danbates2/emonDC/emonDCmini/emonBike v0.2 BOARD BOTTOM.png

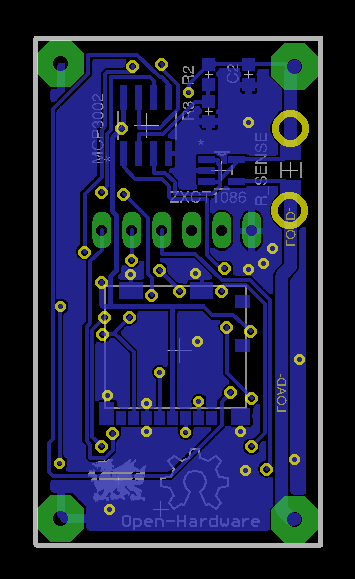
emonDCmini/emonBike v0.2 BOARD BOTTOM.png
