danbates2/emonDC/emonDCmini/emonBike v0.2 BOARD TOP.png

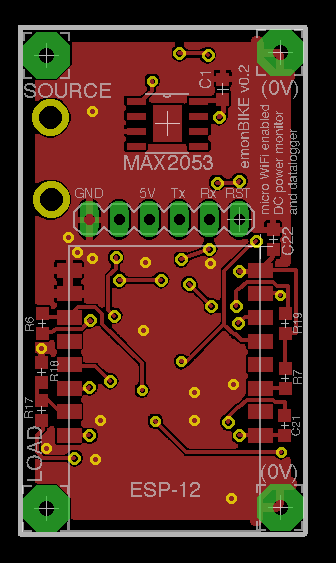
emonDCmini/emonBike v0.2 BOARD TOP.png
