danbates2/emonDC/emonDCmini/emonBike v0.2 SCHEMATIC.png

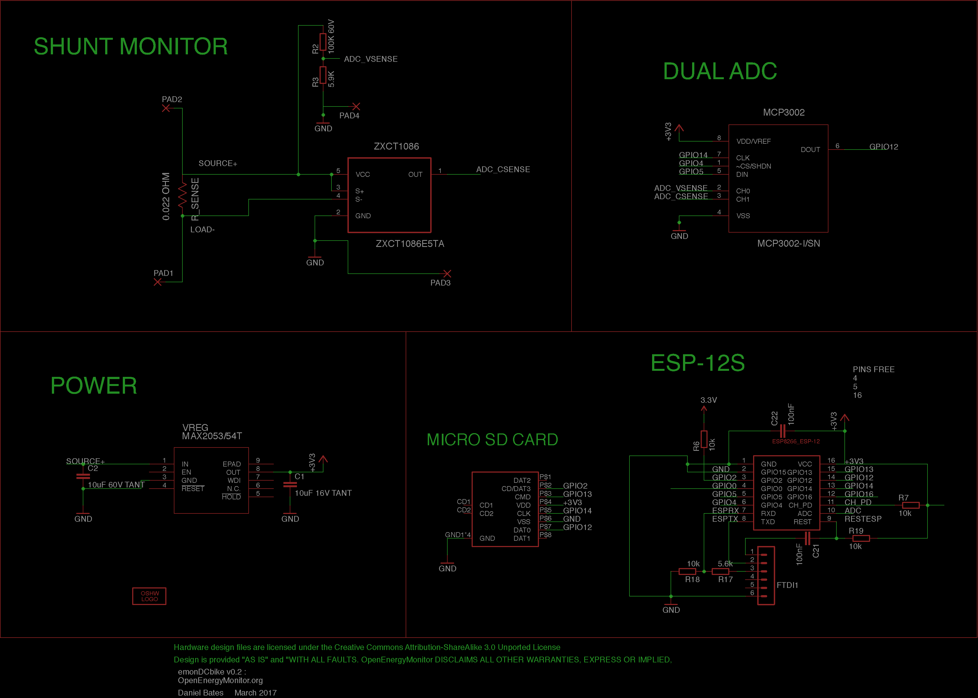
emonDCmini/emonBike v0.2 SCHEMATIC.png
