danbates2/emonDC/images/3dprinted_case_1.jpg

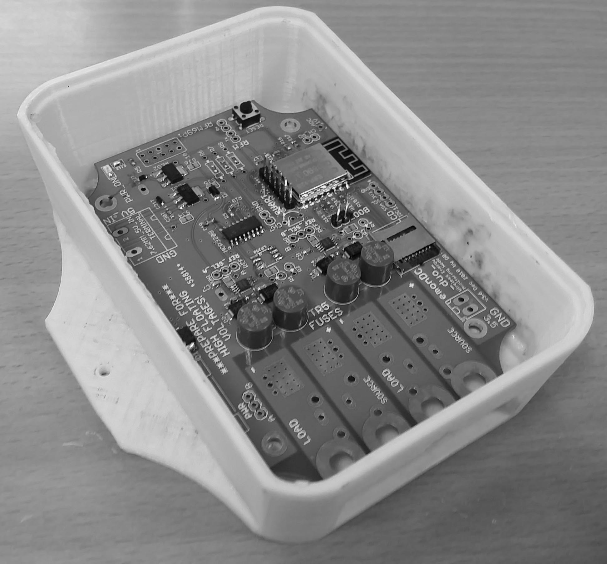
images/3dprinted_case_1.jpg
