danbates2/emonDC/images/buck_reg_blue.jpg

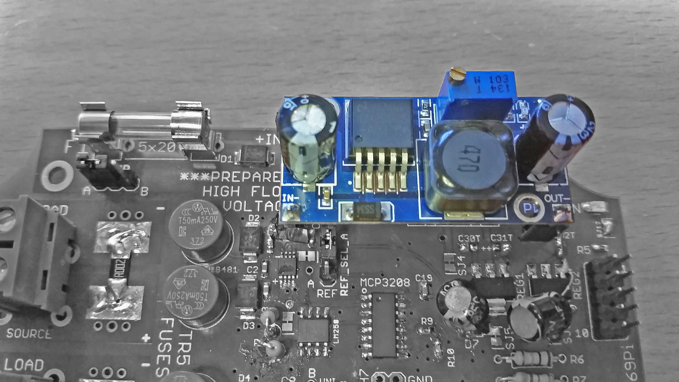
images/buck_reg_blue.jpg
