danbates2/emonDC/images/buck_reg_green.jpg

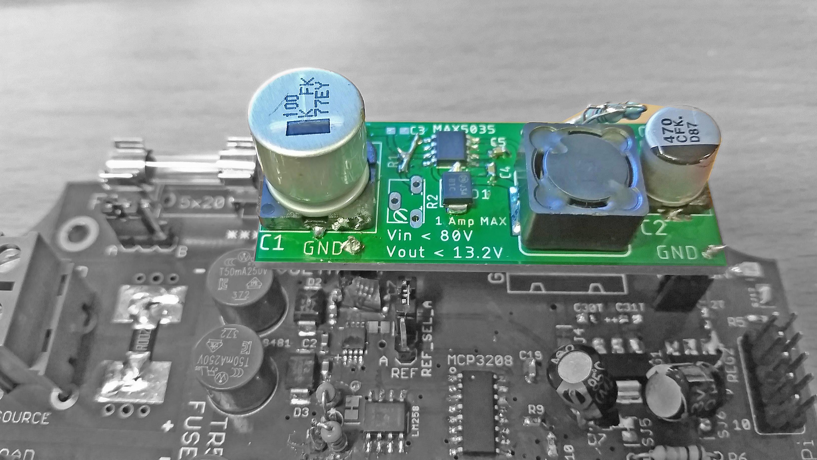
images/buck_reg_green.jpg
