danbates2/emonDC/images/buckreg-hysteresis.jpg

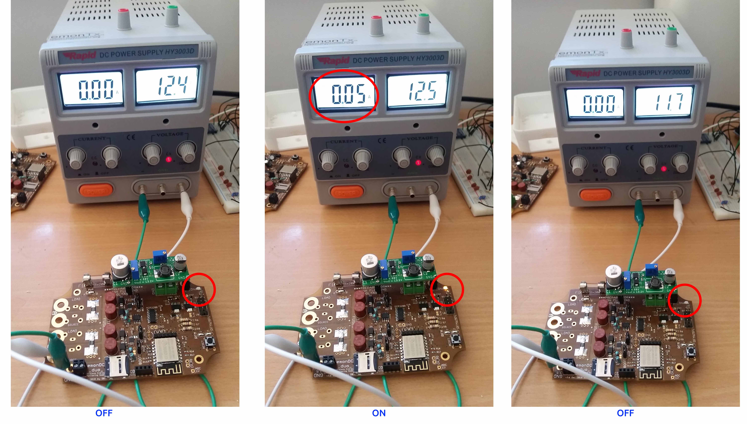
images/buckreg-hysteresis.jpg
