danbates2/emonDC/images/enclosures.jpg

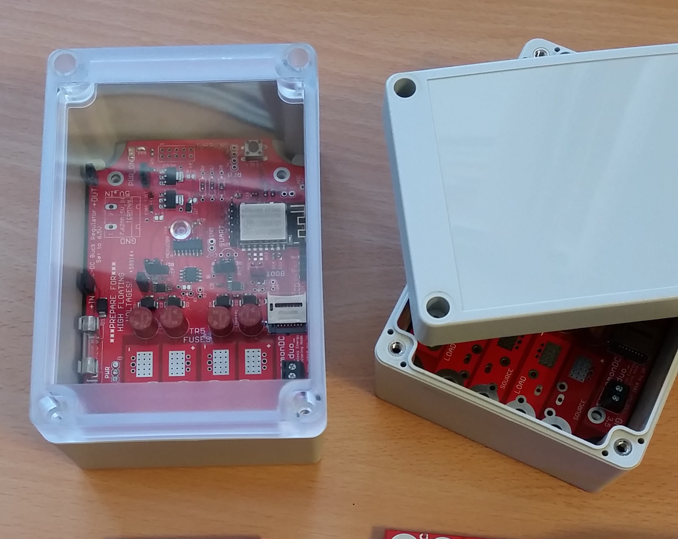
images/enclosures.jpg
