danbates2/emonDC/images/LM2596_dc-dc_buck_module.jpg

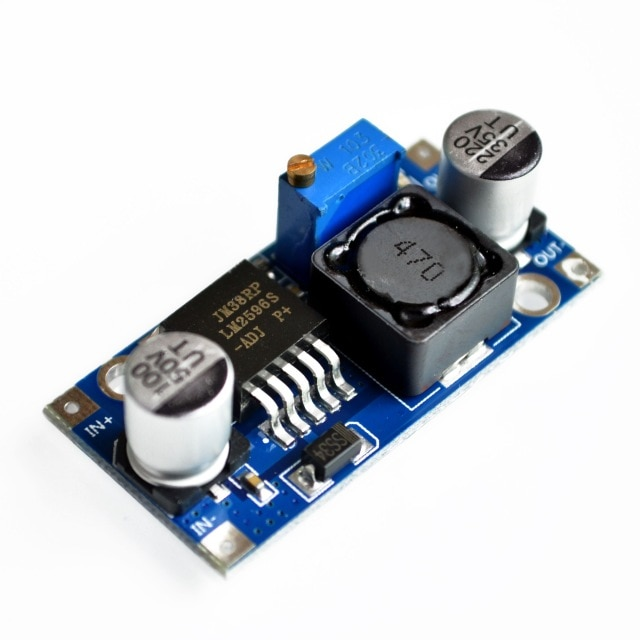
images/LM2596_dc-dc_buck_module.jpg
