danbates2/emonDC/images/shoot1/clear_enclosure_standing2.JPG

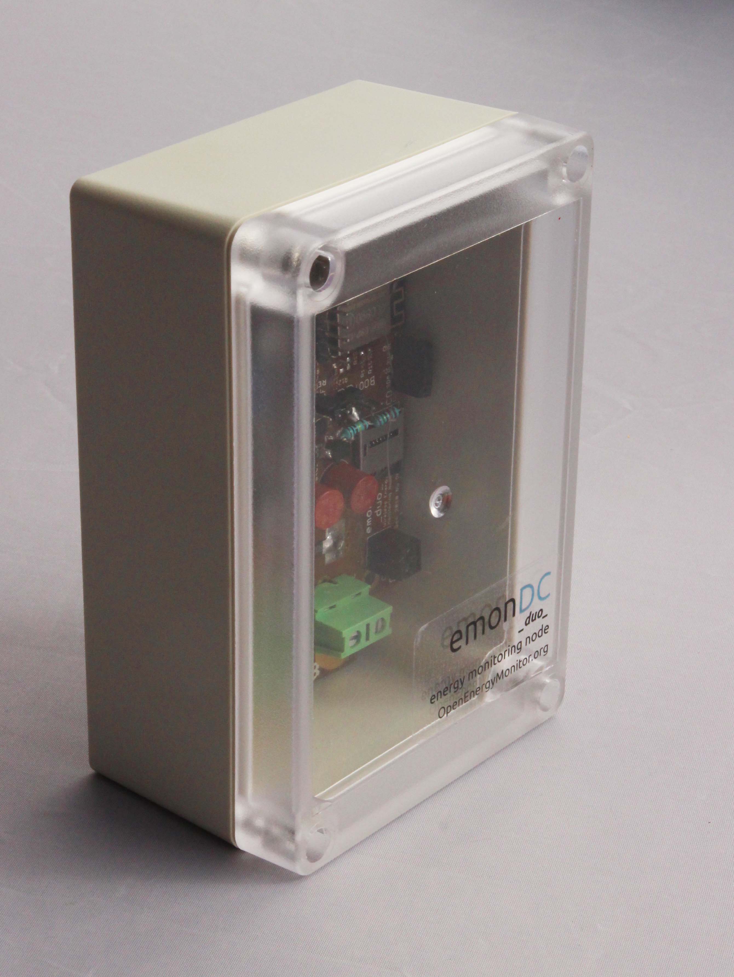
images/shoot1/clear_enclosure_standing2.JPG
