danbates2/emonDC/images/shoot1/clear_enclosure_standing.JPG

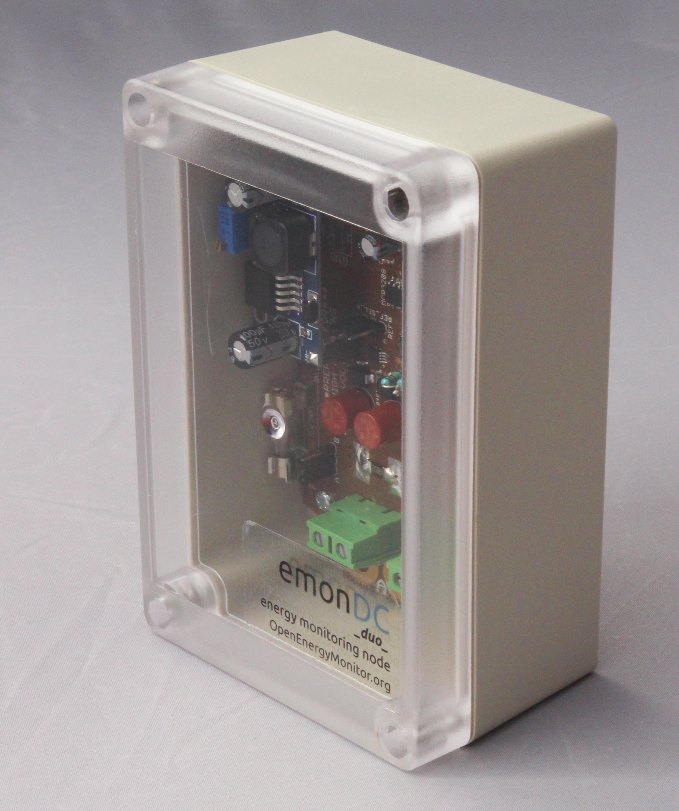
images/shoot1/clear_enclosure_standing.JPG
