danbates2/emonDC/images/shoot1/opaque_enclosure_standing.JPG

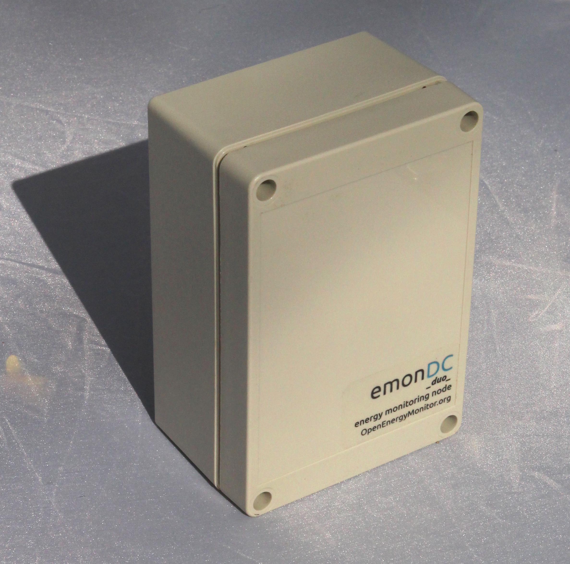
images/shoot1/opaque_enclosure_standing.JPG
