danbates2/emonDC/images/shoot1/v3.5_pcb_10.16mm_term_block.JPG

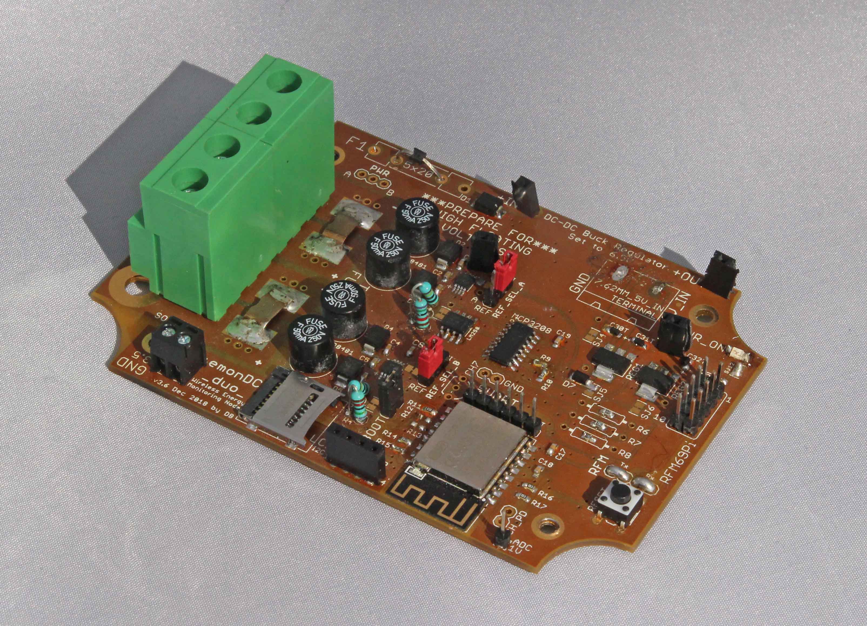
images/shoot1/v3.5_pcb_10.16mm_term_block.JPG
