danbates2/emonDC/images/shoot1/v3.6_pcb_rear.JPG

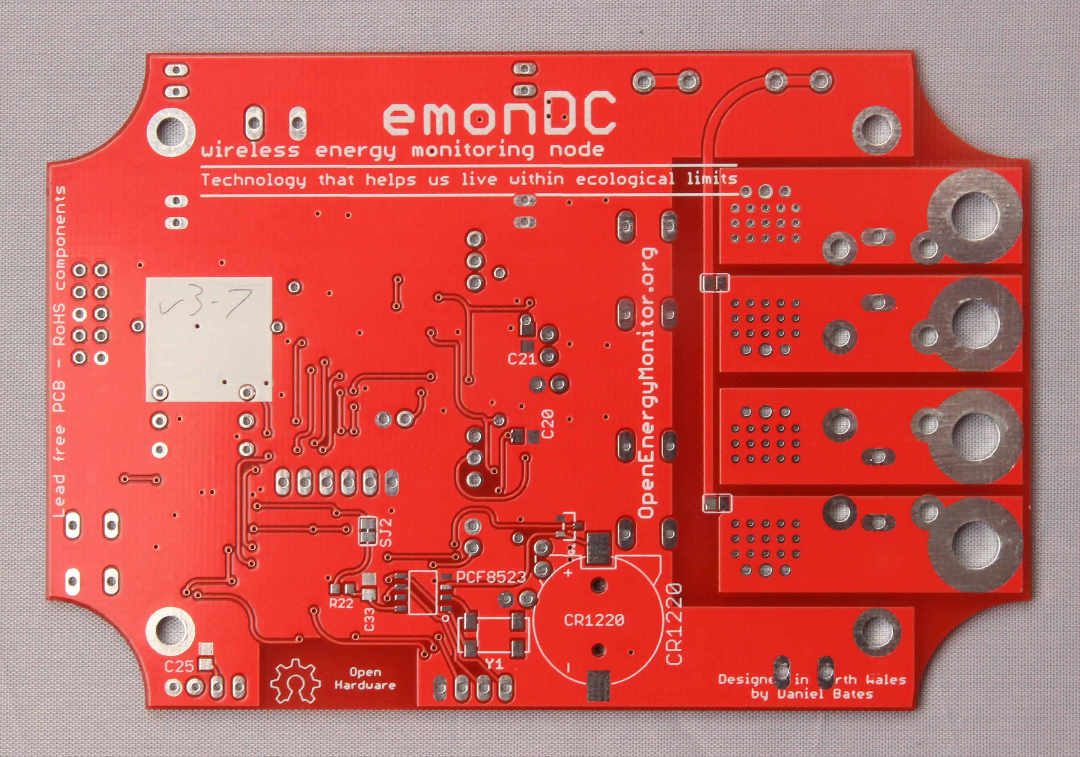
images/shoot1/v3.6_pcb_rear.JPG
