danbates2/emonDC/images/shoot1/v3.6_pcb_standard.JPG

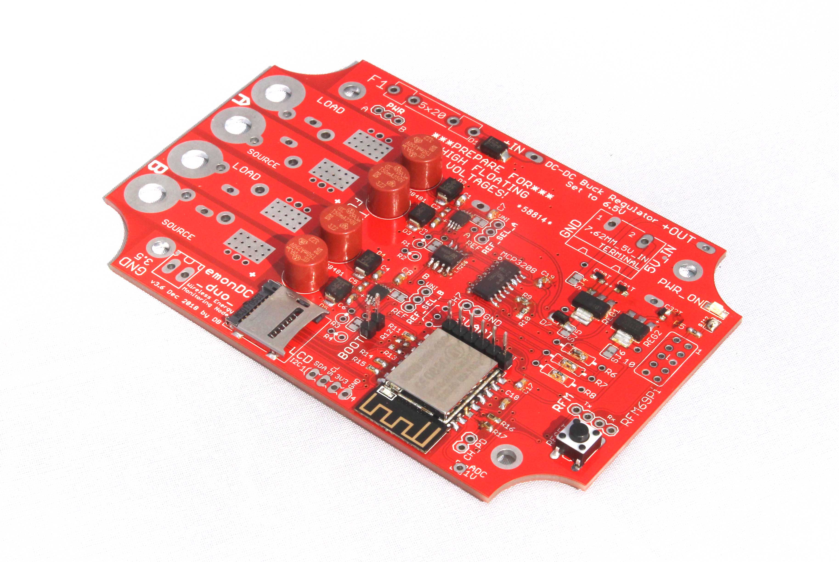
images/shoot1/v3.6_pcb_standard.JPG
