danbates2/emonDC/images/v3.6_overlay_5v.jpg

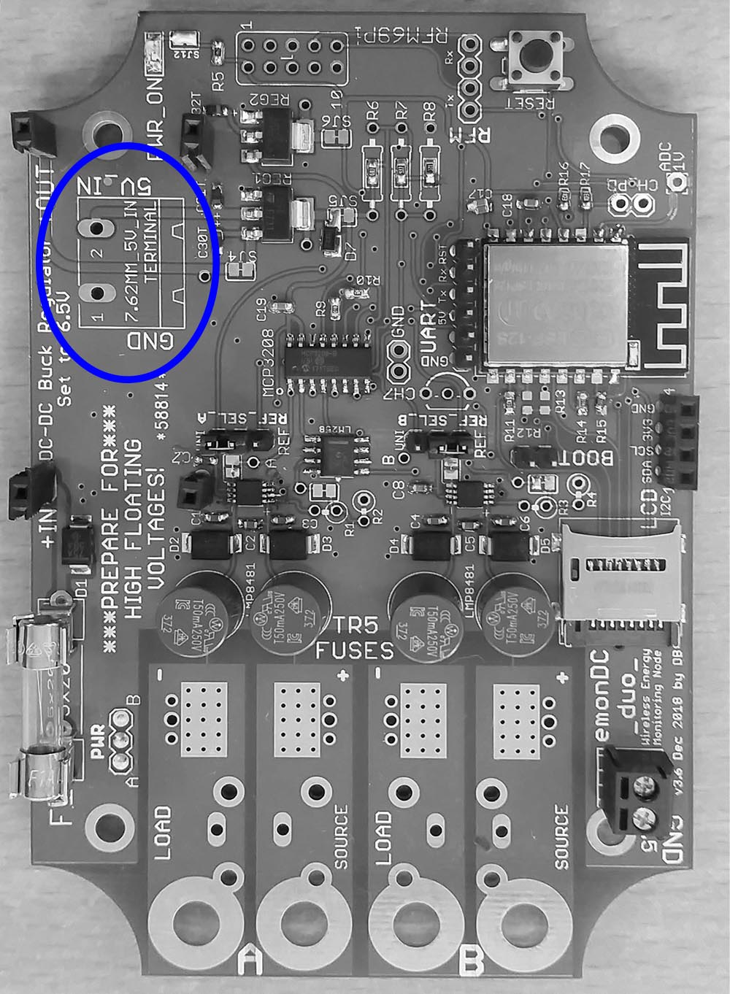
images/v3.6_overlay_5v.jpg
