danbates2/emonDC/images/v3.6_terms_7.62mm.jpg

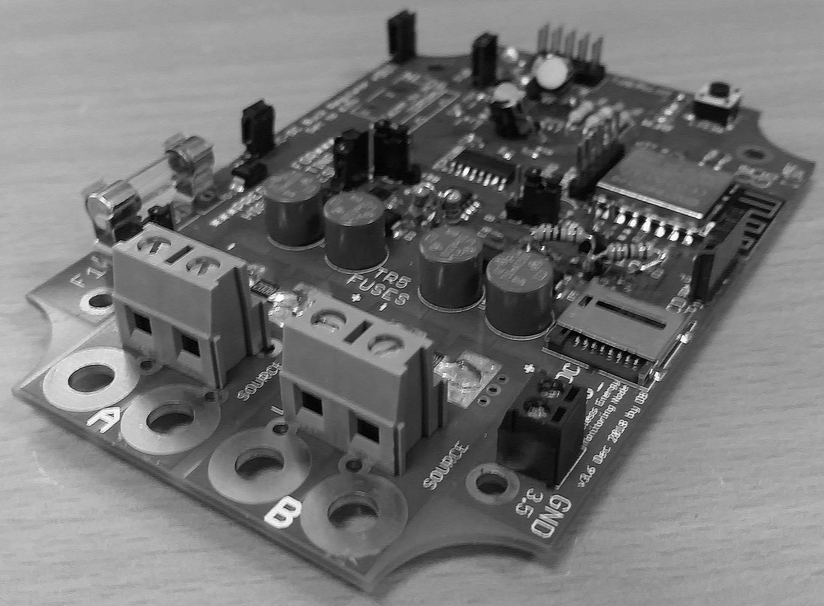
images/v3.6_terms_7.62mm.jpg
