danbates2/emonDC/images/v3.6_terms_10.16mm.jpg

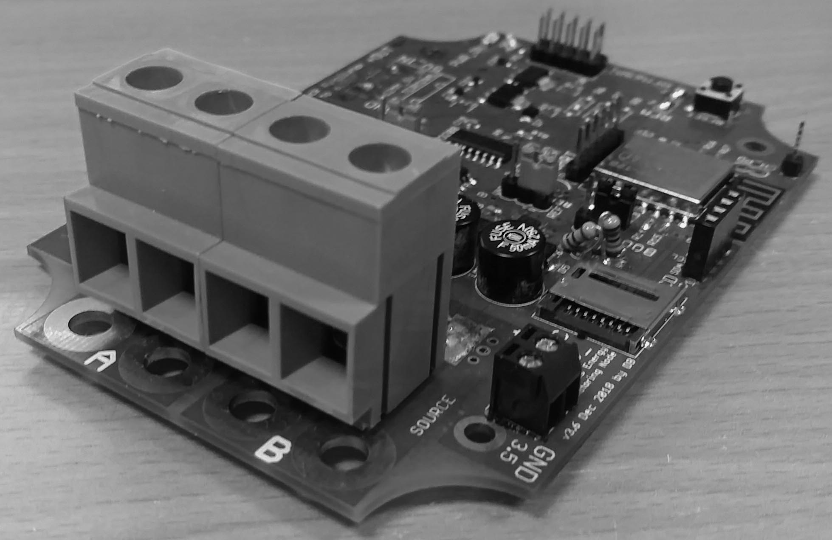
images/v3.6_terms_10.16mm.jpg
