danbates2/emonDC/images/v3.6_terms_bare.jpg

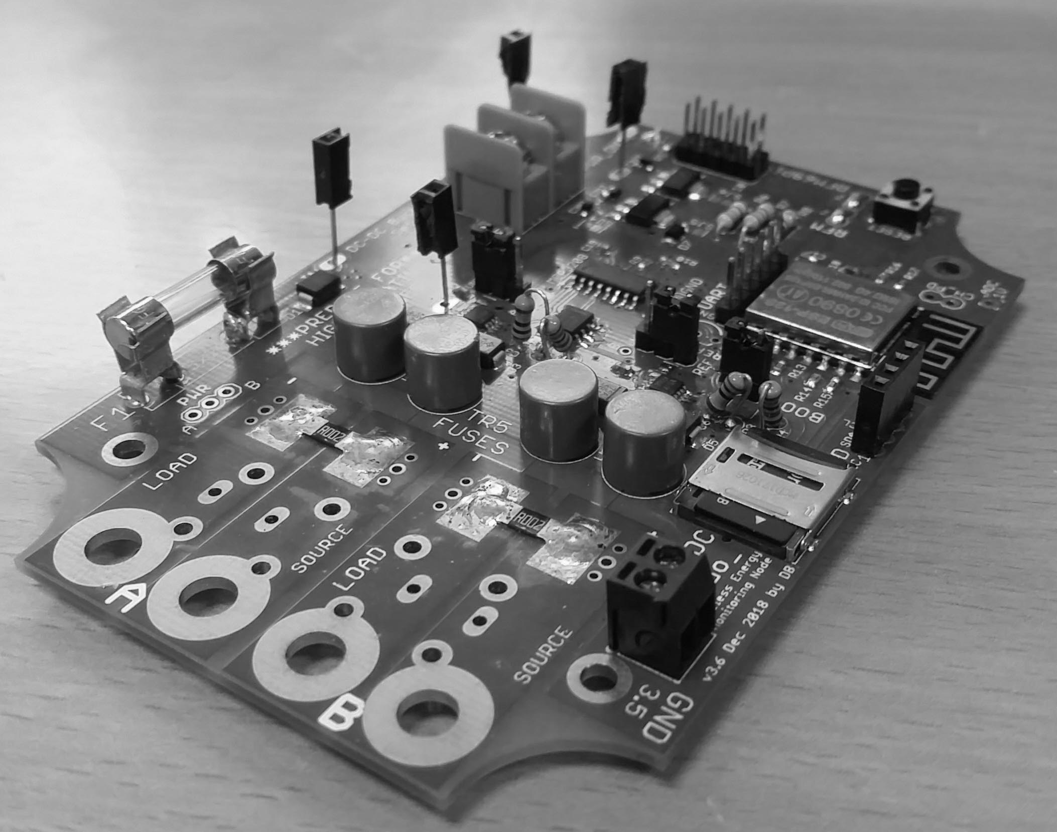
images/v3.6_terms_bare.jpg
