danbates2/emonDC/images/v3.6_terms_ring.jpg

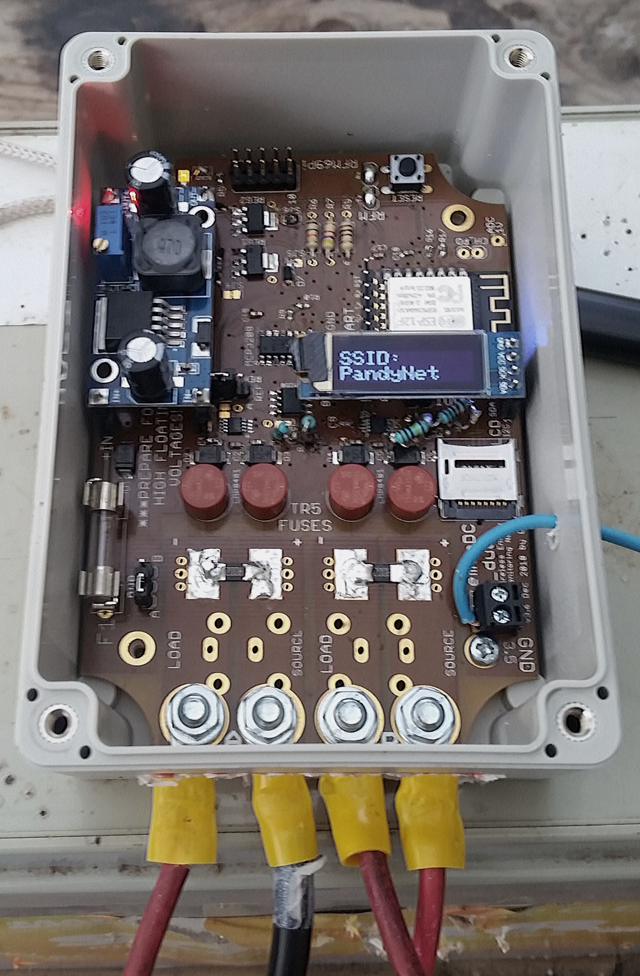
images/v3.6_terms_ring.jpg
