danbates2/emonDC/images/v3.6_terms_v5input_block.jpg

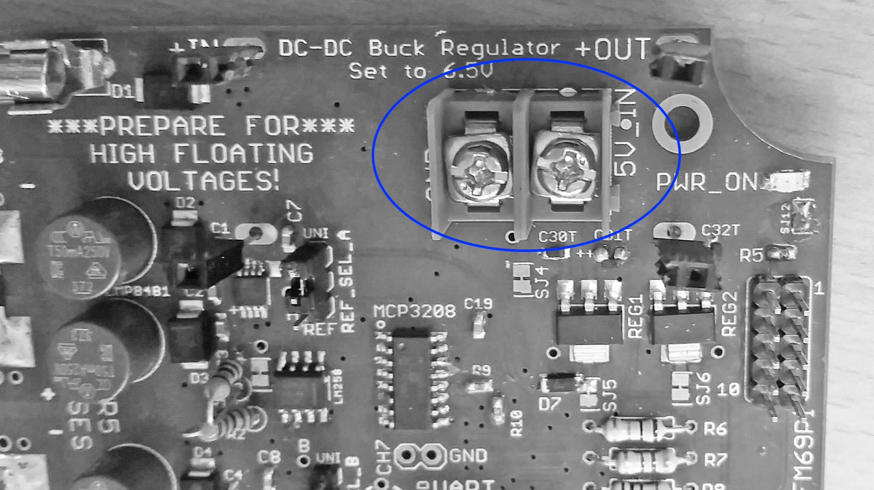
images/v3.6_terms_v5input_block.jpg
