danbates2/emonDC/projects/ACS7** PFF Breakout/baz current monitor acs7**.jpeg

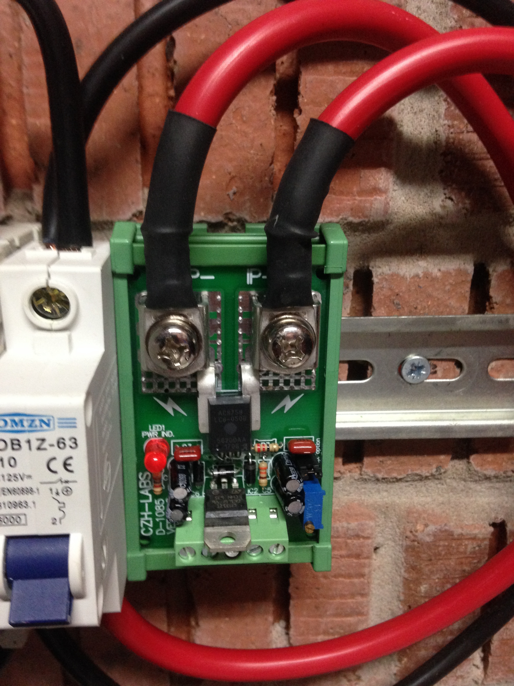
projects/ACS7** PFF Breakout/baz current monitor acs7**.jpeg
