danbates2/emonDC/projects/emonDCduo/hardware/esp8266/v3.4 images/schematic v3.4.png

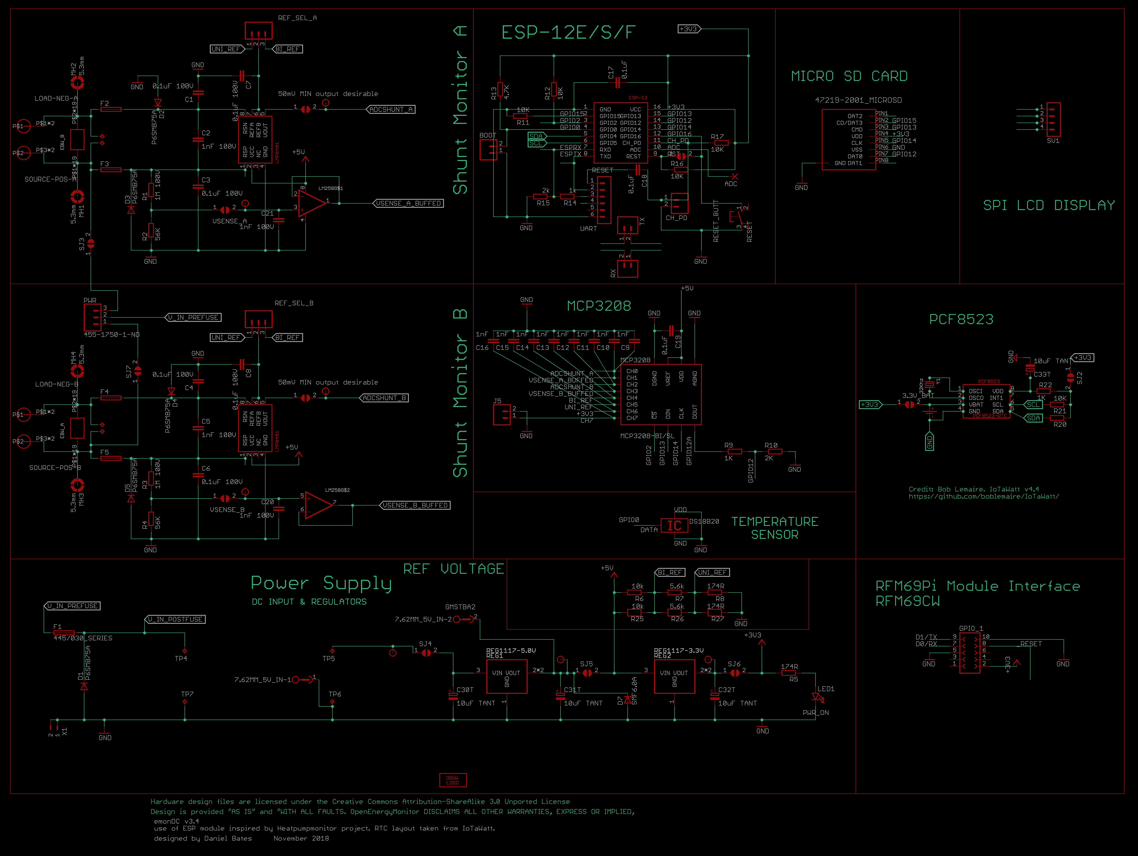
projects/emonDCduo/hardware/esp8266/v3.4 images/schematic v3.4.png
