danbates2/emonDC/projects/emonDCduo/hardware/esp8266/v3.4 images/top side emonDCduo v3.4.jpg

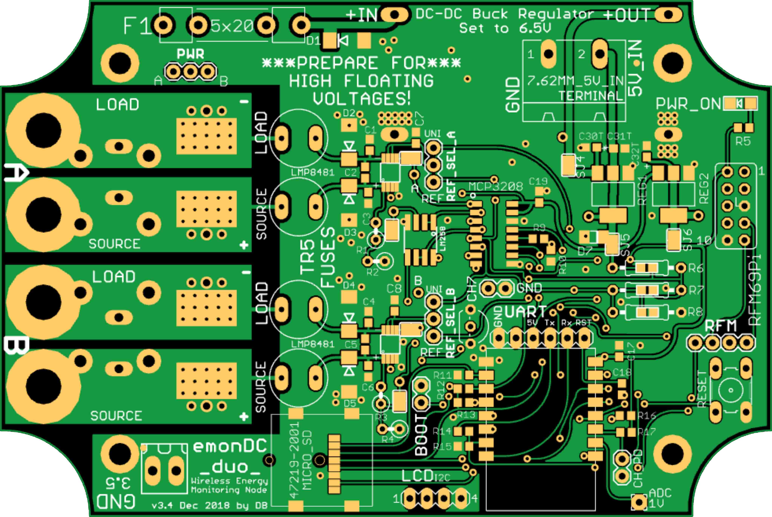
projects/emonDCduo/hardware/esp8266/v3.4 images/top side emonDCduo v3.4.jpg
