danbates2/emonDC/projects/isoHV/firmware/feather_Feather_M0_RFM95_v1.2-1.png

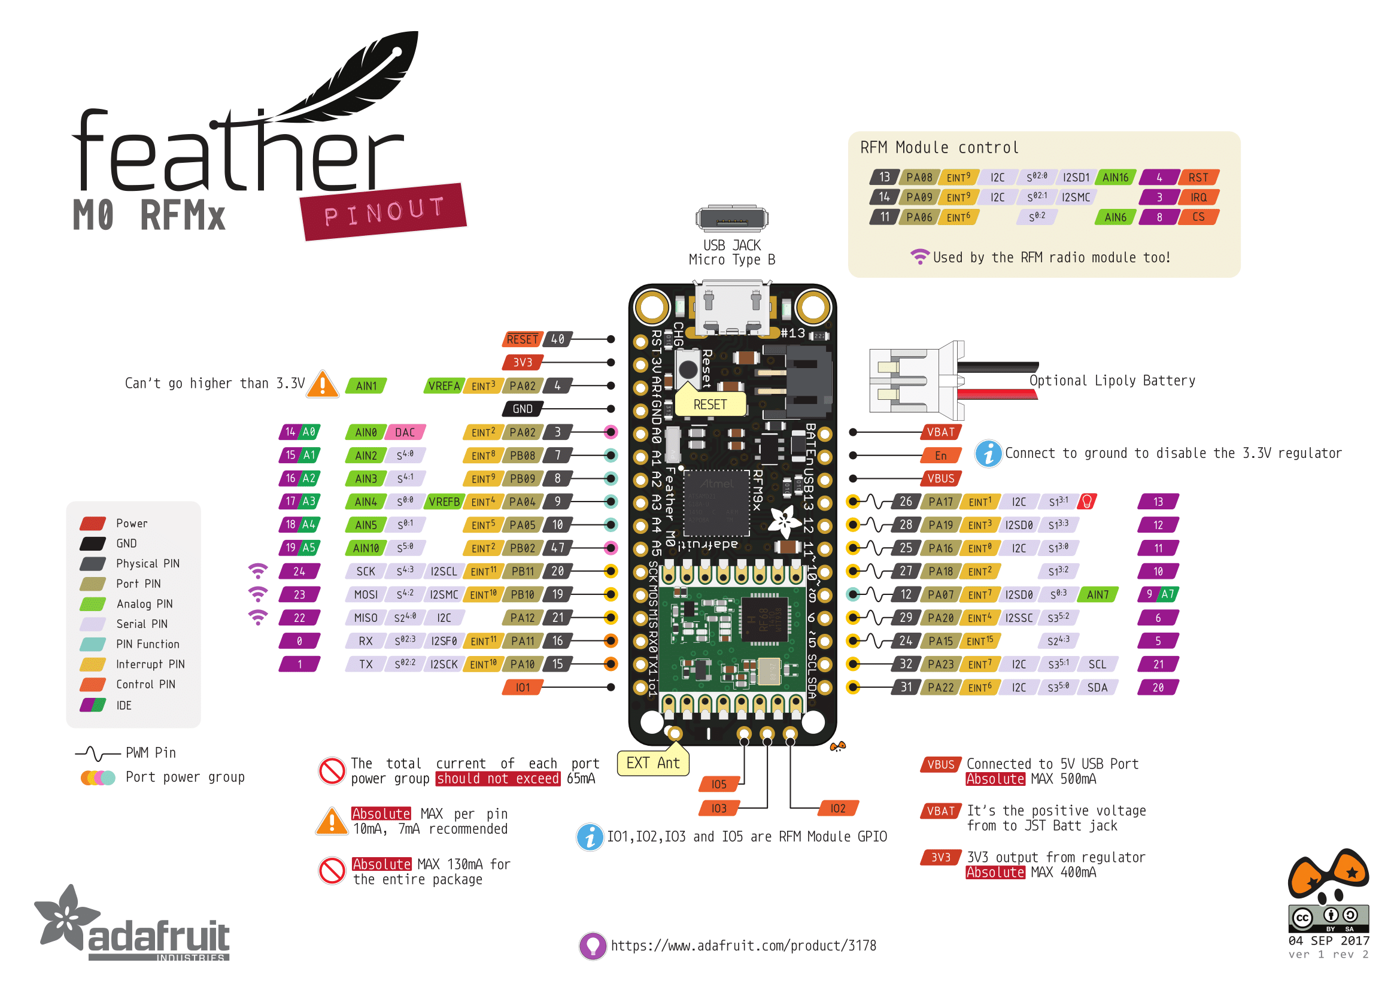
projects/isoHV/firmware/feather_Feather_M0_RFM95_v1.2-1.png
