danbates2/emonDC/projects/isoHV/hardware/v0.6 board top.png

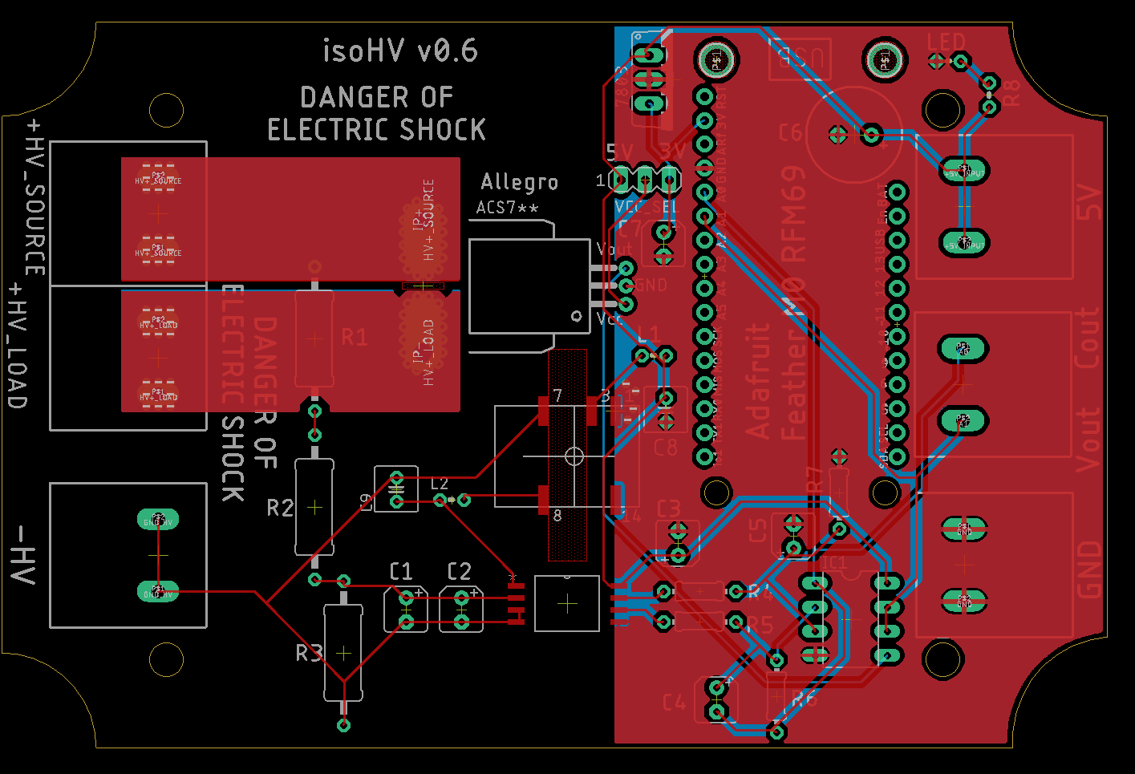
projects/isoHV/hardware/v0.6 board top.png
