danbates2/emonDC/projects/isoHV/hardware/v0.6 sch.png

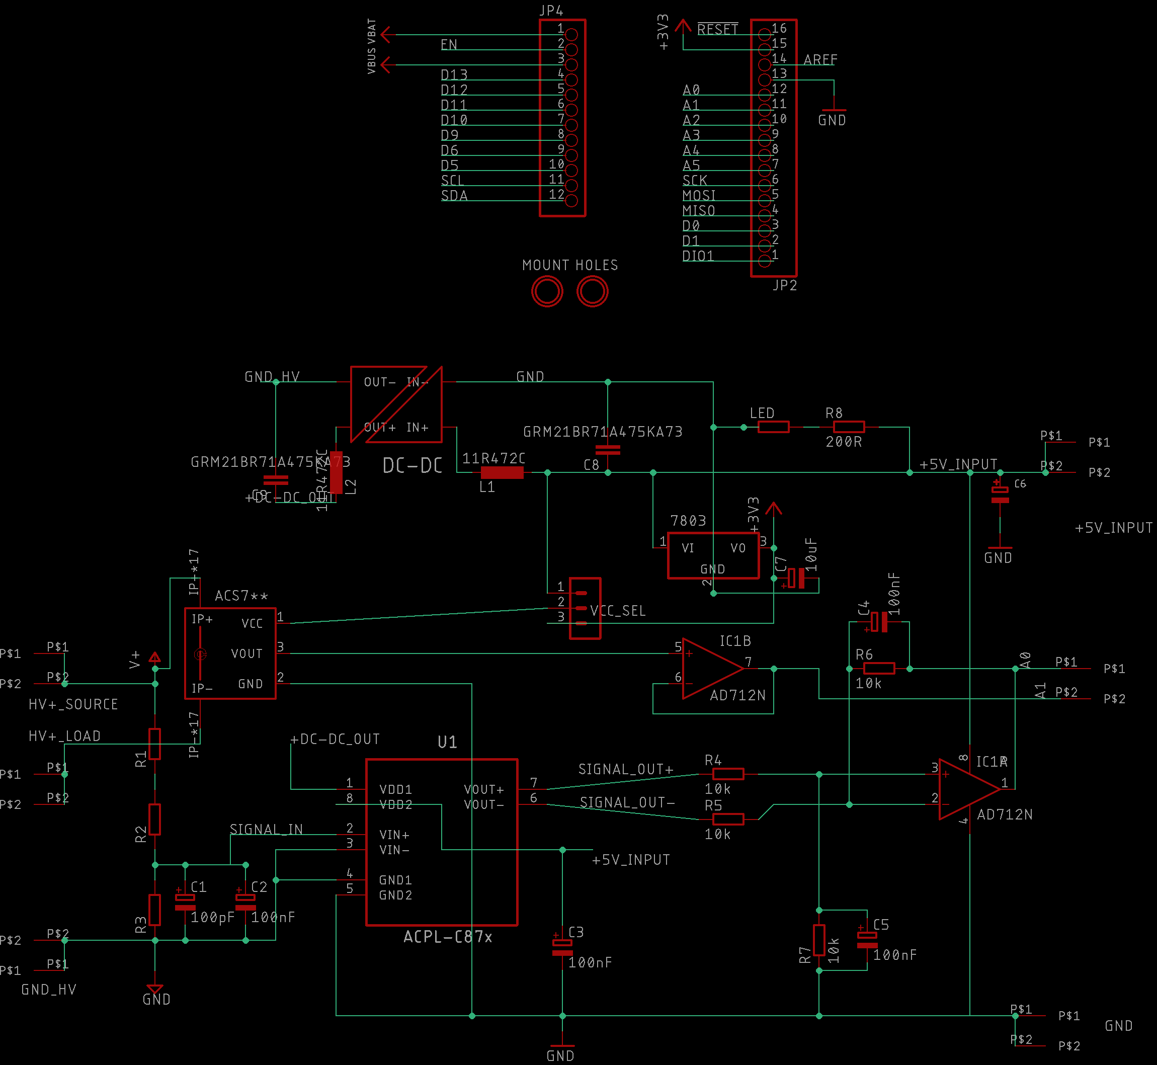
projects/isoHV/hardware/v0.6 sch.png
