danbates2/emonDC/projects/isoHV/images/isoHV v0.6 single.jpg

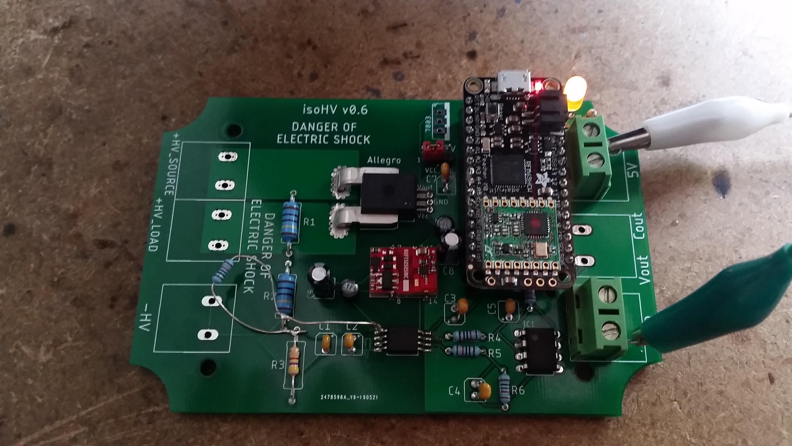
projects/isoHV/images/isoHV v0.6 single.jpg
