danbates2/emonDC/projects/isoHV/images/isoHV v0.7 dual.jpg

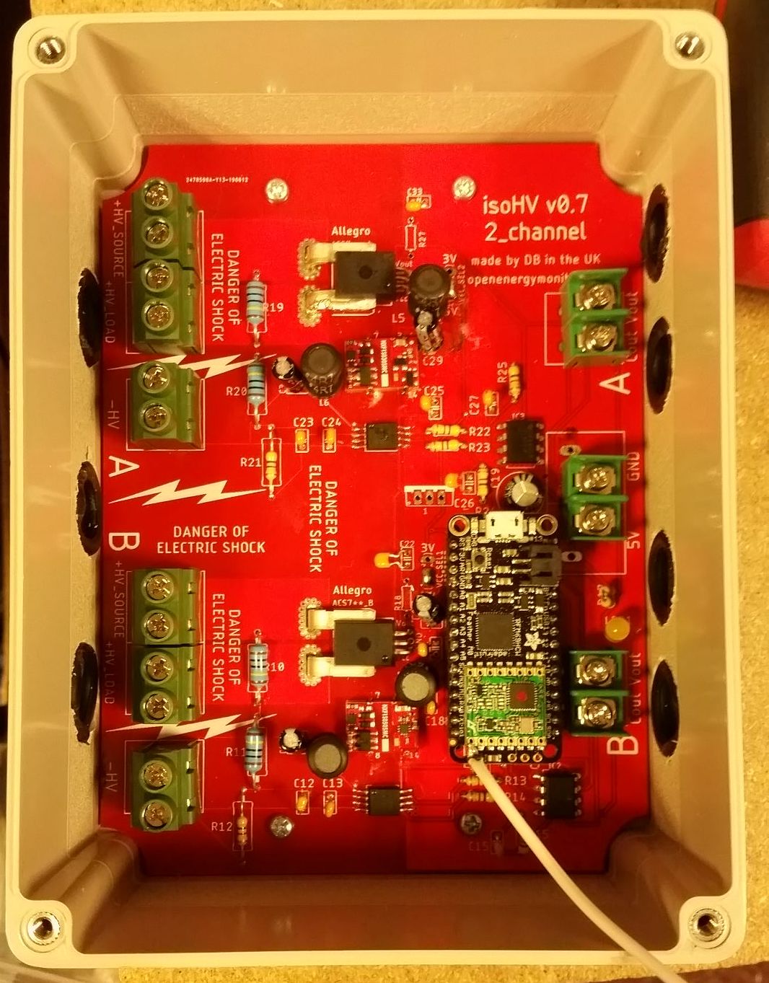
projects/isoHV/images/isoHV v0.7 dual.jpg
