danbates2/emonDC/projects/ACS7** PFF Breakout/acs770 testing photos burnt board solar wagon/2.jpg

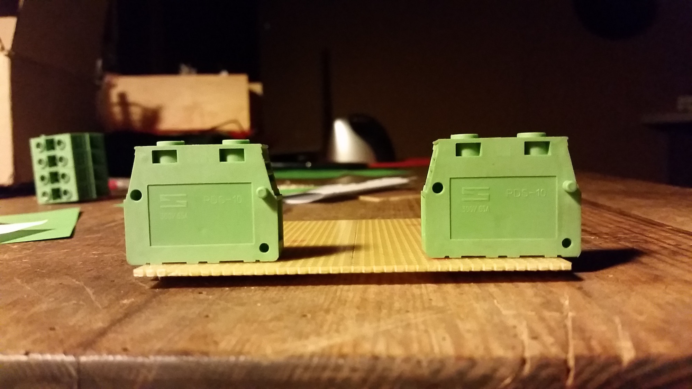
projects/ACS7** PFF Breakout/acs770 testing photos burnt board solar wagon/2.jpg
