danbates2/emonDC/projects/ACS7** PFF Breakout/acs770 testing photos burnt board solar wagon/3.jpg

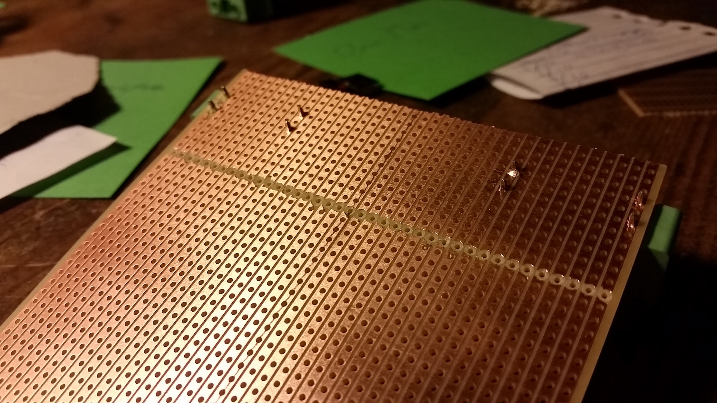
projects/ACS7** PFF Breakout/acs770 testing photos burnt board solar wagon/3.jpg
