danbates2/emonDC/projects/ACS7** PFF Breakout/acs770 testing photos burnt board solar wagon/6 acs770 consumption.jpg

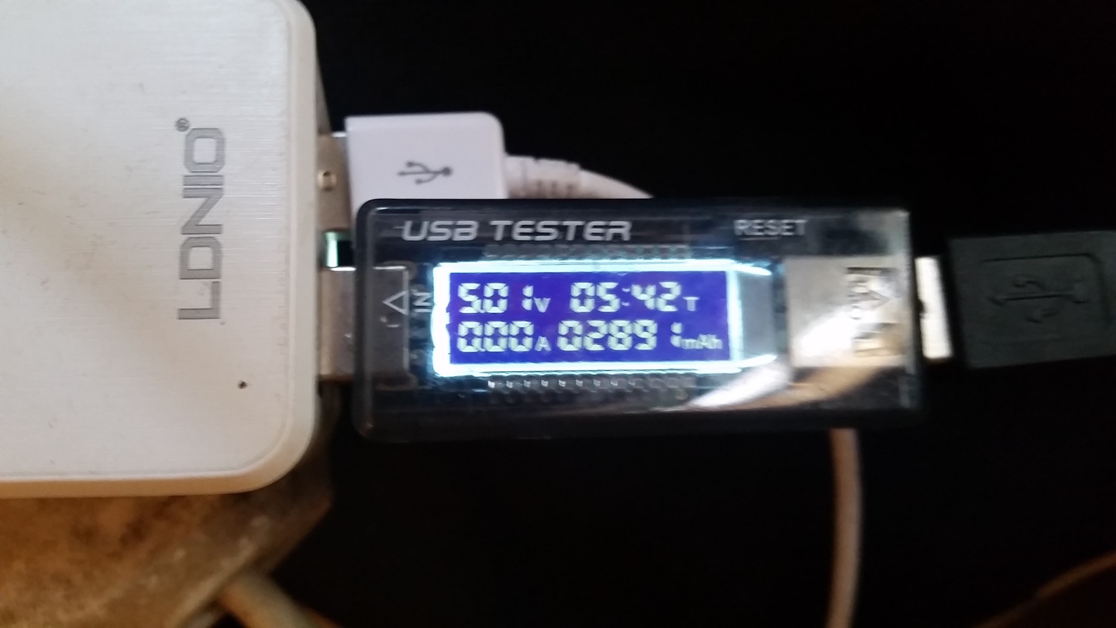
projects/ACS7** PFF Breakout/acs770 testing photos burnt board solar wagon/6 acs770 consumption.jpg
