danbates2/emonDC/projects/ACS7** PFF Breakout/acs770 testing photos burnt board solar wagon/8 current.jpg

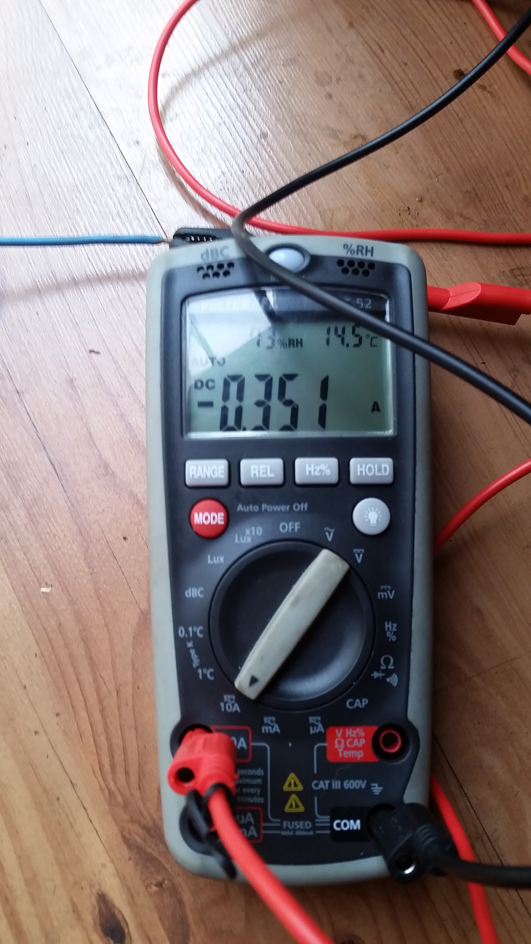
projects/ACS7** PFF Breakout/acs770 testing photos burnt board solar wagon/8 current.jpg
