danbates2/emonDC/projects/ACS7** PFF Breakout/acs770 testing photos burnt board solar wagon/9 output voltage no current.jpg

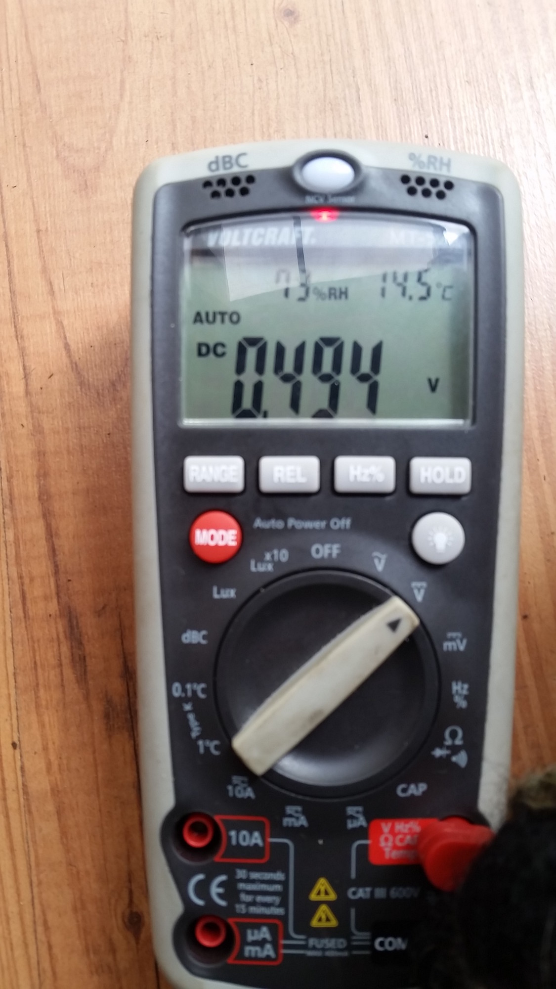
projects/ACS7** PFF Breakout/acs770 testing photos burnt board solar wagon/9 output voltage no current.jpg
