danbates2/emonDC/projects/emonDCduo/hardware/esp8266/thermal test/front thermal test/DC_4104.jpg

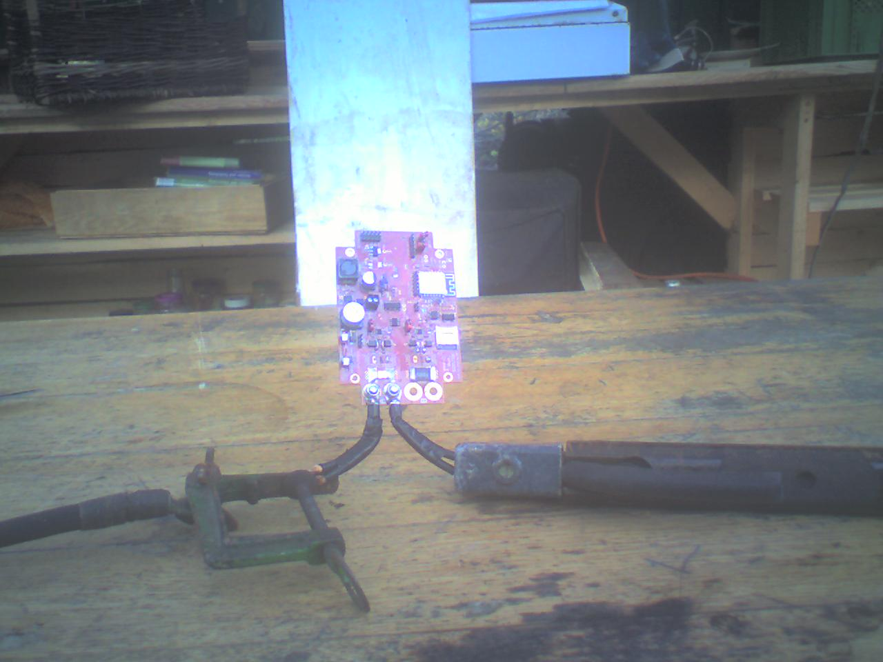
projects/emonDCduo/hardware/esp8266/thermal test/front thermal test/DC_4104.jpg
