danbates2/emonDC/projects/emonDCduo/hardware/esp8266/thermal test/front thermal test/IR_4121.jpg

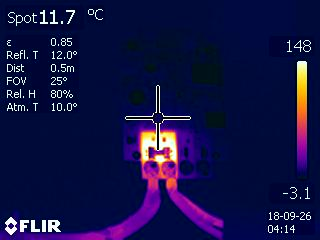
projects/emonDCduo/hardware/esp8266/thermal test/front thermal test/IR_4121.jpg
