danbates2/emonDC/projects/emonDCduo/hardware/esp8266/thermal test/front thermal test/IR_4123.jpg

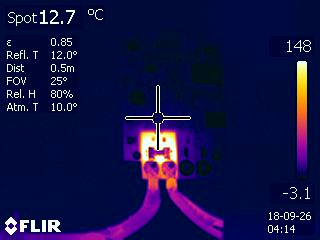
projects/emonDCduo/hardware/esp8266/thermal test/front thermal test/IR_4123.jpg
