danbates2/emonDC/projects/emonDCduo/hardware/esp8266/thermal test/pics/2018-11-26 09.40.13.png

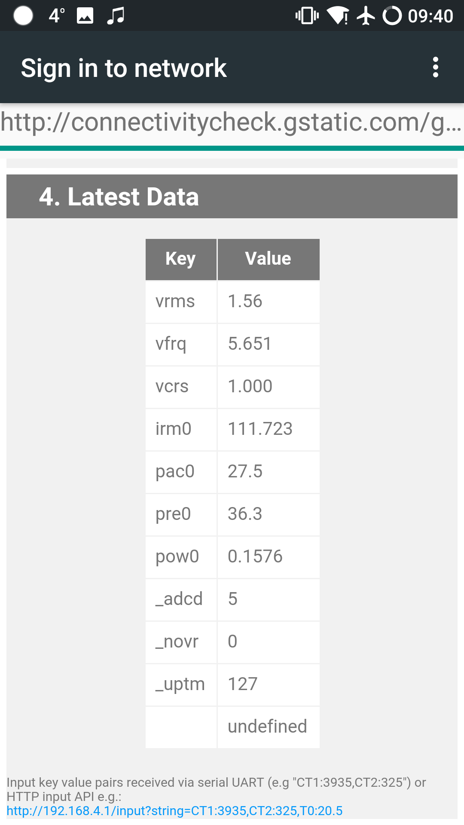
projects/emonDCduo/hardware/esp8266/thermal test/pics/2018-11-26 09.40.13.png
