danbates2/emonDC/projects/emonDCduo/hardware/esp8266/thermal test/pics/2018-12-08 10.13.19.jpg

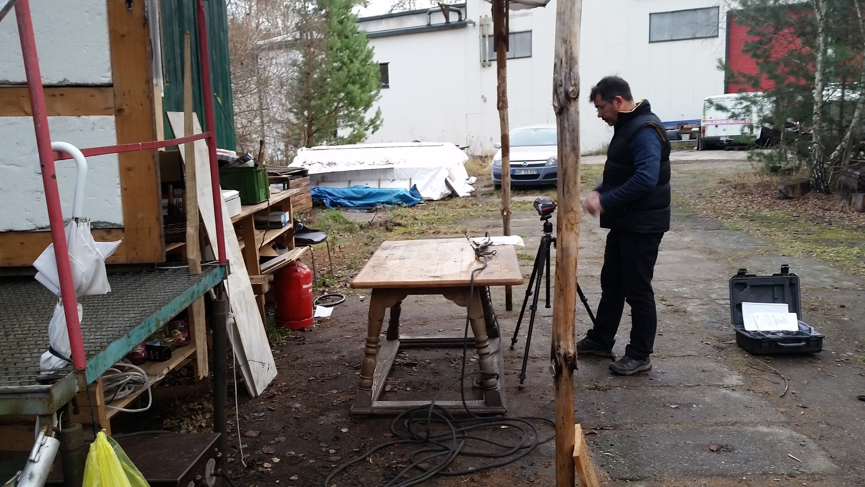
projects/emonDCduo/hardware/esp8266/thermal test/pics/2018-12-08 10.13.19.jpg
