danbates2/emonDC/projects/emonDCduo/hardware/esp8266/thermal test/pics/2018-12-08 10.51.02.jpg

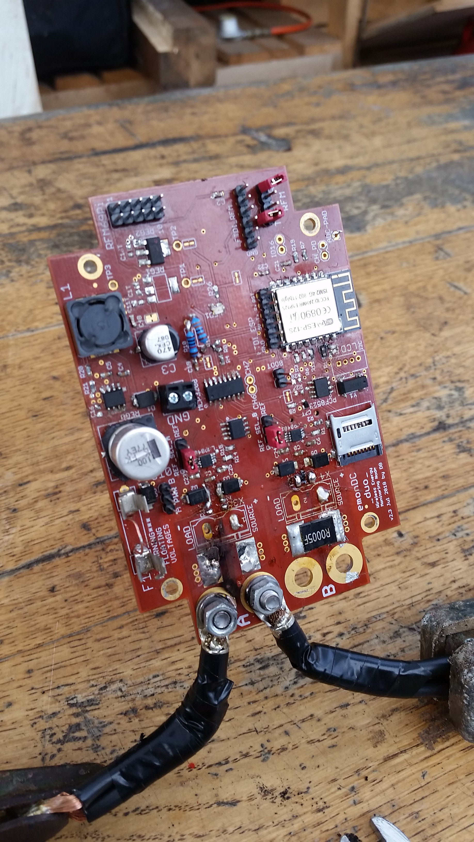
projects/emonDCduo/hardware/esp8266/thermal test/pics/2018-12-08 10.51.02.jpg
