danbates2/emonDC/projects/emonDCduo/hardware/esp8266/thermal test/rear thermal test/DC_4130.jpg

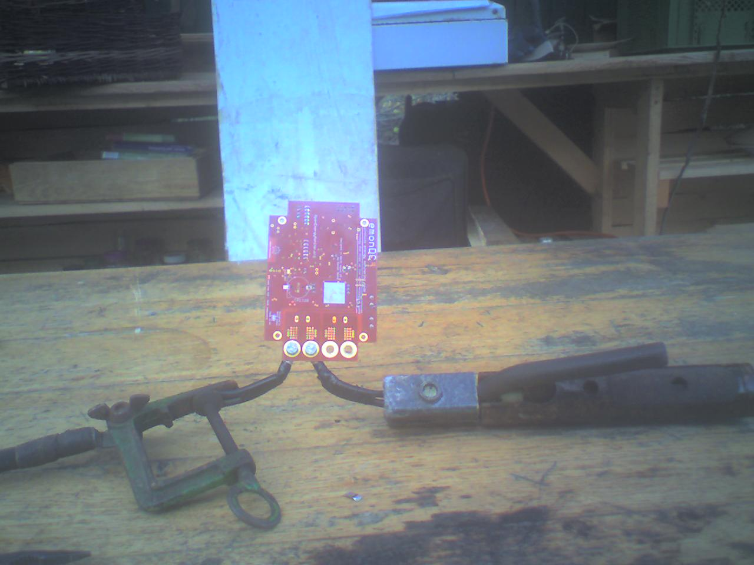
projects/emonDCduo/hardware/esp8266/thermal test/rear thermal test/DC_4130.jpg
