danbates2/emonDC/projects/emonDCduo/hardware/esp8266/thermal test/rear thermal test/IR_4133.jpg

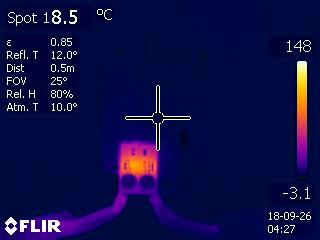
projects/emonDCduo/hardware/esp8266/thermal test/rear thermal test/IR_4133.jpg
