danbates2/emonDC/calculators/emonDC_ACDinput_LTSpice/emonDC_ACDinput_LTSpice.asc

C1: cap; 20pF
C2: cap; 7pF
R1: res; 47k
R2: res; 3.3k
R3: res; 1k
S1: sw; MYSW
V1: voltage; 76
V2: voltage; PULSE(0 5 0.001 0.0001 0.0001 .001 3 2)
Named nets: 0
.tran 0 2us 0 0.01us
