danbates2/emonDC/projects/isoHV/hardware/isoHV v0.7.brd

## EAGLE design projects/isoHV/hardware/isoHV v0.7.brd (2019-07-09)

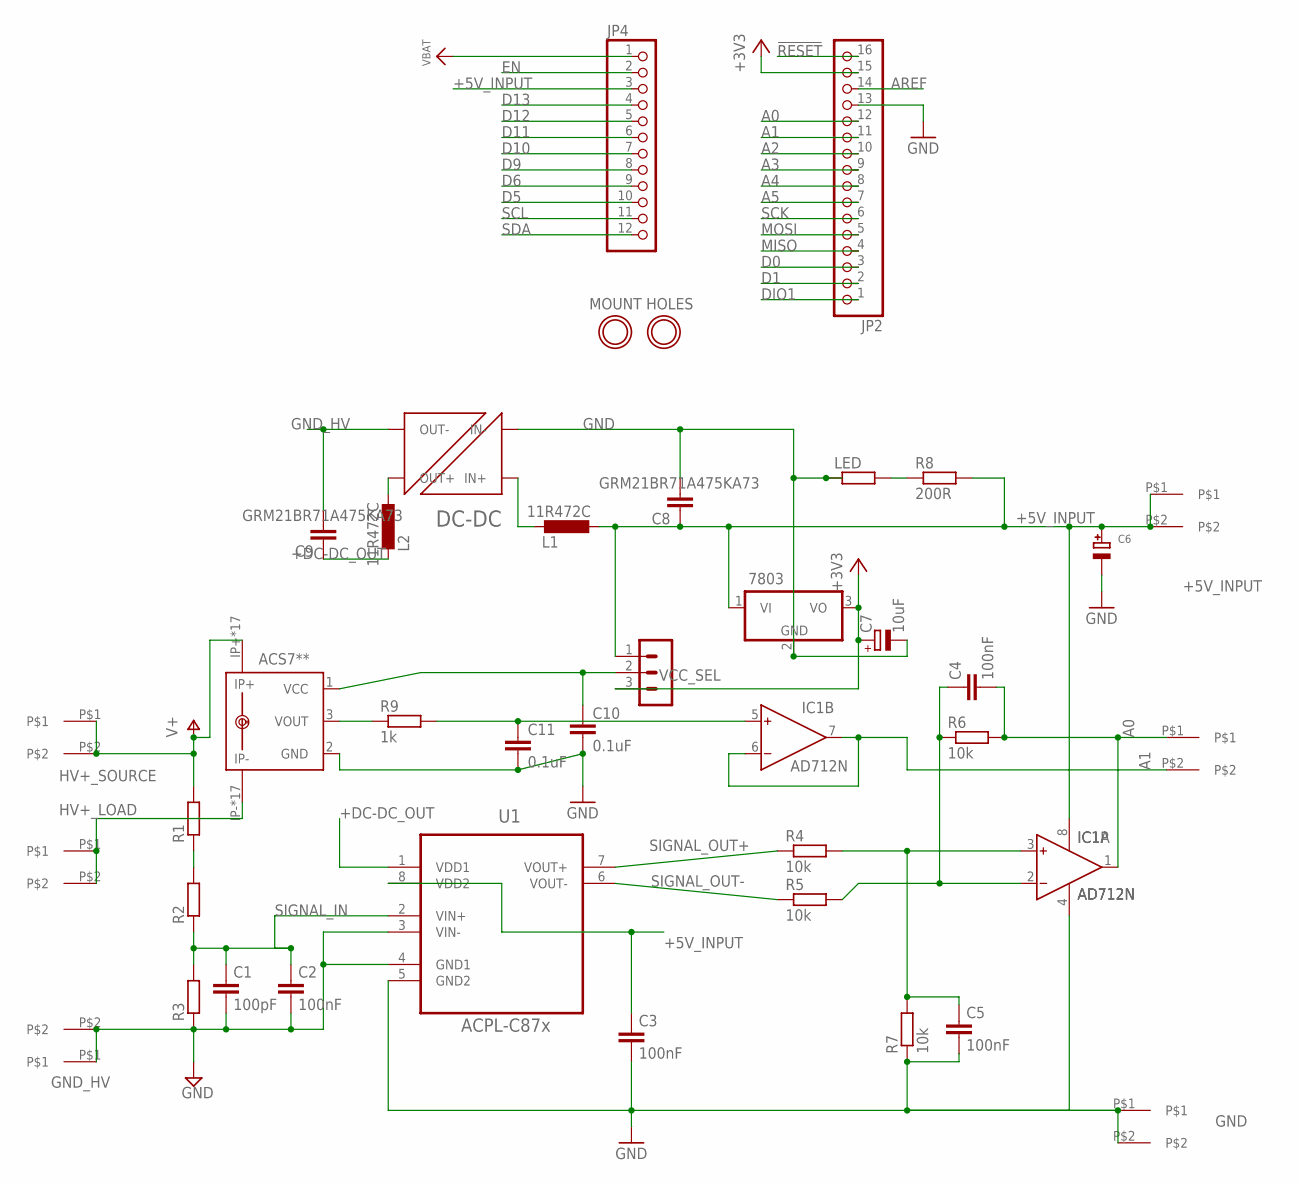
[picture p104: schematic isoHV v0.7.sch]

Parts:
7803: 7805TV; TO220V
ACS7**: ACS758KCB-150B-PFF-T; CB-PFF; MPN ACS7**
C1: 100pF; C025-025X050
C2, C3, C4, C5: 100nF; C025-025X050
C6: CAP_ELECTROLYTICPTH_3.5MMGRID_10MMDIA; CELEC_3.5MM_10MM
C7: 10uF; B45181A
C8: GRM21BR71A475KA73; C025-025X050
C9: GRM21BR71A475KA73; C025-050X050
C10, C11: 0.1uF; C025-025X050
IC1: AD712N; DIL08
JP2: HEADER-1X16ROUND; 1X16_ROUND
JP4: HEADER-1X12; 1X12_ROUND
L1, L2: 11R472C; 0204V
LED: R-EU_0204/2V; 0204V
R1, R2, R3: R-EU_0411/15; 0411/15
R4, R5, R6, R7: 10k; 0204/7
R8: 200R; 0204V
R9: 1k; 0204/7
U1: ACPL-C87x; SOIC127P1150X330-8N
U$1, U$2, U$3, U$4, U$5, U$6: 7.62MM_TERMINAL_BLOCK; 7.62MM
U$7: NXF1
U$12, U$13: MOUNTINGHOLE2.5; MOUNTINGHOLE_2.5_PLATED
VCC_SEL: MA03-1

Connections:
!RESET: JP2.16
+3V3: 7803.3 (VO), C7.+, JP2.15, VCC_SEL.3
+5V_INPUT: 7803.1 (VI), C3.1, C6.+, C8.1, IC1.8 (V+), JP4.3, L1.2, R8.2, U1.8 (VDD2), U$3.P$1, U$3.P$2, VCC_SEL.1
+DC-DC_OUT: C9.1, L2.1, U1.1 (VDD1)
A0: C4.2, IC1.1 (OUT), JP2.12, R6.2, U$5.P$1
A1: IC1.6 (IN-), IC1.7 (OUT), JP2.11, U$5.P$2
A2: JP2.10
A3: JP2.9
A4: JP2.8
A5: JP2.7
AREF: JP2.14
D0: JP2.3
D1: JP2.2
D5: JP4.10
D6: JP4.9
D9: JP4.8
D10: JP4.7
D11: JP4.6
D12: JP4.5
D13: JP4.4
DIO1: JP2.1
EN: JP4.2
GND: 7803.2 (GND), ACS7**.2 (GND), C3.2, C5.2, C6.-, C7.-, C8.2, C10.2, C11.2, IC1.4 (V-), JP2.13, LED.1, R7.1, U1.5 (GND2), U$4.P$1, U$4.P$2, U$7.P$1 (IN-)
GND_HV: C1.2, C2.2, C9.2, R3.1, U1.3 (VIN-), U1.4 (GND1), U$2.P$1, U$2.P$2, U$7.P$7 (OUT-)
HV+_LOAD: ACS7**.IP-, ACS7**.IP-@2 (IP-), ACS7**.IP-@3 (IP-), ACS7**.IP-@4 (IP-), ACS7**.IP-@5 (IP-), ACS7**.IP-@6 (IP-), ACS7**.IP-@7 (IP-), ACS7**.IP-@8 (IP-), ACS7**.IP-@9 (IP-), ACS7**.IP-@10 (IP-), ACS7**.IP-@11 (IP-), ACS7**.IP-@12 (IP-), ACS7**.IP-@13 (IP-), ACS7**.IP-@14 (IP-), ACS7**.IP-@15 (IP-), ACS7**.IP-@16 (IP-), ACS7**.IP-@17 (IP-), U$6.P$1, U$6.P$2
HV+_SOURCE: ACS7**.IP+, ACS7**.IP+@2 (IP+), ACS7**.IP+@3 (IP+), ACS7**.IP+@4 (IP+), ACS7**.IP+@5 (IP+), ACS7**.IP+@6 (IP+), ACS7**.IP+@7 (IP+), ACS7**.IP+@8 (IP+), ACS7**.IP+@9 (IP+), ACS7**.IP+@10 (IP+), ACS7**.IP+@11 (IP+), ACS7**.IP+@12 (IP+), ACS7**.IP+@13 (IP+), ACS7**.IP+@14 (IP+), ACS7**.IP+@15 (IP+), ACS7**.IP+@16 (IP+), ACS7**.IP+@17 (IP+), R1.2, U$1.P$1, U$1.P$2
MISO: JP2.4
MOSI: JP2.5
unnamed: C5.1, IC1.3 (IN+), R4.2, R7.2
unnamed: R1.1, R2.2
unnamed: ACS7**.1 (VCC), C10.1, VCC_SEL.2
unnamed: LED.2, R8.1
unnamed: C4.1, IC1.2 (IN-), R5.2, R6.1
unnamed: C11.1, IC1.5 (IN+), R9.2
unnamed: L1.1, U$7.P$3 (IN+)
unnamed: L2.2, U$7.P$8 (OUT+)
unnamed: ACS7**.3 (VOUT), R9.1
SCK: JP2.6
SCL: JP4.11
SDA: JP4.12
SIGNAL_IN: C1.1, C2.1, R2.1, R3.2, U1.2 (VIN+)
SIGNAL_OUT+: R4.1, U1.7 (VOUT+)
SIGNAL_OUT-: R5.1, U1.6 (VOUT-)
VBAT: JP4.1

Notes on the sheet:
MOUNT HOLES

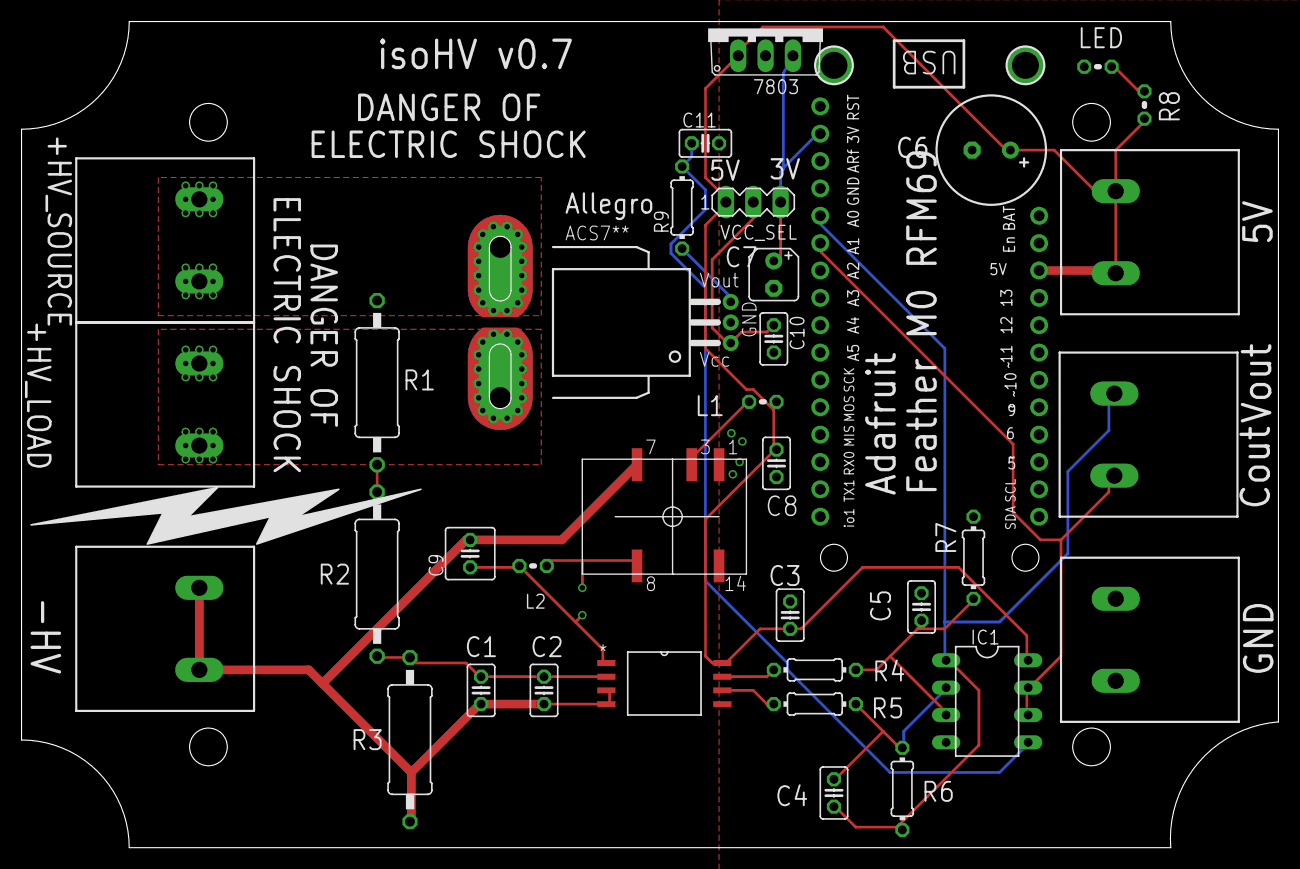
[picture p105: board isoHV v0.7.brd from above]

Board: 2 copper layers, 116.7 x 76.7 mm, 39 parts (0 on the bottom side), 21 nets.
