danbates2/emonDC/hardware/emonDCduo/emonDCduo-ESP v3.3.brd

## EAGLE design hardware/emonDCduo/emonDCduo-ESP v3.3.brd (2018-12-06)

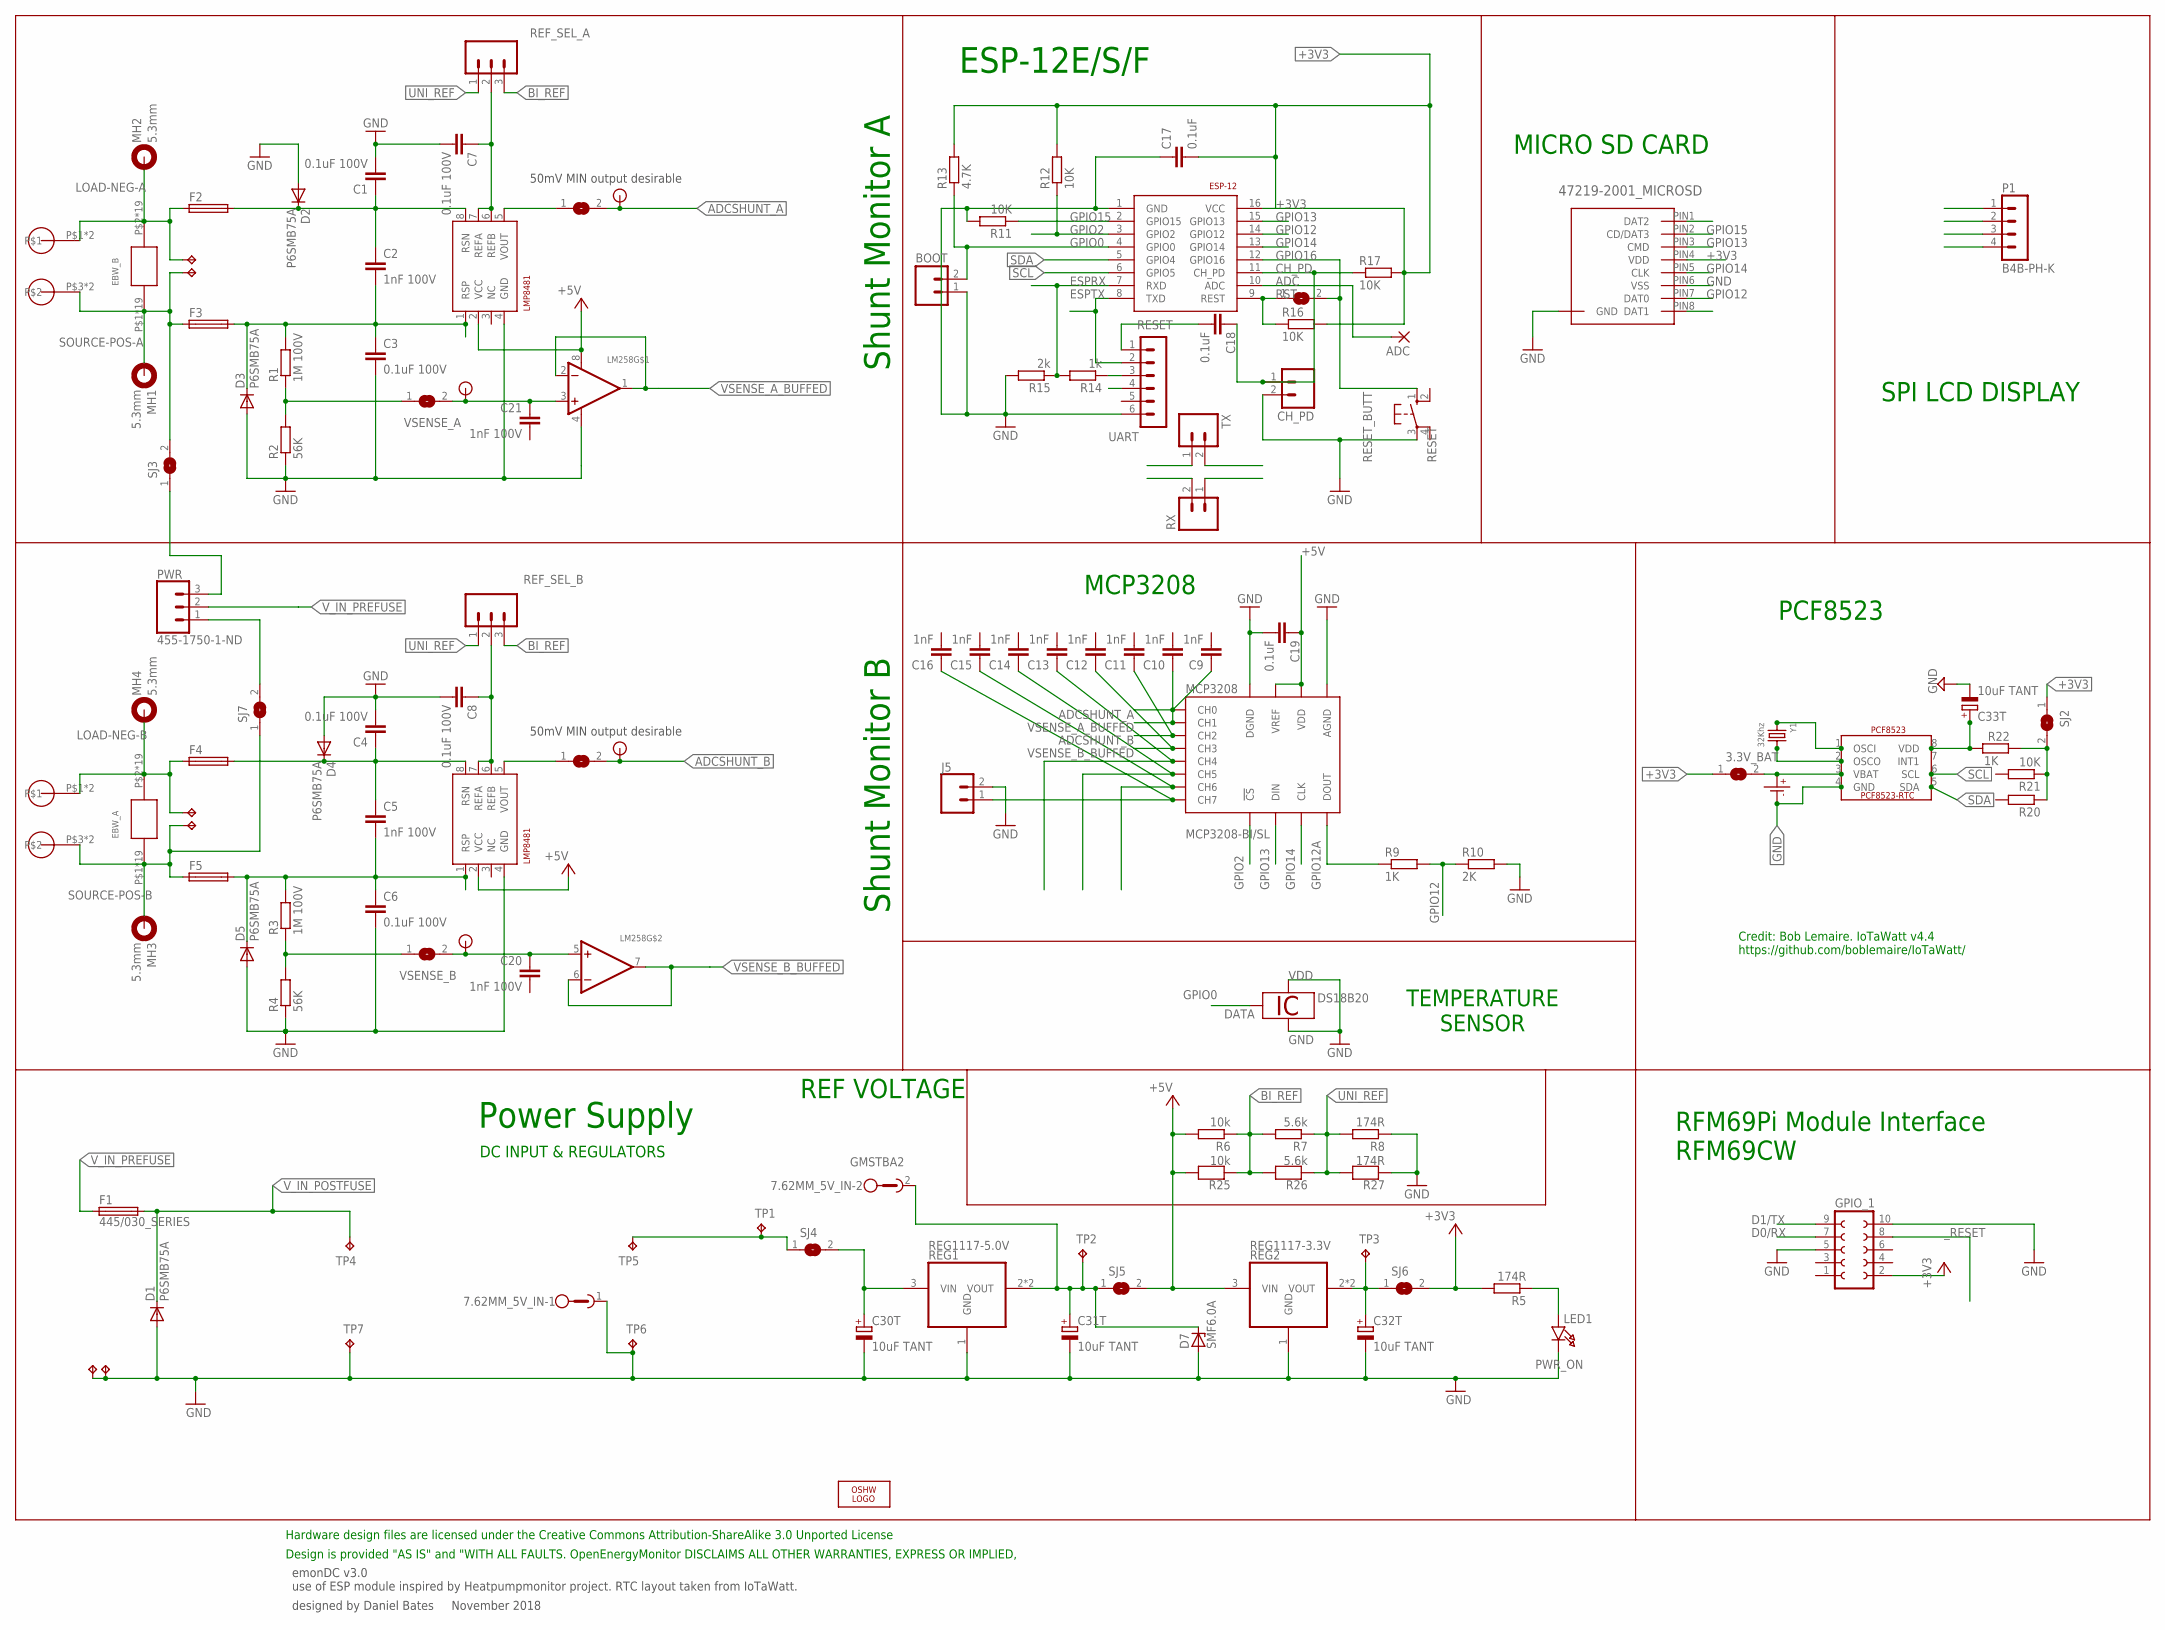
[picture p106: schematic emonDCduo-ESP v3.3.sch]

Parts:
3.3V_BAT: SOLDERJUMPERCLOSED; SOLDERJUMPER_CLOSEDWIRE
7.62MM_5V_IN: GMSTBA2
ADC: 2,15/1,0
BOOT: M02PTH; 1X02
C1, C3, C4, C6, C7, C8: 0.1uF 100V; C0603; MPN C1608X7S2A104K080AB
C2, C5, C20, C21: 1nF 100V; C0603; MPN C1608X7S2A104K080AB
C9, C10, C11, C12, C13, C14, C15, C16: 1nF; C0603
C17, C18, C19: 0.1uF; C0603
C30T, C31T, C32T, C33T: 10uF TANT; C0603POL
CH_PD: M02PTH; 1X02
CR1220: CR1220SMD; MPN Harwin S8411-45R
D1, D2, D3, D4, D5: P6SMB75A; DO214AA
D7: SMF6.0A; SOD123F
EBW_A: EBW_SERIES_15.2MM
EBW_B: EBW_SERIES_15.2MM
ESP-12: ESP8266_ESP-12; ESP8266-ESP12
F1: 445/030_SERIES; 445/030_SERIES_LITTELFUSE
F2, F3, F4, F5: TR5
GPIO_1: FE05-2_RFM69PI_OUTLINERFM69PI; FE05-2_RFM69PI_OULTINE
IC1: DS18B20; TO92-
J5: CONN_02; 1X02
LED1: PWR_ON; CHIPLED_1206
LM258: LM358; SOIC8_150MIL
LOGO1: OSHW_LOGO_6MILX0200-NT; OSHW_6X200_NOTEXT
MCP3208: MCP3208-BI/SL; SOIC16
MH1, MH2, MH3, MH4: 5.3mm; 5,3//11-PAD
MICRO_SD: 47219-2001_MICROSD
MOUNT_10.16_A, MOUNT_10.16_B: MOLEX_39970-003; 2/10,16
P1: B4B-PH-K
PCF8523: PCF8523_RTC; SOIC_8
PWR: 455-1750-1-ND; 1X03
R1, R3: 1M 100V; 0207/2V; MPN MCWR06X1003FTL
R2, R4: 56K; 0207/2V; MPN MCWR06X5901FTL
R5: 174R; R0603
R6: 10k; 0207/10
R7: 5.6k; 0207/10
R8: 174R; 0207/10
R9: 1K; R0603; MPN MCWR06X5901FTL
R10: 2K; R0603; MPN MCWR06X5901FTL
R11, R12, R16, R17, R20, R21: 10K; R0603
R13: 4.7K; R0603
R14: 1k; R0603
R15: 2k; R0603
R22: 1K; R0603
R25: 10k; 0603
R26: 5.6k; 0603
R27: 174R; 0603
REF_SEL_A: 455-1750-1-ND; 1X03; MPN 2212S-02SG-85
REF_SEL_B: 455-1750-1-ND; 1X03; MPN 2212S-02SG-85
REG1: REG1117-5.0V; SOT223; MPN REG1117-5.0
REG2: REG1117-3.3V; SOT223; MPN REG1117-3.3
RESET: RESET_BUTT; B3F-10XX
RX: M02PTH; 1X02
SHUNTMON-A: LMP8481; S-PDSO-G08; MPN LMP8481MME-S/NOPB
SHUNTMON-B: LMP8481; S-PDSO-G08; MPN LMP8481MME-H/NOPB
SJ1, SJ2, SJ4, SJ5, SJ6, SJ8, SJ9, SJ10, SJ11: SOLDERJUMPERCLOSED; SOLDERJUMPER_CLOSEDWIRE
SJ3, SJ7: SJ
TP1, TP2, TP3: TPPAD1-13; P1-13
TP4, TP5, TP6, TP7, TP8, TP9, TP10, TP11, TP12, TP13: TPPAD1-13Y; P1-13Y
TX: M02PTH; 1X02
U$1, U$4, U$5, U$6: TP1.0MM; TP1.0
UART: UART; MA06-1
Y1: 32Khz; CRYSTAL_8X3.8

Connections:
3.3V_PRE: C32T.1 (+), REG2.2 (VOUT), REG2.4 (VOUT), SJ6.1, TP3.TP
5V_PRE: 7.62MM_5V_IN.2, C31T.1 (+), D7.C, REG1.2 (VOUT), REG1.4 (VOUT), SJ5.1, TP2.TP
6.5V: C30T.1 (+), REG1.3 (VIN), SJ4.2
+3V3: 3.3V_BAT.1, C15.1, C17.2, ESP-12.16 (VCC), GPIO_1.2, MCP3208.7 (CH6), MICRO_SD.PIN4 (VDD), P1.3, R5.2, R12.2, R13.2, R16.2, R17.2, SJ2.1, SJ6.2
+5V: C19.1, LM258.8 (V+), MCP3208.15 (VREF), MCP3208.16 (VDD), R6.2, R25.2, REG2.3 (VIN), SHUNTMON-A.2 (VCC), SHUNTMON-B.2 (VCC), SJ5.2, UART.4
ADC: ADC.1, ESP-12.10 (ADC)
ADCSHUNT_A: C9.1, MCP3208.1 (CH0), SJ11.2, U$6.P$1
ADCSHUNT_B: C11.1, MCP3208.3 (CH2), SJ10.2, U$5.P$1
BI_REF: C13.1, MCP3208.5 (CH4), R6.1, R7.2, R25.1, R26.2, REF_SEL_A.3, REF_SEL_B.3
CH7: C16.1, J5.1, MCP3208.8 (CH7)
CH_PD: C18.1, CH_PD.1, ESP-12.11 (CH_PD), R17.1
D0/RX: GPIO_1.7, TX.2
D1/TX: GPIO_1.9, RX.1
ESPRX: ESP-12.7 (RXD), R14.2, R15.1, RX.2
ESPTX: ESP-12.8 (TXD), TX.1, UART.2
GND: 7.62MM_5V_IN.1, BOOT.1, C1.2, C3.2, C4.2, C6.2, C7.2, C8.2, C17.1, C19.2, C30T.2 (-), C31T.2 (-), C32T.2 (-), C33T.2 (-), CH_PD.2, CR1220.P- (P$-), D1.A, D2.A, D3.A, D4.A, D5.A, D7.A, ESP-12.1 (GND), GPIO_1.5, GPIO_1.10, IC1.1 (GND), IC1.3 (VDD), J5.2, LED1.C, LM258.4 (V-), MCP3208.9 (DGND), MCP3208.14 (AGND), MICRO_SD.P$1 (GND), MICRO_SD.P$2 (GND), MICRO_SD.P$3 (GND), MICRO_SD.P$4 (GND), MICRO_SD.PIN6 (VSS), P1.4, PCF8523.4 (GND), R2.1, R4.1, R8.1, R10.2, R11.2, R15.2, R27.1, REG1.1 (GND), REG2.1 (GND), RESET.3, SHUNTMON-A.4 (GND), SHUNTMON-B.4 (GND), TP6.TP, TP7.TP, TP12.TP, TP13.TP, UART.6
GPIO0: BOOT.2, ESP-12.4 (GPIO0), IC1.2 (DATA), R13.1
GPIO2: ESP-12.3 (GPIO2), MCP3208.10 (!CS), R12.1
GPIO12: ESP-12.14 (GPIO12), MICRO_SD.PIN7 (DAT0), R9.2, R10.1
GPIO12A: MCP3208.12 (DOUT), R9.1
GPIO13: ESP-12.15 (GPIO13), MCP3208.11 (DIN), MICRO_SD.PIN3 (CMD)
GPIO14: ESP-12.13 (GPIO14), MCP3208.13 (CLK), MICRO_SD.PIN5 (CLK)
GPIO15: ESP-12.2 (GPIO15), MICRO_SD.PIN2 (CD/DAT3), R11.1
GPIO16: ESP-12.12 (GPIO16), RESET.1 (S), SJ1.2
LOAD-NEG-A: EBW_B.P$2, EBW_B.P$18, EBW_B.P$19, EBW_B.P$20, EBW_B.P$21, EBW_B.P$22, EBW_B.P$23, EBW_B.P$24, EBW_B.P$25, EBW_B.P$26, EBW_B.P$27, EBW_B.P$28, EBW_B.P$29, EBW_B.P$30, EBW_B.P$31, EBW_B.P$32, EBW_B.P$36, EBW_B.P$37, EBW_B.P$38, F2.1, MH2.B5,5, MOUNT_10.16_A.P$1, MOUNT_10.16_A.P$2, TP11.TP
LOAD-NEG-A_T: C1.1, C2.1, D2.C, F2.2, SHUNTMON-A.8 (RSN)
LOAD-NEG-B: EBW_A.P$2, EBW_A.P$18, EBW_A.P$19, EBW_A.P$20, EBW_A.P$21, EBW_A.P$22, EBW_A.P$23, EBW_A.P$24, EBW_A.P$25, EBW_A.P$26, EBW_A.P$27, EBW_A.P$28, EBW_A.P$29, EBW_A.P$30, EBW_A.P$31, EBW_A.P$32, EBW_A.P$36, EBW_A.P$37, EBW_A.P$38, F4.1, MH4.B5,5, MOUNT_10.16_B.P$1, MOUNT_10.16_B.P$2, TP9.TP
LOAD-NEG-B_T: C4.1, C5.1, D4.C, F4.2, SHUNTMON-B.8 (RSN)
unnamed: SJ4.1, TP1.TP, TP5.TP
unnamed: PWR.3, SJ3.1
unnamed: PWR.1, SJ7.2
unnamed: LED1.A, R5.1
unnamed: SHUNTMON-B.5 (VOUT), SJ10.1
unnamed: SHUNTMON-A.5 (VOUT), SJ11.1
unnamed: R14.1, UART.3
unnamed: PCF8523.2 (OSCO), Y1.P$4 (2)
unnamed: PCF8523.1 (OSCI), Y1.P$1 (1)
REF_A_INPUT: C7.1, REF_SEL_A.2, SHUNTMON-A.6 (REFB), SHUNTMON-A.7 (REFA)
REF_B_INPUT: C8.1, REF_SEL_B.2, SHUNTMON-B.6 (REFB), SHUNTMON-B.7 (REFA)
RESET: C18.2, UART.1
RST: ESP-12.9 (REST), R16.1, SJ1.1
SCL: ESP-12.6 (GPIO5), P1.2, PCF8523.6 (SCL)
SDA: ESP-12.5 (GPIO4), P1.1, PCF8523.5 (SDA)
SOURCE-POS-A: EBW_B.P$1, EBW_B.P$3, EBW_B.P$4, EBW_B.P$5, EBW_B.P$6, EBW_B.P$7, EBW_B.P$8, EBW_B.P$9, EBW_B.P$10, EBW_B.P$11, EBW_B.P$12, EBW_B.P$13, EBW_B.P$14, EBW_B.P$15, EBW_B.P$16, EBW_B.P$17, EBW_B.P$33, EBW_B.P$34, EBW_B.P$35, F3.1, MH1.B5,5, MOUNT_10.16_A.P$3, MOUNT_10.16_A.P$4, SJ3.2, TP10.TP
SOURCE-POS-A_T: C2.2, C3.1, D3.C, F3.2, R1.2, SHUNTMON-A.1 (RSP)
SOURCE-POS-B: EBW_A.P$1, EBW_A.P$3, EBW_A.P$4, EBW_A.P$5, EBW_A.P$6, EBW_A.P$7, EBW_A.P$8, EBW_A.P$9, EBW_A.P$10, EBW_A.P$11, EBW_A.P$12, EBW_A.P$13, EBW_A.P$14, EBW_A.P$15, EBW_A.P$16, EBW_A.P$17, EBW_A.P$33, EBW_A.P$34, EBW_A.P$35, F5.1, MH3.B5,5, MOUNT_10.16_B.P$3, MOUNT_10.16_B.P$4, SJ7.1, TP8.TP
SOURCE-POS-B_T: C5.2, C6.1, D5.C, F5.2, R3.2, SHUNTMON-B.1 (RSP)
UNI_REF: C14.1, MCP3208.6 (CH5), R7.1, R8.2, R26.1, R27.2, REF_SEL_A.1, REF_SEL_B.1
VBAT: 3.3V_BAT.2, CR1220.P+ (P$+), PCF8523.3 (VBAT)
VDD_PCF: C33T.1 (+), PCF8523.8 (VDD), R22.1
VDD_RTC_POSTJUMPER: R20.1, R21.1, R22.2, SJ2.2
VSENSE_A: R1.1, R2.2, SJ8.1
VSENSE_A_BUFFED: C10.1, LM258.1 (OUT), LM258.2 (-IN), MCP3208.2 (CH1)
VSENSE_A_TP: C21.1, LM258.3 (+IN), SJ8.2, U$1.P$1
VSENSE_B: R3.1, R4.2, SJ9.1
VSENSE_B_BUFFED: C12.1, LM258.6 (-IN), LM258.7 (OUT), MCP3208.4 (CH3)
VSENSE_B_TP: C20.1, LM258.5 (+IN), SJ9.2, U$4.P$1
V_IN_POSTFUSE: D1.C, F1.P$3 (2), F1.P$4 (2), TP4.TP
V_IN_PREFUSE: F1.P$1 (1), F1.P$2 (1), PWR.2
_RESET: GPIO_1.8

Notes on the sheet:
emonDC v3.0 use of ESP module inspired by Heatpumpmonitor project. RTC layout taken from IoTaWatt.
designed by Daniel Bates November 2018
Power Supply
Design is provided "AS IS" and "WITH ALL FAULTS. OpenEnergyMonitor DISCLAIMS ALL OTHER WARRANTIES, EXPRESS OR IMPLIED,
Hardware design files are licensed under the Creative Commons Attribution-ShareAlike 3.0 Unported License
DC INPUT & REGULATORS
Shunt Monitor B
Shunt Monitor A
ESP-12E/S/F
MICRO SD CARD
RFM69Pi Module Interface RFM69CW
MCP3208
PCF8523
Credit: Bob Lemaire. IoTaWatt v4.4 https://github.com/boblemaire/IoTaWatt/
SPI LCD DISPLAY
TEMPERATURE SENSOR
50mV MIN output desirable
REF VOLTAGE

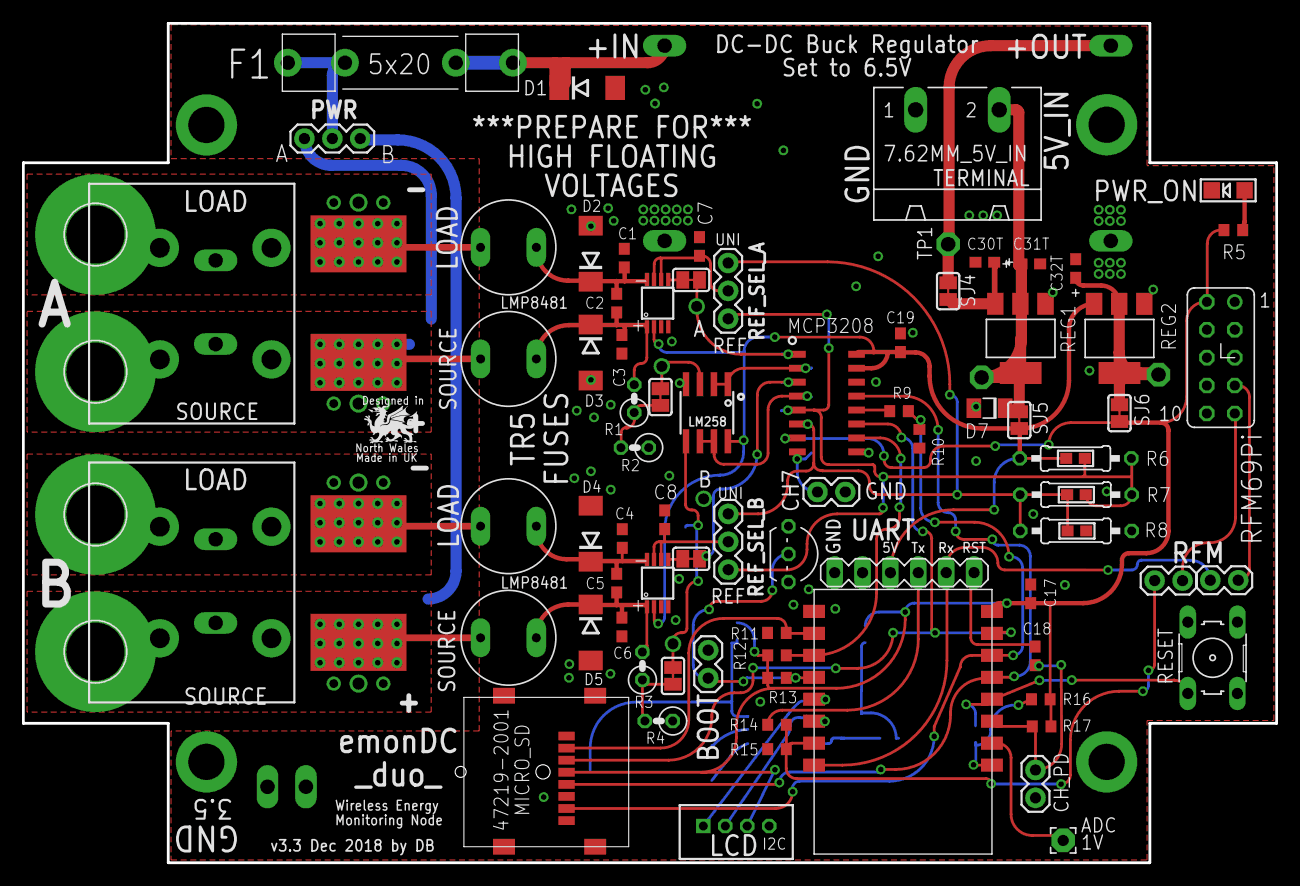
[picture p107: board emonDCduo-ESP v3.3.brd from above]

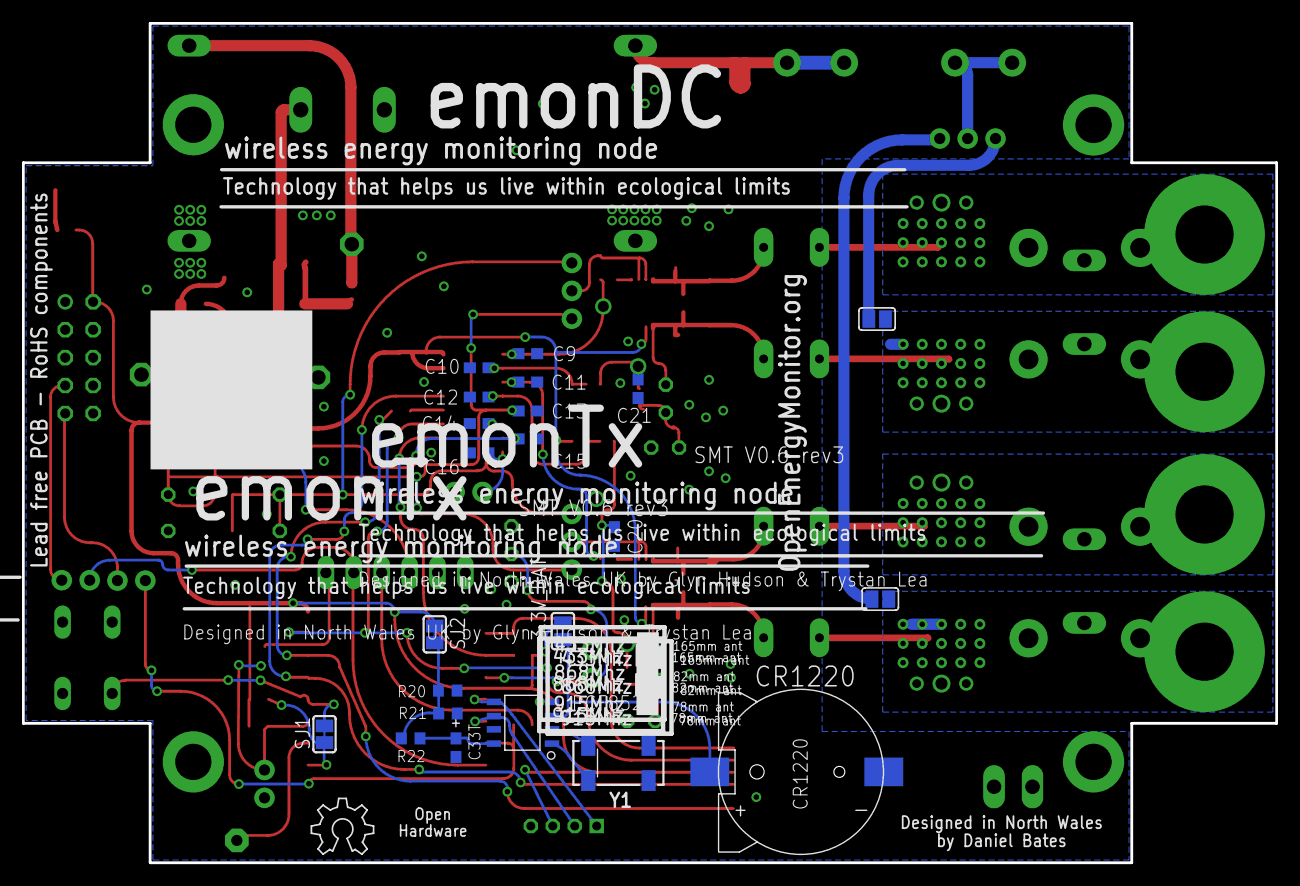
[picture p108: board emonDCduo-ESP v3.3.brd from below]

Board: 2 copper layers, 114.2 x 76.5 mm, 126 parts (23 on the bottom side), 59 nets.

Other parts of the board:
U$2, U$3: ALIGNMENT_STOP
