danbates2/emonDC/hardware/emonDCduo/emonDCduo-ESP v2.0 eagle.v7.brd

## EAGLE design hardware/emonDCduo/emonDCduo-ESP v2.0 eagle.v7.brd (2018-08-01)

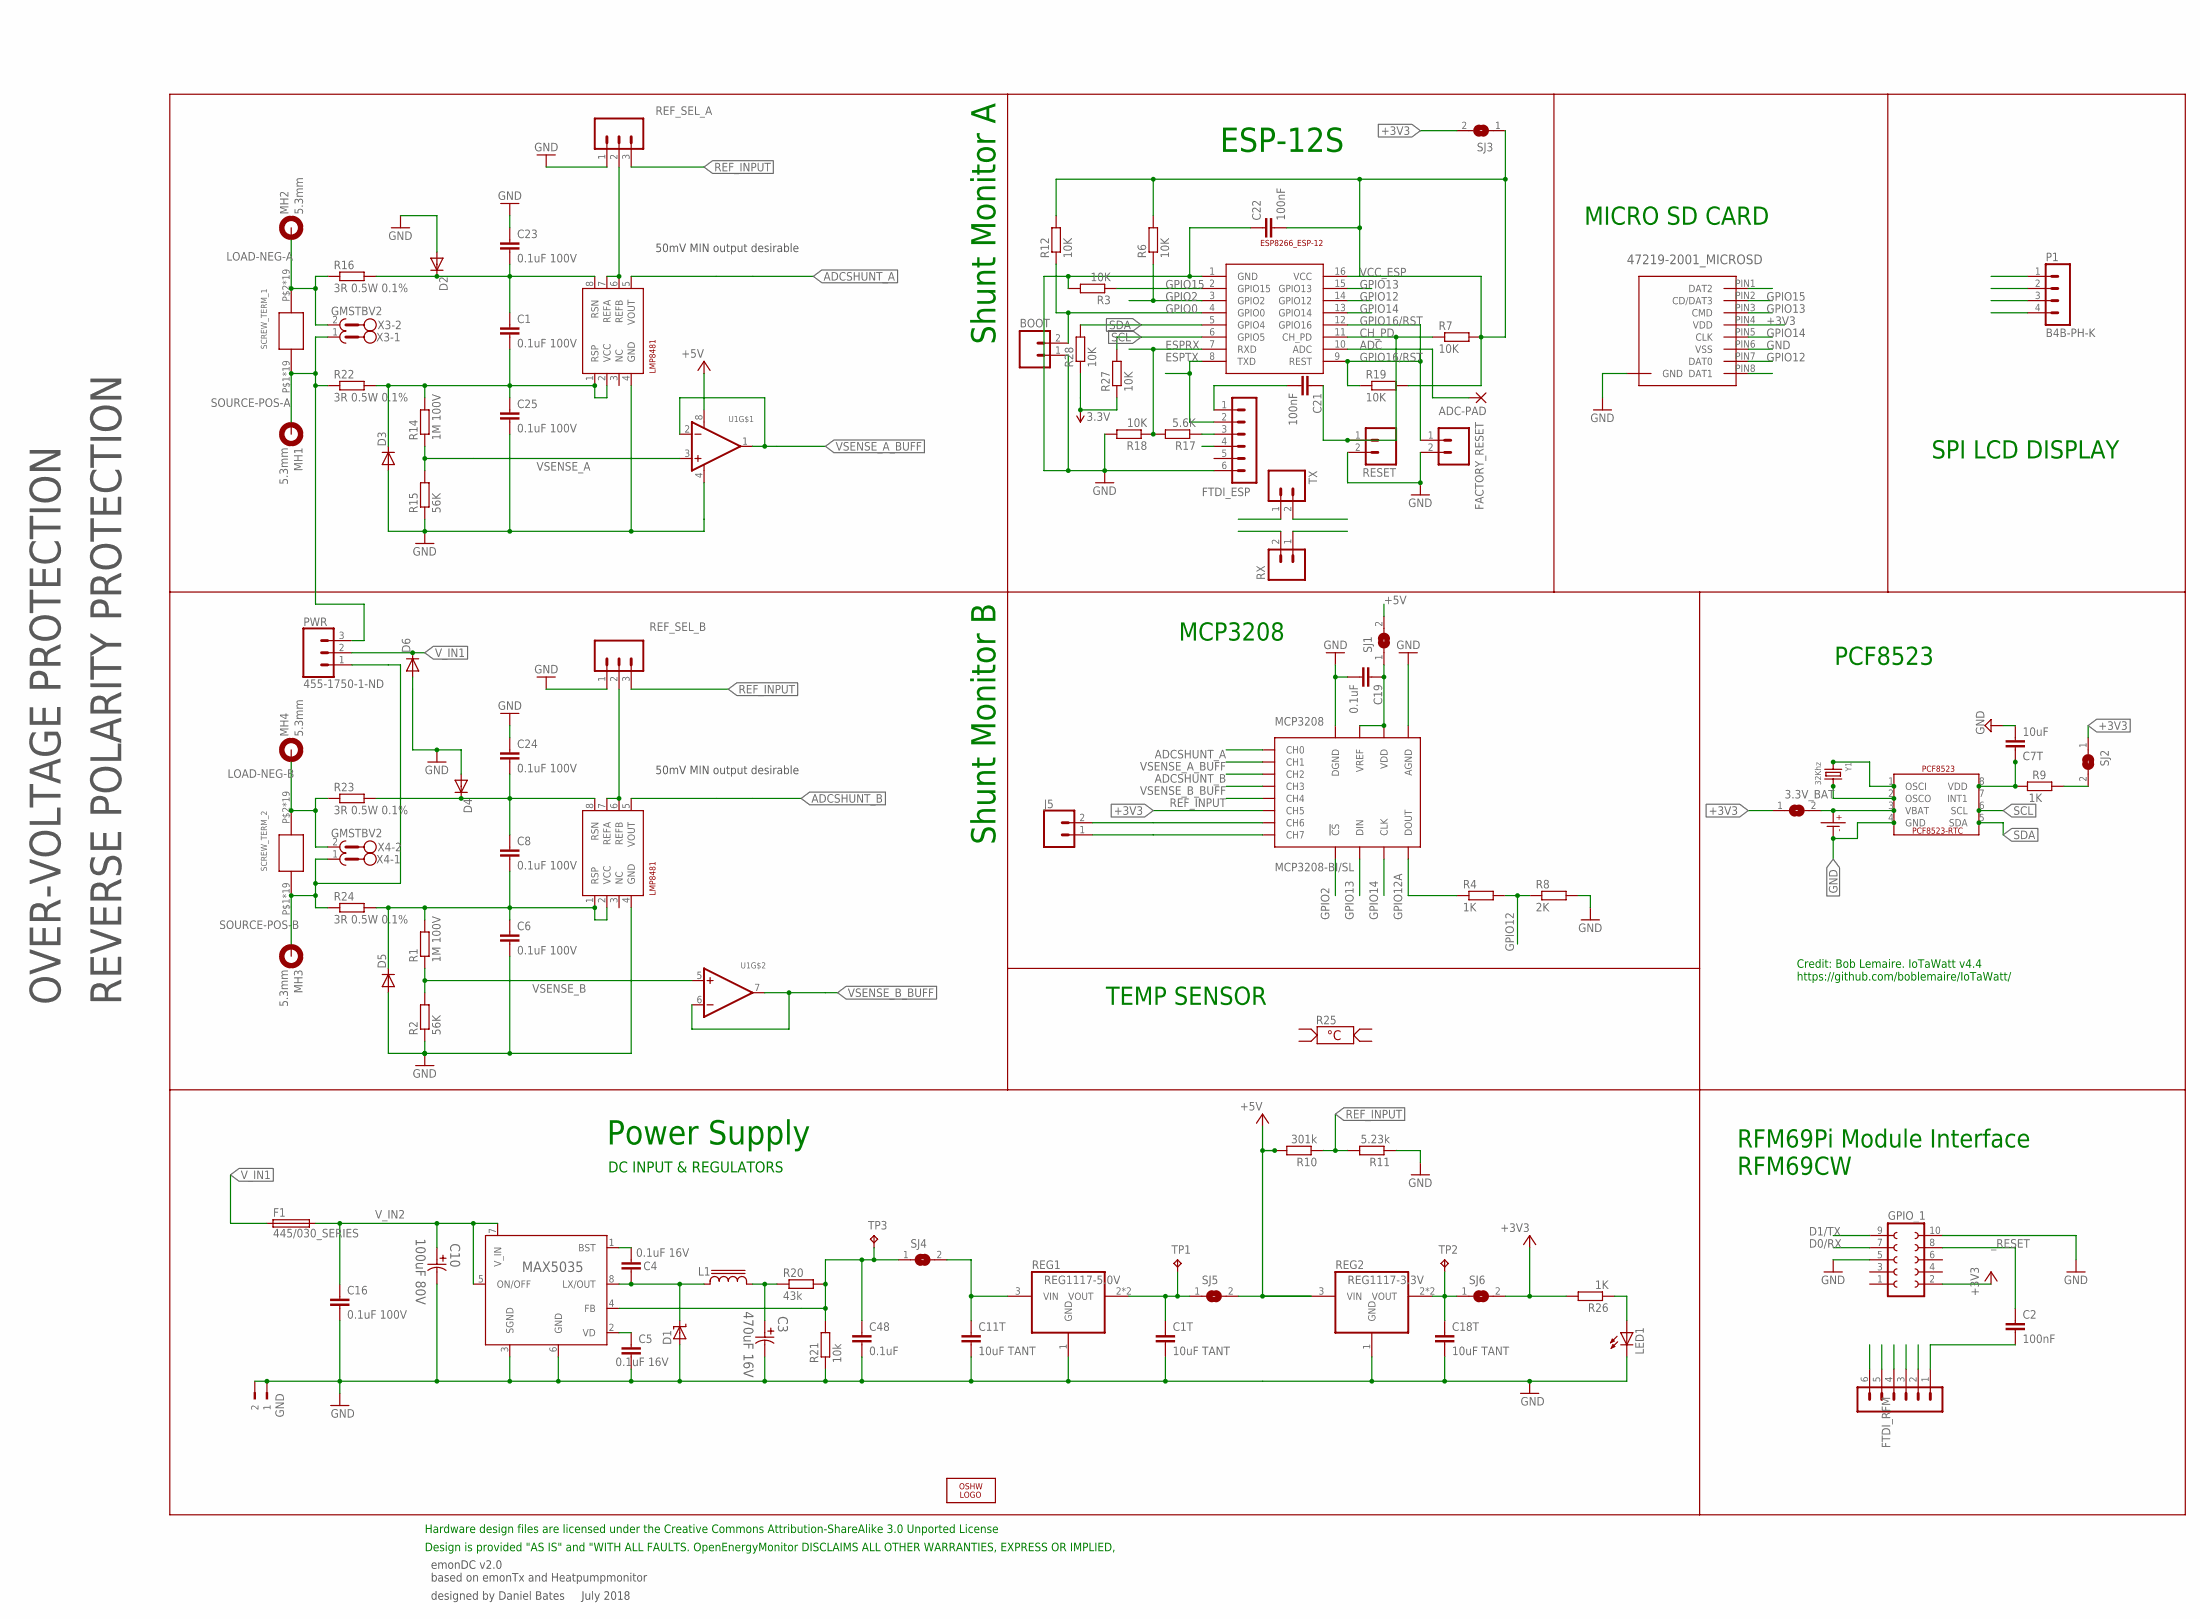
[picture p109: schematic emonDCduo-ESP v2.0 eagle.v7.sch]

Parts:
3.3V_BAT: SJ-CONCON; SJ-CON
ADC-PAD: 2,15/1,0
BOOT: M02PTH; 1X02
C1, C6, C8, C23, C24, C25: 0.1uF 100V; C0603; MPN C1608X7S2A104K080AB
C1T, C11T, C18T: 10uF TANT; C0603
C2, C21, C22: 100nF; C0603
C3: 470uF 16V; CAPAE830X1050N
C4, C5: 0.1uF 16V; C0603
C7T: 10uF; C0603
C10: 100uF 80V; CAPAE1350X1400N
C16: 0.1uF 100V; C0603
C19, C48: 0.1uF; C0603
CR1220: CR1220SMD; MPN Harwin S8411-45R
D1: MBRS1100T3G; SMB_1; MPN MBRS1100T3G
D2, D3, D4, D5, D6: DIODE-DO214AA; DO214AA
ESP-12: ESP8266_ESP-12; ESP8266-ESP12
F1: 445/030_SERIES; 445/030_SERIES_LITTELFUSE
FACTORY_RESET: FACTORY_RESET; 1X02
FTDI_ESP: FTDI_ESP; MA06-1
FTDI_RFM: FTDI_RFM; MA06-1
GND: 180-2
GPIO_1: FE05-2_RFM69PI_OUTLINERFM69PI; FE05-2_RFM69PI_OULTINE
J5: CONN_02; 1X02
L1: SRR1208; SSR1208; MPN SRR1208-151YL
LED1: LEDCHIP-LED0805; CHIP-LED0805
LOGO1: OSHW_LOGO_6MILX0200-NT; OSHW_6X200_NOTEXT
MCP3208: MCP3208-BI/SL; SOIC16
MH1, MH2, MH3, MH4: 5.3mm; 5,3//11-PAD
MICRO_SD: 47219-2001_MICROSD
P1: B4B-PH-K
PCF8523: PCF8523_RTC; SOIC_8
PWR: 455-1750-1-ND; 1X03
R1, R14: 1M 100V; R0603; MPN MCWR06X1003FTL
R2, R15: 56K; R0603; MPN MCWR06X5901FTL
R3, R6, R7, R12, R18, R19, R27, R28: 10K; R0603
R4: 1K; R0603; MPN MCWR06X5901FTL
R8: 2K; R0603; MPN MCWR06X5901FTL
R9, R26: 1K; R0603
R10: 301k; 0204/7
R11: 5.23k; 0204/7
R16, R22, R23, R24: 3R 0.5W 0.1%; R0805
R17: 5.6K; R0603
R20: 43k; R0603
R21: 10k; R0603
R25: 3220824X; PT1206
REF_SEL_A: 455-1750-1-ND; 1X03; MPN 2212S-02SG-85
REF_SEL_B: 455-1750-1-ND; 1X03; MPN 2212S-02SG-85
REG0: MAX5035; 21-0111D_SBE-14; MPN MAX5035EASA+
REG1: REG1117-5.0V; SOT223; MPN REG1117-5.0
REG2: REG1117-3.3V; SOT223; MPN REG1117-3.3
RESET: M02PTH; 1X02
RX: M02PTH; 1X02
SCREW_TERM_1, SCREW_TERM_2: EBW_SERIES_15.2MM
SHUNTMON-A: LMP8481; S-PDSO-G08; MPN LMP8481MME-S/NOPB
SHUNTMON-B: LMP8481; S-PDSO-G08; MPN LMP8481MME-H/NOPB
SJ1, SJ2, SJ3, SJ4, SJ5, SJ6: SJ-CONCON; SJ-CON
TP1, TP2, TP3: TPPAD1-13; P1-13
TX: M02PTH; 1X02
U1: LM358; SOIC8_150MIL
X3, X4: GMSTBV2
Y1: 32Khz; CRYSTAL_8X3.8

Connections:
3.3V_PRE: C18T.1, REG2.2 (VOUT), REG2.4 (VOUT), SJ6.1, TP2.TP
5V_PRE: C1T.1, REG1.2 (VOUT), REG1.4 (VOUT), SJ5.1, TP1.TP
6.5V: C11T.1, REG1.3 (VIN), SJ4.2
+3V3: 3.3V_BAT.1, GPIO_1.2, MCP3208.6 (CH5), MICRO_SD.PIN4 (VDD), P1.3, R26.2, R27.1, R28.1, SJ2.1, SJ3.2, SJ6.2
+5V: FTDI_ESP.4, FTDI_RFM.4, R10.2, REG2.3 (VIN), SJ1.2, SJ5.2, U1.8 (V+)
ADC: ADC-PAD.1, ESP-12.10 (ADC)
ADCSHUNT_A: MCP3208.1 (CH0), SHUNTMON-A.5 (VOUT)
ADCSHUNT_B: MCP3208.3 (CH2), SHUNTMON-B.5 (VOUT)
BST: C4.1, REG0.1 (BST)
CH6: J5.2, MCP3208.7 (CH6)
CH7: J5.1, MCP3208.8 (CH7)
CH_PD: C21.1, ESP-12.11 (CH_PD), R7.1, RESET.1
D0/RX: FTDI_RFM.2, GPIO_1.7, TX.2
D1/TX: FTDI_RFM.3, GPIO_1.9, RX.1
ESPRX: ESP-12.7 (RXD), R17.2, R18.1, RX.2
ESPTX: ESP-12.8 (TXD), FTDI_ESP.2, TX.1
GND: BOOT.1, C1T.2, C3.2, C5.2, C6.2, C7T.2, C10.2, C11T.2, C16.2, C18T.2, C19.2, C22.1, C23.1, C24.1, C25.2, C48.2, CR1220.P- (P$-), D1.A, D2.A, D3.A, D4.A, D5.A, D6.A, ESP-12.1 (GND), FACTORY_RESET.2, FTDI_ESP.6, FTDI_RFM.6, GND.1, GND.2, GPIO_1.5, GPIO_1.10, LED1.C, MCP3208.9 (DGND), MCP3208.14 (AGND), MICRO_SD.P$1 (GND), MICRO_SD.P$2 (GND), MICRO_SD.P$3 (GND), MICRO_SD.P$4 (GND), MICRO_SD.PIN6 (VSS), P1.4, PCF8523.4 (GND), R2.1, R3.2, R8.2, R11.1, R15.1, R18.2, R21.1, REF_SEL_A.1, REF_SEL_B.1, REG0.3 (SGND), REG0.6 (GND), REG1.1 (GND), REG2.1 (GND), RESET.2, SHUNTMON-A.4 (GND), SHUNTMON-B.4 (GND), U1.4 (V-)
GPIO0: BOOT.2, ESP-12.4 (GPIO0), R12.1
GPIO2: ESP-12.3 (GPIO2), MCP3208.10 (!CS), R6.1
GPIO12: ESP-12.14 (GPIO12), MICRO_SD.PIN7 (DAT0), R4.2, R8.1
GPIO12A: MCP3208.12 (DOUT), R4.1
GPIO13: ESP-12.15 (GPIO13), MCP3208.11 (DIN), MICRO_SD.PIN3 (CMD)
GPIO14: ESP-12.13 (GPIO14), MCP3208.13 (CLK), MICRO_SD.PIN5 (CLK)
GPIO15: ESP-12.2 (GPIO15), MICRO_SD.PIN2 (CD/DAT3), R3.1
GPIO16/RST: ESP-12.9 (REST), ESP-12.12 (GPIO16), FACTORY_RESET.1, R19.1
LOAD-NEG-A: MH2.B5,5, R16.1, SCREW_TERM_1.P$2, SCREW_TERM_1.P$18, SCREW_TERM_1.P$19, SCREW_TERM_1.P$20, SCREW_TERM_1.P$21, SCREW_TERM_1.P$22, SCREW_TERM_1.P$23, SCREW_TERM_1.P$24, SCREW_TERM_1.P$25, SCREW_TERM_1.P$26, SCREW_TERM_1.P$27, SCREW_TERM_1.P$28, SCREW_TERM_1.P$29, SCREW_TERM_1.P$30, SCREW_TERM_1.P$31, SCREW_TERM_1.P$32, SCREW_TERM_1.P$36, SCREW_TERM_1.P$37, SCREW_TERM_1.P$38, X3.2
LOAD-NEG-B: MH4.B5,5, R23.1, SCREW_TERM_2.P$2, SCREW_TERM_2.P$18, SCREW_TERM_2.P$19, SCREW_TERM_2.P$20, SCREW_TERM_2.P$21, SCREW_TERM_2.P$22, SCREW_TERM_2.P$23, SCREW_TERM_2.P$24, SCREW_TERM_2.P$25, SCREW_TERM_2.P$26, SCREW_TERM_2.P$27, SCREW_TERM_2.P$28, SCREW_TERM_2.P$29, SCREW_TERM_2.P$30, SCREW_TERM_2.P$31, SCREW_TERM_2.P$32, SCREW_TERM_2.P$36, SCREW_TERM_2.P$37, SCREW_TERM_2.P$38, X4.2
LX: C4.2, D1.C, L1.1, REG0.8 (LX/OUT)
MCP_VCC: C19.1, MCP3208.15 (VREF), MCP3208.16 (VDD), SJ1.1
unnamed: LED1.A, R26.1
unnamed: C7T.1, PCF8523.8 (VDD), R9.1
unnamed: C1.1, C23.2, D2.C, R16.2, SHUNTMON-A.8 (RSN)
unnamed: C8.1, C24.2, D4.C, R23.2, SHUNTMON-B.8 (RSN)
unnamed: C1.2, C25.1, D3.C, R14.2, R22.2, SHUNTMON-A.1 (RSP), SHUNTMON-A.2 (VCC)
unnamed: R9.2, SJ2.2
unnamed: C3.1, L1.2, R20.1
unnamed: C21.2, FTDI_ESP.1
unnamed: FTDI_ESP.3, R17.1
unnamed: PCF8523.2 (OSCO), Y1.P$4 (2)
unnamed: PCF8523.1 (OSCI), Y1.P$1 (1)
unnamed: C2.2, FTDI_RFM.1
PRE_6.5V: C48.1, R20.2, R21.2, REG0.4 (FB), SJ4.1, TP3.TP
REF_A_INPUT: REF_SEL_A.2, SHUNTMON-A.6 (REFB), SHUNTMON-A.7 (REFA)
REF_B_INPUT: REF_SEL_B.2, SHUNTMON-B.6 (REFB), SHUNTMON-B.7 (REFA)
REF_INPUT: MCP3208.5 (CH4), R10.1, R11.2, REF_SEL_A.3, REF_SEL_B.3
SCL: ESP-12.6 (GPIO5), P1.2, PCF8523.6 (SCL), R27.2
SDA: ESP-12.5 (GPIO4), P1.1, PCF8523.5 (SDA), R28.2
SOURCE-POS-A: MH1.B5,5, PWR.3, R22.1, SCREW_TERM_1.P$1, SCREW_TERM_1.P$3, SCREW_TERM_1.P$4, SCREW_TERM_1.P$5, SCREW_TERM_1.P$6, SCREW_TERM_1.P$7, SCREW_TERM_1.P$8, SCREW_TERM_1.P$9, SCREW_TERM_1.P$10, SCREW_TERM_1.P$11, SCREW_TERM_1.P$12, SCREW_TERM_1.P$13, SCREW_TERM_1.P$14, SCREW_TERM_1.P$15, SCREW_TERM_1.P$16, SCREW_TERM_1.P$17, SCREW_TERM_1.P$33, SCREW_TERM_1.P$34, SCREW_TERM_1.P$35, X3.1
SOURCE-POS-B: MH3.B5,5, PWR.1, R24.1, SCREW_TERM_2.P$1, SCREW_TERM_2.P$3, SCREW_TERM_2.P$4, SCREW_TERM_2.P$5, SCREW_TERM_2.P$6, SCREW_TERM_2.P$7, SCREW_TERM_2.P$8, SCREW_TERM_2.P$9, SCREW_TERM_2.P$10, SCREW_TERM_2.P$11, SCREW_TERM_2.P$12, SCREW_TERM_2.P$13, SCREW_TERM_2.P$14, SCREW_TERM_2.P$15, SCREW_TERM_2.P$16, SCREW_TERM_2.P$17, SCREW_TERM_2.P$33, SCREW_TERM_2.P$34, SCREW_TERM_2.P$35, X4.1
SOURCE-POS-B_T: C6.1, C8.2, D5.C, R1.2, R24.2, SHUNTMON-B.1 (RSP), SHUNTMON-B.2 (VCC)
VBAT: 3.3V_BAT.2, CR1220.P+ (P$+), PCF8523.3 (VBAT)
VCC_ESP: C22.2, ESP-12.16 (VCC), R6.2, R7.2, R12.2, R19.2, SJ3.1
VD: C5.1, REG0.2 (VD)
VSENSE_A: R14.1, R15.2, U1.3 (+IN)
VSENSE_A_BUFF: MCP3208.2 (CH1), U1.1 (OUT), U1.2 (-IN)
VSENSE_B: R1.1, R2.2, U1.5 (+IN)
VSENSE_B_BUFF: MCP3208.4 (CH3), U1.6 (-IN), U1.7 (OUT)
V_IN1: D6.C, F1.P$1 (1), F1.P$2 (1), PWR.2
V_IN2: C10.1, C16.1, F1.P$3 (2), F1.P$4 (2), REG0.5 (ON/OFF), REG0.7 (V_IN)
_RESET: C2.1, GPIO_1.8

Notes on the sheet:
emonDC v2.0 based on emonTx and Heatpumpmonitor
designed by Daniel Bates July 2018
Power Supply
Design is provided "AS IS" and "WITH ALL FAULTS. OpenEnergyMonitor DISCLAIMS ALL OTHER WARRANTIES, EXPRESS OR IMPLIED,
Hardware design files are licensed under the Creative Commons Attribution-ShareAlike 3.0 Unported License
DC INPUT & REGULATORS
Shunt Monitor B
Shunt Monitor A
ESP-12S
MICRO SD CARD
RFM69Pi Module Interface RFM69CW
MCP3208
PCF8523
Credit: Bob Lemaire. IoTaWatt v4.4 https://github.com/boblemaire/IoTaWatt/
SPI LCD DISPLAY
TEMP SENSOR
50mV MIN output desirable
REVERSE POLARITY PROTECTION
OVER-VOLTAGE PROTECTION

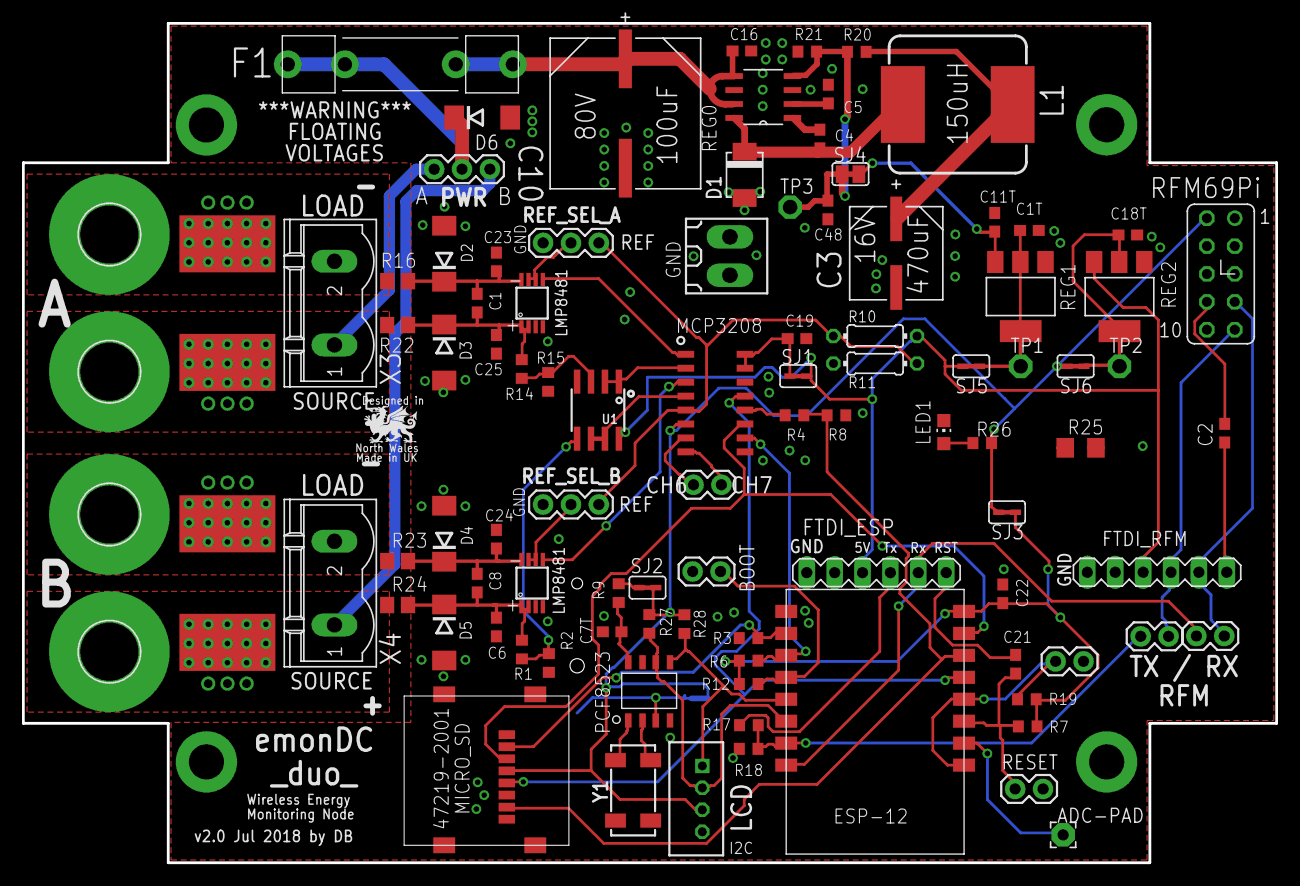
[picture p110: board emonDCduo-ESP v2.0 eagle.v7.brd from above]

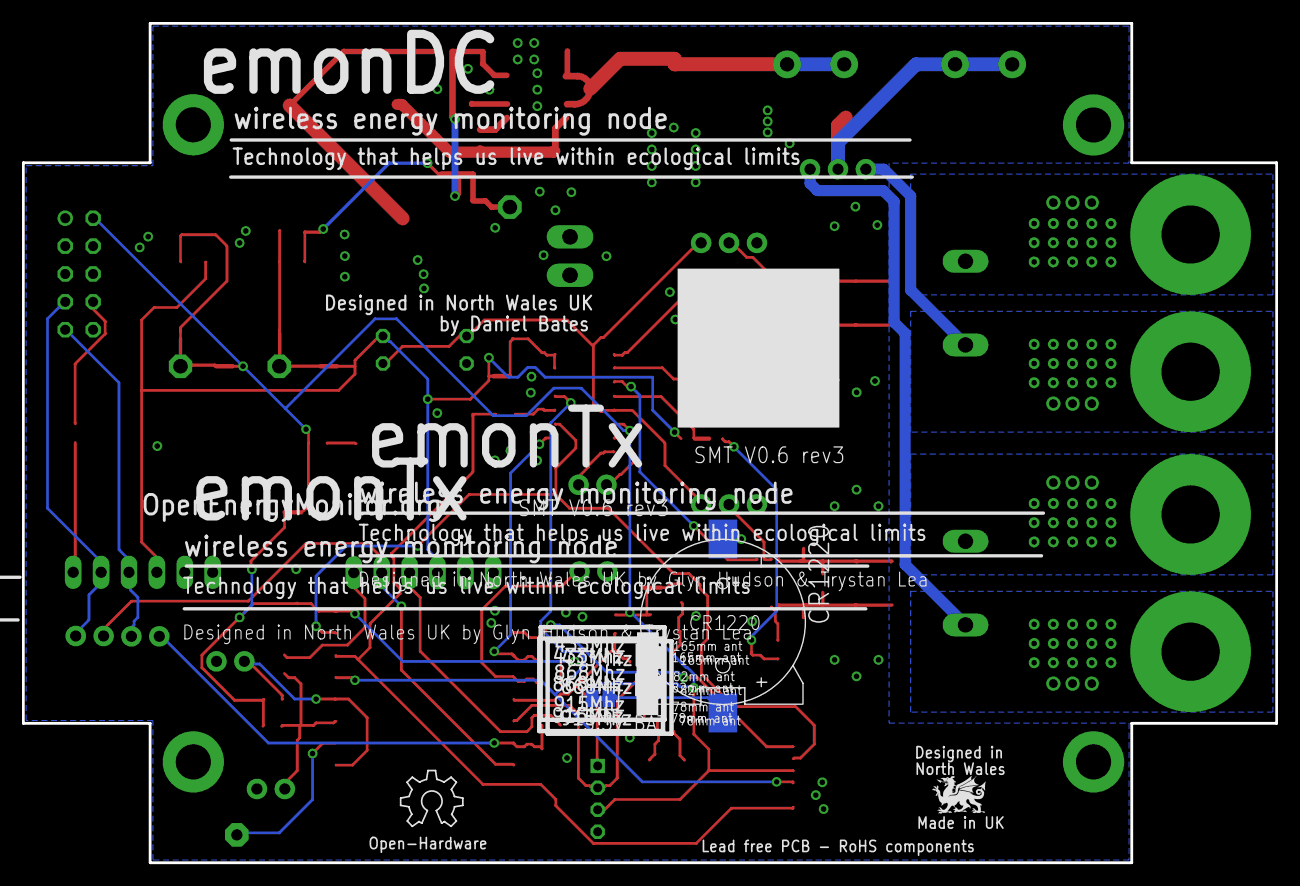
[picture p111: board emonDCduo-ESP v2.0 eagle.v7.brd from below]

Board: 2 copper layers, 114.2 x 76.5 mm, 102 parts (4 on the bottom side), 60 nets.

Other parts of the board:
U$1: DRAGON_LOGO_NOTEXT
