danbates2/emonDC/hardware/emonDCduo/eagle7files/emonDCduo-ESP v1.4.brd

## EAGLE design hardware/emonDCduo/eagle7files/emonDCduo-ESP v1.4.brd (2018-03-27)

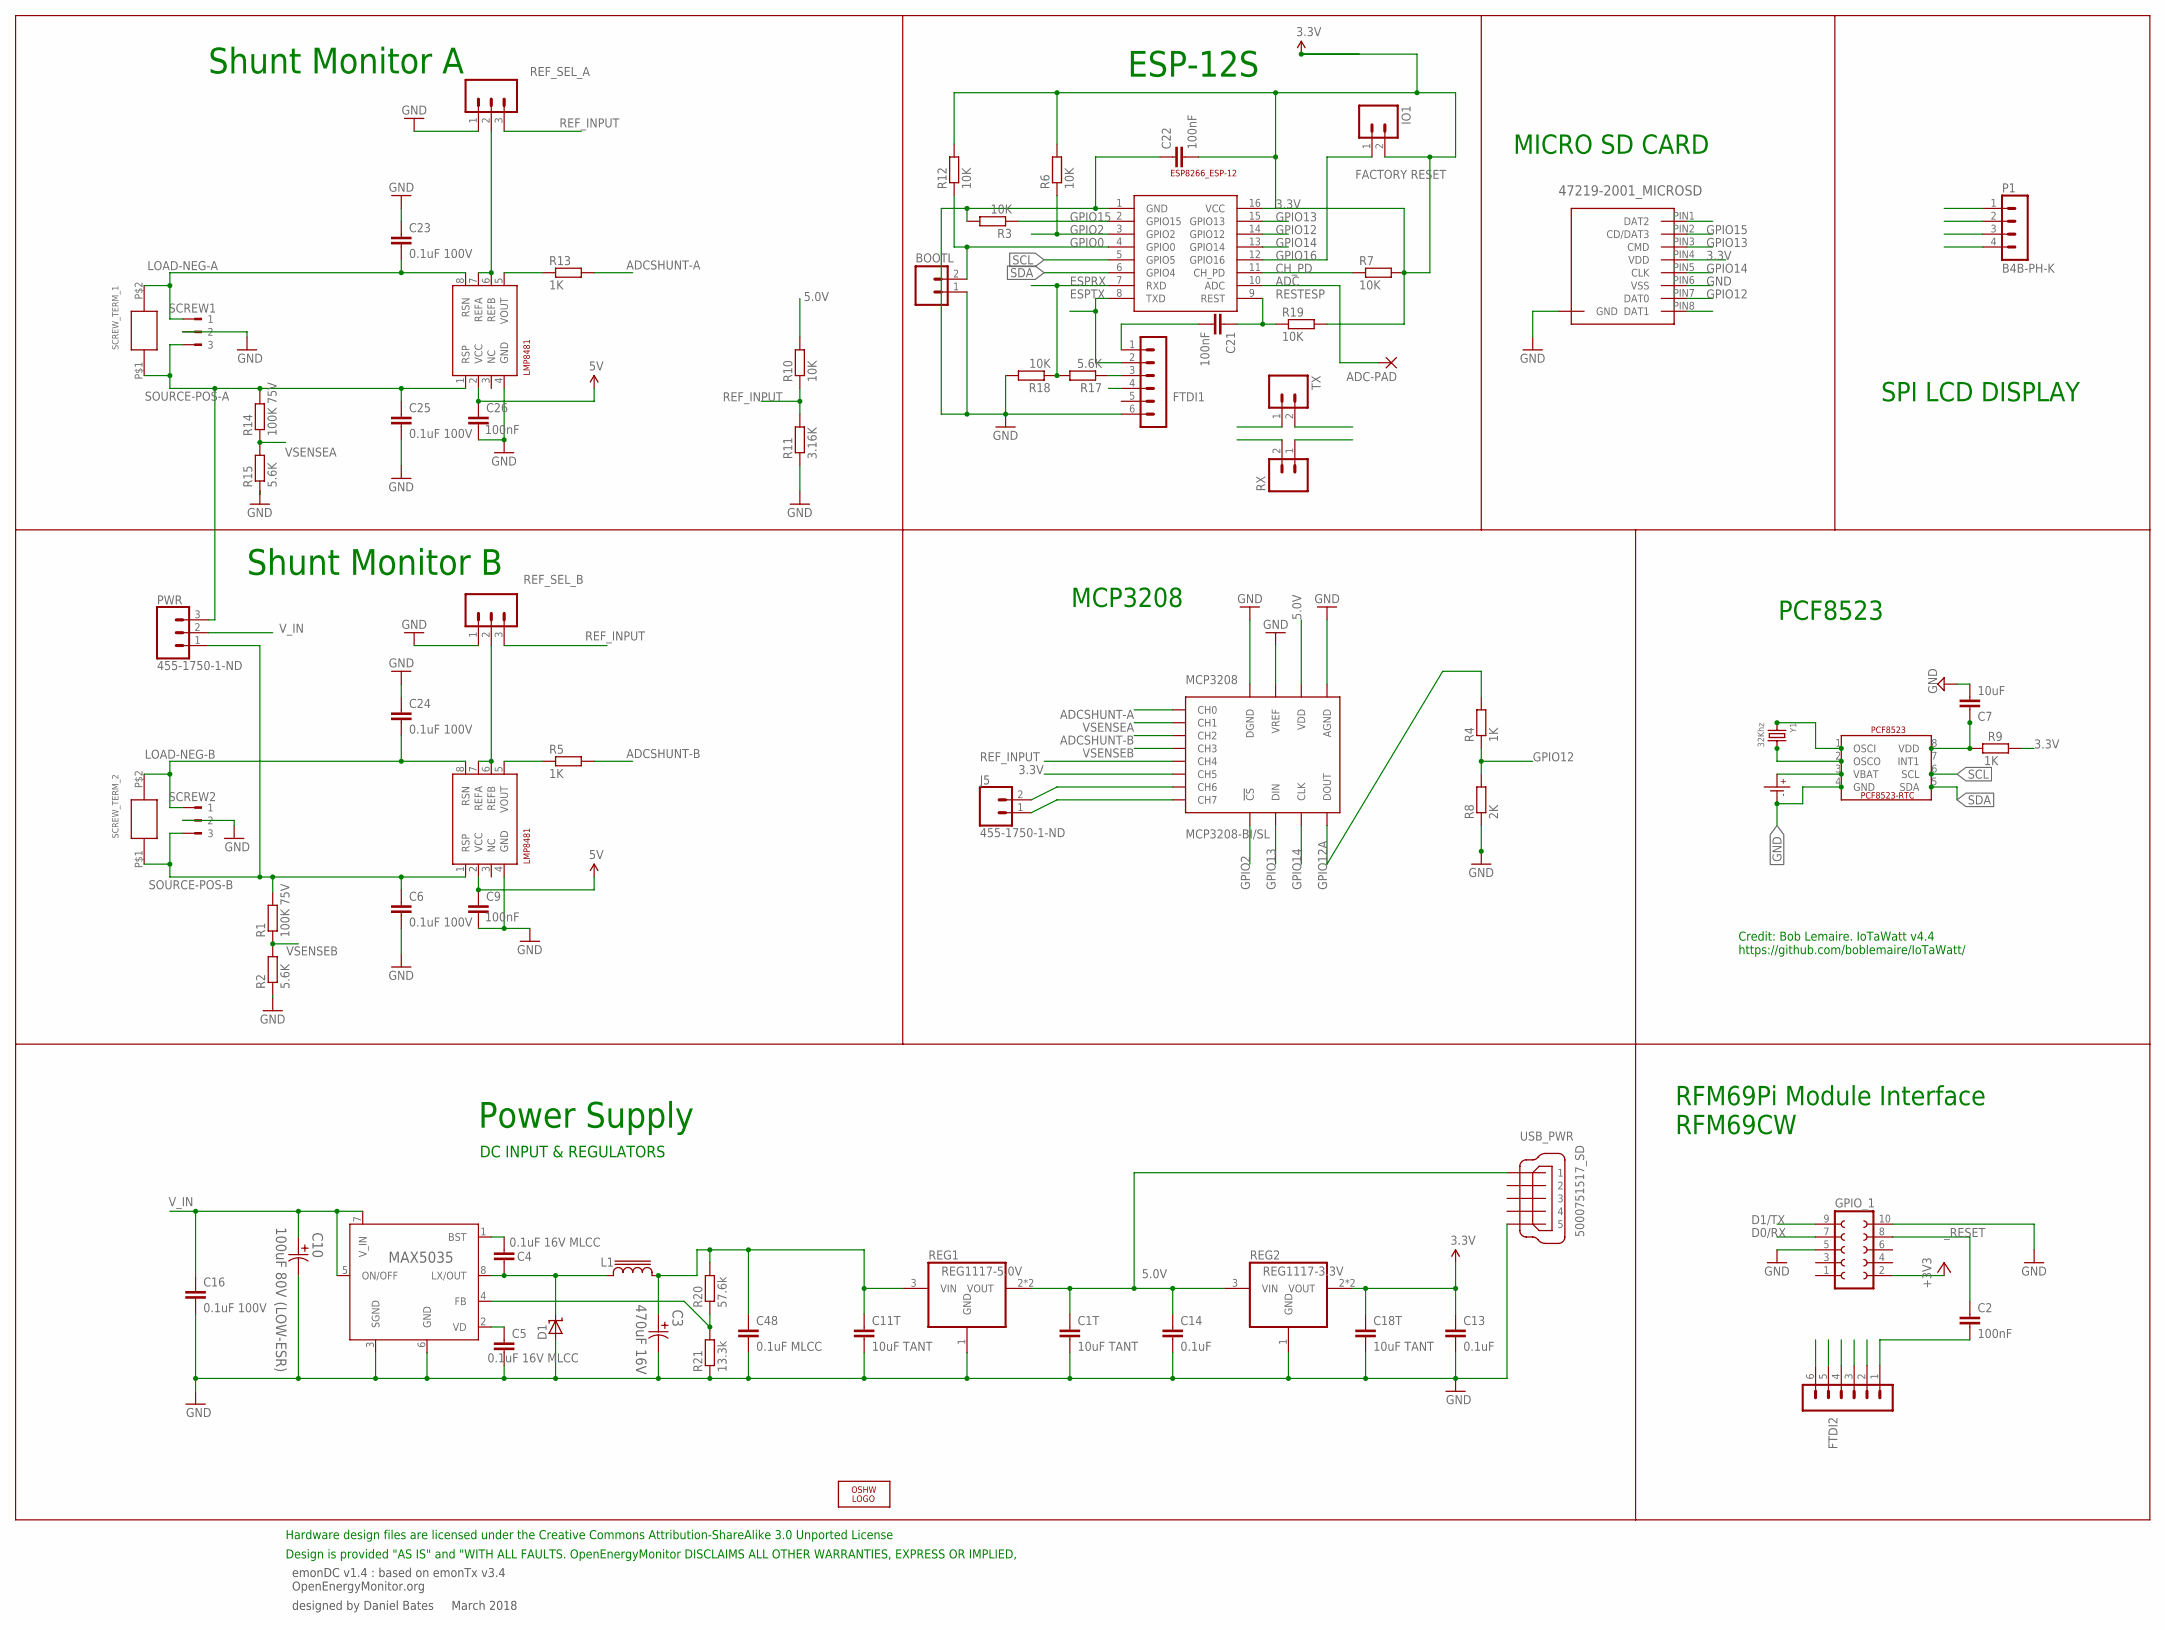
[picture p112: schematic emonDCduo-ESP v1.4.sch]

Parts:
ADC-PAD: 2,15/1,0
BOOTL: M02PTH; 1X02
C1T, C11T, C18T: 10uF TANT; C0603
C2, C21, C22: 100nF; C0603
C3: 470uF 16V; CAPAE830X1050N
C4, C5: 0.1uF 16V MLCC; C0603
C6, C23, C24, C25: 0.1uF 100V; C0603; MPN C1608X7S2A104K080AB
C7: 10uF; C0603
C9, C26: 100nF; C0603; MPN C1608X7S2A104K080AB
C10: 100uF 80V (LOW-ESR); CAPAE1350X1400N
C13, C14: 0.1uF; C0603
C16: 0.1uF 100V; C0603
C48: 0.1uF MLCC; C0603
CR1220: CR1220SMD; MPN Harwin S8411-45R
D1: MBRS1100T3G; SMB_1; MPN MBRS1100T3G
ESP-12: ESP8266_ESP-12; ESP8266-ESP12
FTDI1, FTDI2: FTDI; MA06-1
GPIO_1: FE05-2
IO1: M02PTH; 1X02
J5: 455-1750-1-ND; 1X02
L1: SRR1208; SSR1208; MPN SRR1208-151YL
LOGO1: OSHW_LOGO_6MILX0200-NT; OSHW_6X200_NOTEXT
MCP3208: MCP3208-BI/SL; SOIC16
P1: B4B-PH-K
PCF8523: PCF8523_RTC; SOIC_8
PWR: 455-1750-1-ND; 1X03
R1, R14: 100K 75V; R0603; MPN MCWR06X1003FTL
R2, R15: 5.6K; R0603; MPN MCWR06X5901FTL
R3, R6, R7, R12, R18, R19: 10K; R0603
R4: 1K; R0603; MPN MCWR06X5901FTL
R5, R9, R13: 1K; R0603
R8: 2K; R0603; MPN MCWR06X5901FTL
R10: 10K; 0309/12
R11: 3.16K; 0309/12
R17: 5.6K; R0603
R20: 57.6k; R0603
R21: 13.3k; R0603
REF_SEL_A: 455-1750-1-ND; 1X03; MPN 2212S-02SG-85
REF_SEL_B: 455-1750-1-ND; 1X03; MPN 2212S-02SG-85
REG0: MAX5035; 21-0111D_SBE-14; MPN MAX5035EASA+
REG1: REG1117-5.0V; SOT223; MPN REG1117-5.0
REG2: REG1117-3.3V; SOT223; MPN REG1117-3.3
RX: M02PTH; 1X02
SCREW1, SCREW2: 180-3
SCREW_TERM_1, SCREW_TERM_2: EBW_SERIES_15.2MM
SHUNTMON-A: LMP8481; S-PDSO-G08; MPN LMP8481MME-S/NOPB
SHUNTMON-B: LMP8481; S-PDSO-G08; MPN LMP8481MME-H/NOPB
TX: M02PTH; 1X02
U$4: 47219-2001_MICROSD
USB_PWR: 5000751517_SD
Y1: 32Khz; CRYSTAL_8X3.8

Connections:
3.3V: C13.1, C18T.1, C22.2, ESP-12.16 (VCC), GPIO_1.2, IO1.2, MCP3208.6 (CH5), P1.3, R6.2, R7.2, R9.2, R12.2, R19.2, REG2.2 (VOUT), REG2.4 (VOUT), U$4.PIN4 (VDD)
5.0V: C1T.1, C9.1, C14.1, C26.1, FTDI1.4, FTDI2.4, MCP3208.16 (VDD), R10.2, REG1.2 (VOUT), REG1.4 (VOUT), REG2.3 (VIN), SHUNTMON-A.2 (VCC), SHUNTMON-B.2 (VCC), USB_PWR.VBUS (1)
6.5V: C3.1, C11T.1, C48.1, L1.2, R20.2, REG1.3 (VIN)
ADC: ADC-PAD.1, ESP-12.10 (ADC)
ADCSHUNT-A: MCP3208.1 (CH0), R13.2
ADCSHUNT-B: MCP3208.3 (CH2), R5.2
BST: C4.1, REG0.1 (BST)
CH6: J5.2, MCP3208.7 (CH6)
CH7: J5.1, MCP3208.8 (CH7)
CH_PD: ESP-12.11 (CH_PD), R7.1
D0/RX: FTDI2.2, GPIO_1.7, TX.2
D1/TX: FTDI2.3, GPIO_1.9, RX.1
ESPRX: ESP-12.7 (RXD), R17.2, R18.1, RX.2
ESPTX: ESP-12.8 (TXD), FTDI1.2, TX.1
FB: R20.1, R21.2, REG0.4 (FB)
GND: BOOTL.1, C1T.2, C3.2, C5.2, C6.2, C7.2, C9.2, C10.2, C11T.2, C13.2, C14.2, C16.2, C18T.2, C22.1, C23.1, C24.1, C25.2, C26.2, C48.2, CR1220.P- (P$-), D1.A, ESP-12.1 (GND), FTDI1.6, FTDI2.6, GPIO_1.5, GPIO_1.10, MCP3208.9 (DGND), MCP3208.14 (AGND), MCP3208.15 (VREF), P1.4, PCF8523.4 (GND), R2.1, R3.2, R8.1, R11.1, R15.1, R18.2, R21.1, REF_SEL_A.1, REF_SEL_B.1, REG0.3 (SGND), REG0.6 (GND), REG1.1 (GND), REG2.1 (GND), SCREW1.2, SCREW2.2, SHUNTMON-A.4 (GND), SHUNTMON-B.4 (GND), U$4.P$1 (GND), U$4.P$2 (GND), U$4.P$3 (GND), U$4.P$4 (GND), U$4.PIN6 (VSS), USB_PWR.GND1 (5), USB_PWR.GND2 (5), USB_PWR.GND3 (5)
GPIO0: BOOTL.2, ESP-12.4 (GPIO0), R12.1
GPIO2: ESP-12.3 (GPIO2), MCP3208.10 (!CS), R6.1
GPIO12: ESP-12.14 (GPIO12), R4.1, R8.2, U$4.PIN7 (DAT0)
GPIO12A: MCP3208.12 (DOUT), R4.2
GPIO13: ESP-12.15 (GPIO13), MCP3208.11 (DIN), U$4.PIN3 (CMD)
GPIO14: ESP-12.13 (GPIO14), MCP3208.13 (CLK), U$4.PIN5 (CLK)
GPIO15: ESP-12.2 (GPIO15), R3.1, U$4.PIN2 (CD/DAT3)
GPIO16: ESP-12.12 (GPIO16), IO1.1
LOAD-NEG-A: C23.2, SCREW1.1, SCREW_TERM_1.P$2, SHUNTMON-A.8 (RSN)
LOAD-NEG-B: C24.2, SCREW2.1, SCREW_TERM_2.P$2, SHUNTMON-B.8 (RSN)
LX: C4.2, D1.C, L1.1, REG0.8 (LX/OUT)
unnamed: R13.1, SHUNTMON-A.5 (VOUT)
unnamed: R5.1, SHUNTMON-B.5 (VOUT)
unnamed: C7.1, PCF8523.8 (VDD), R9.1
unnamed: C21.2, FTDI1.1
unnamed: FTDI1.3, R17.1
unnamed: CR1220.P+ (P$+), PCF8523.3 (VBAT)
unnamed: PCF8523.2 (OSCO), Y1.P$4 (2)
unnamed: PCF8523.1 (OSCI), Y1.P$1 (1)
unnamed: C2.2, FTDI2.1
REF_A_INPUT: REF_SEL_A.2, SHUNTMON-A.6 (REFB), SHUNTMON-A.7 (REFA)
REF_B_INPUT: REF_SEL_B.2, SHUNTMON-B.6 (REFB), SHUNTMON-B.7 (REFA)
REF_INPUT: MCP3208.5 (CH4), R10.1, R11.2, REF_SEL_A.3, REF_SEL_B.3
RESTESP: C21.1, ESP-12.9 (REST), R19.1
SCL: ESP-12.5 (GPIO5), P1.2, PCF8523.6 (SCL)
SDA: ESP-12.6 (GPIO4), P1.1, PCF8523.5 (SDA)
SOURCE-POS-A: C25.1, PWR.3, R14.2, SCREW1.3, SCREW_TERM_1.P$1, SHUNTMON-A.1 (RSP)
SOURCE-POS-B: C6.1, PWR.1, R1.2, SCREW2.3, SCREW_TERM_2.P$1, SHUNTMON-B.1 (RSP)
VD: C5.1, REG0.2 (VD)
VSENSEA: MCP3208.2 (CH1), R14.1, R15.2
VSENSEB: MCP3208.4 (CH3), R1.1, R2.2
V_IN: C10.1, C16.1, PWR.2, REG0.5 (ON/OFF), REG0.7 (V_IN)
_RESET: C2.1, GPIO_1.8

Notes on the sheet:
emonDC v1.4 : based on emonTx v3.4 OpenEnergyMonitor.org
designed by Daniel Bates March 2018
Power Supply
Design is provided "AS IS" and "WITH ALL FAULTS. OpenEnergyMonitor DISCLAIMS ALL OTHER WARRANTIES, EXPRESS OR IMPLIED,
Hardware design files are licensed under the Creative Commons Attribution-ShareAlike 3.0 Unported License
DC INPUT & REGULATORS
Shunt Monitor B
Shunt Monitor A
FACTORY RESET
ESP-12S
MICRO SD CARD
RFM69Pi Module Interface RFM69CW
MCP3208
PCF8523
Credit: Bob Lemaire. IoTaWatt v4.4 https://github.com/boblemaire/IoTaWatt/
SPI LCD DISPLAY

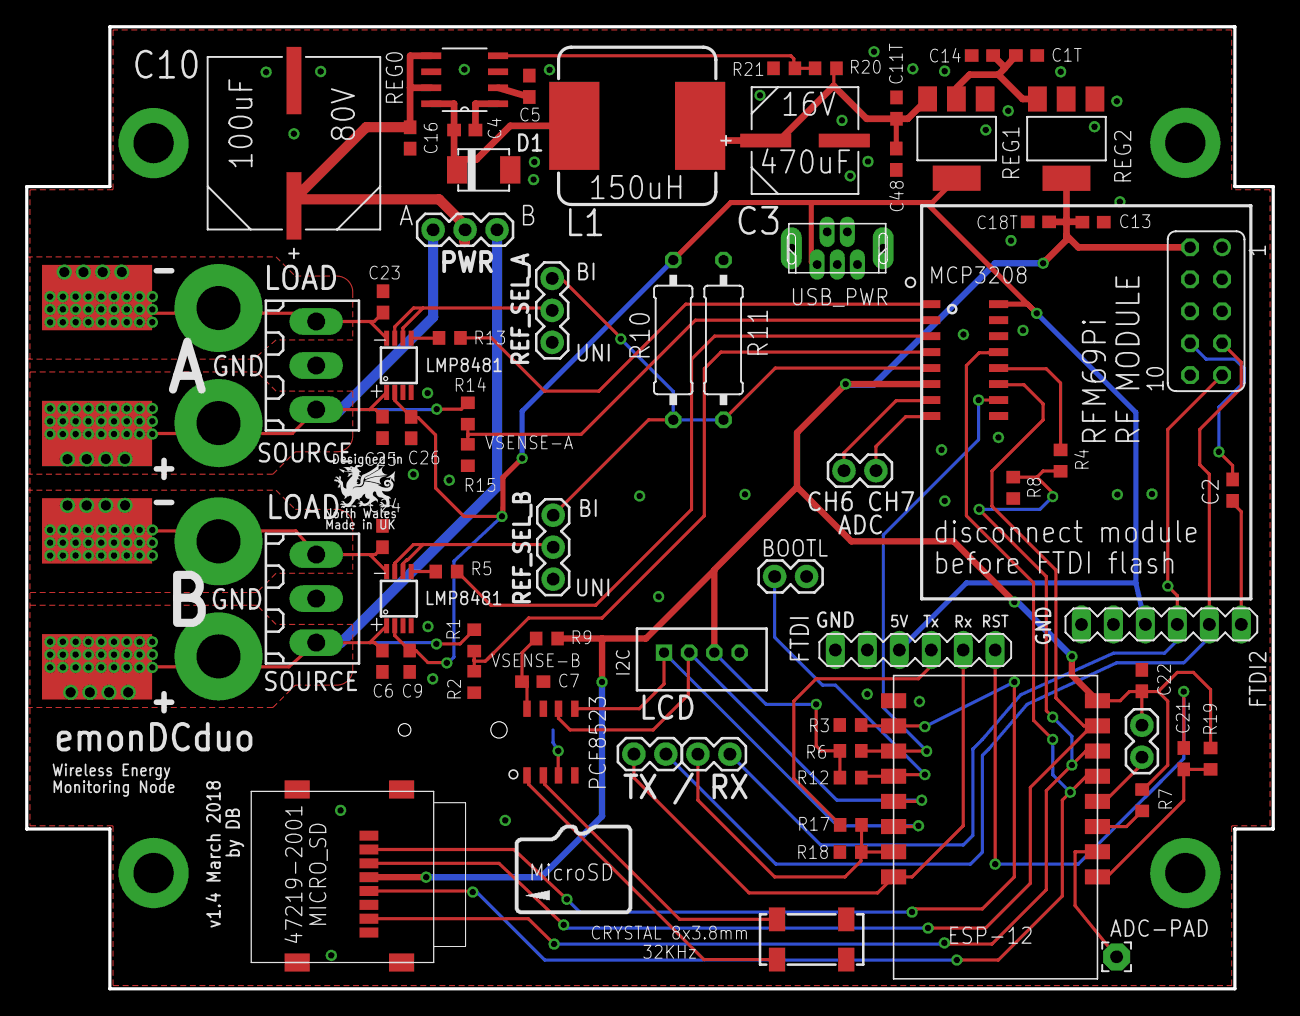
[picture p113: board emonDCduo-ESP v1.4.brd from above]

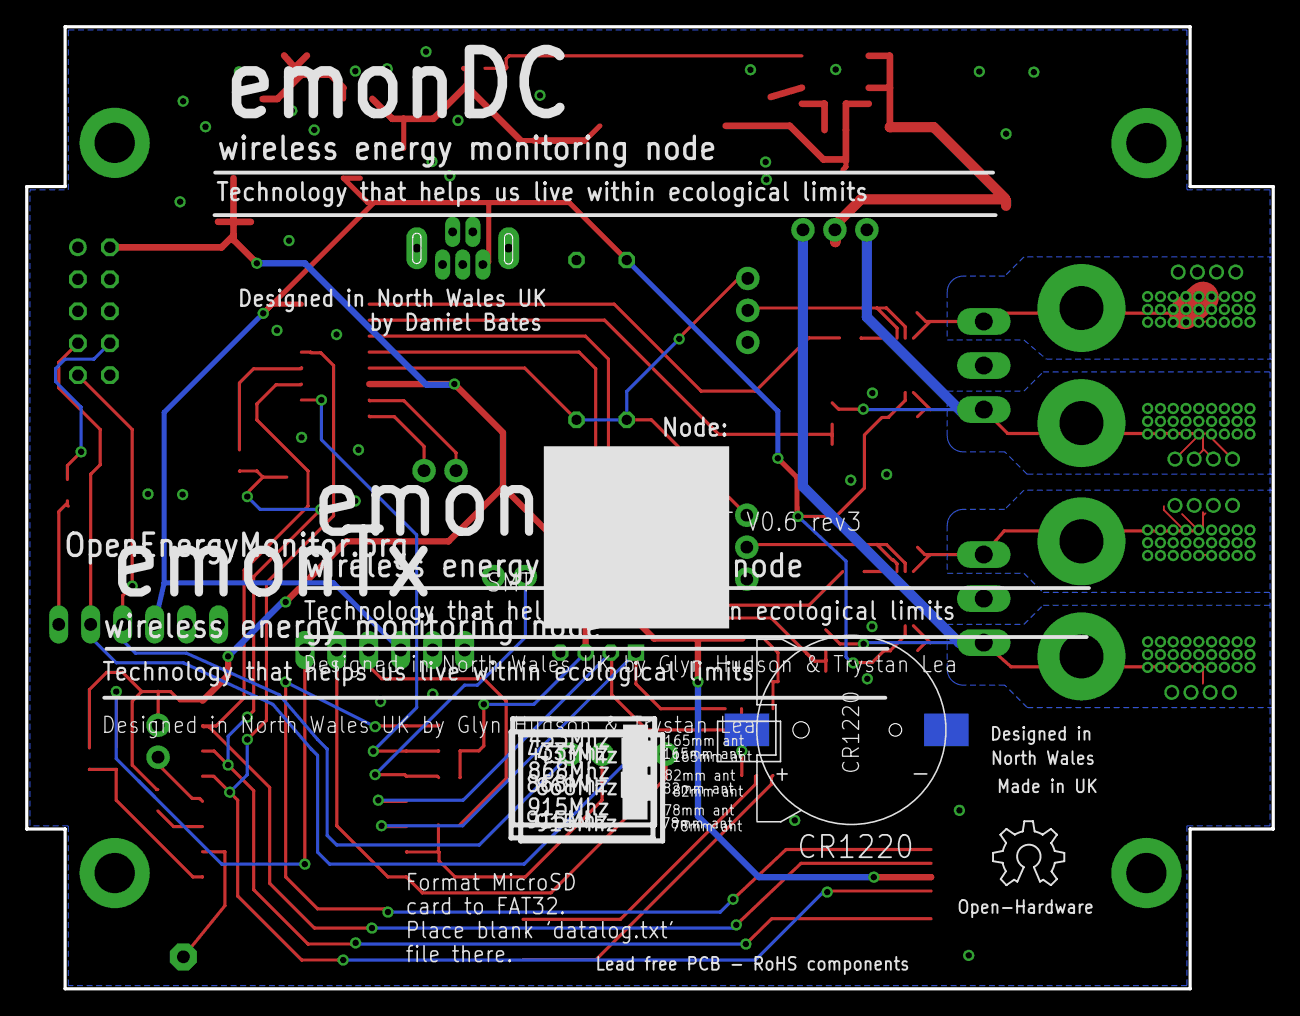
[picture p114: board emonDCduo-ESP v1.4.brd from below]

Board: 2 copper layers, 99.1 x 76.5 mm, 73 parts (2 on the bottom side), 49 nets.
