danbates2/emonDC/emonDCmini/emonDCmini v0.5.brd

## EAGLE design emonDCmini/emonDCmini v0.5.brd (2017-06-17, an earlier design)

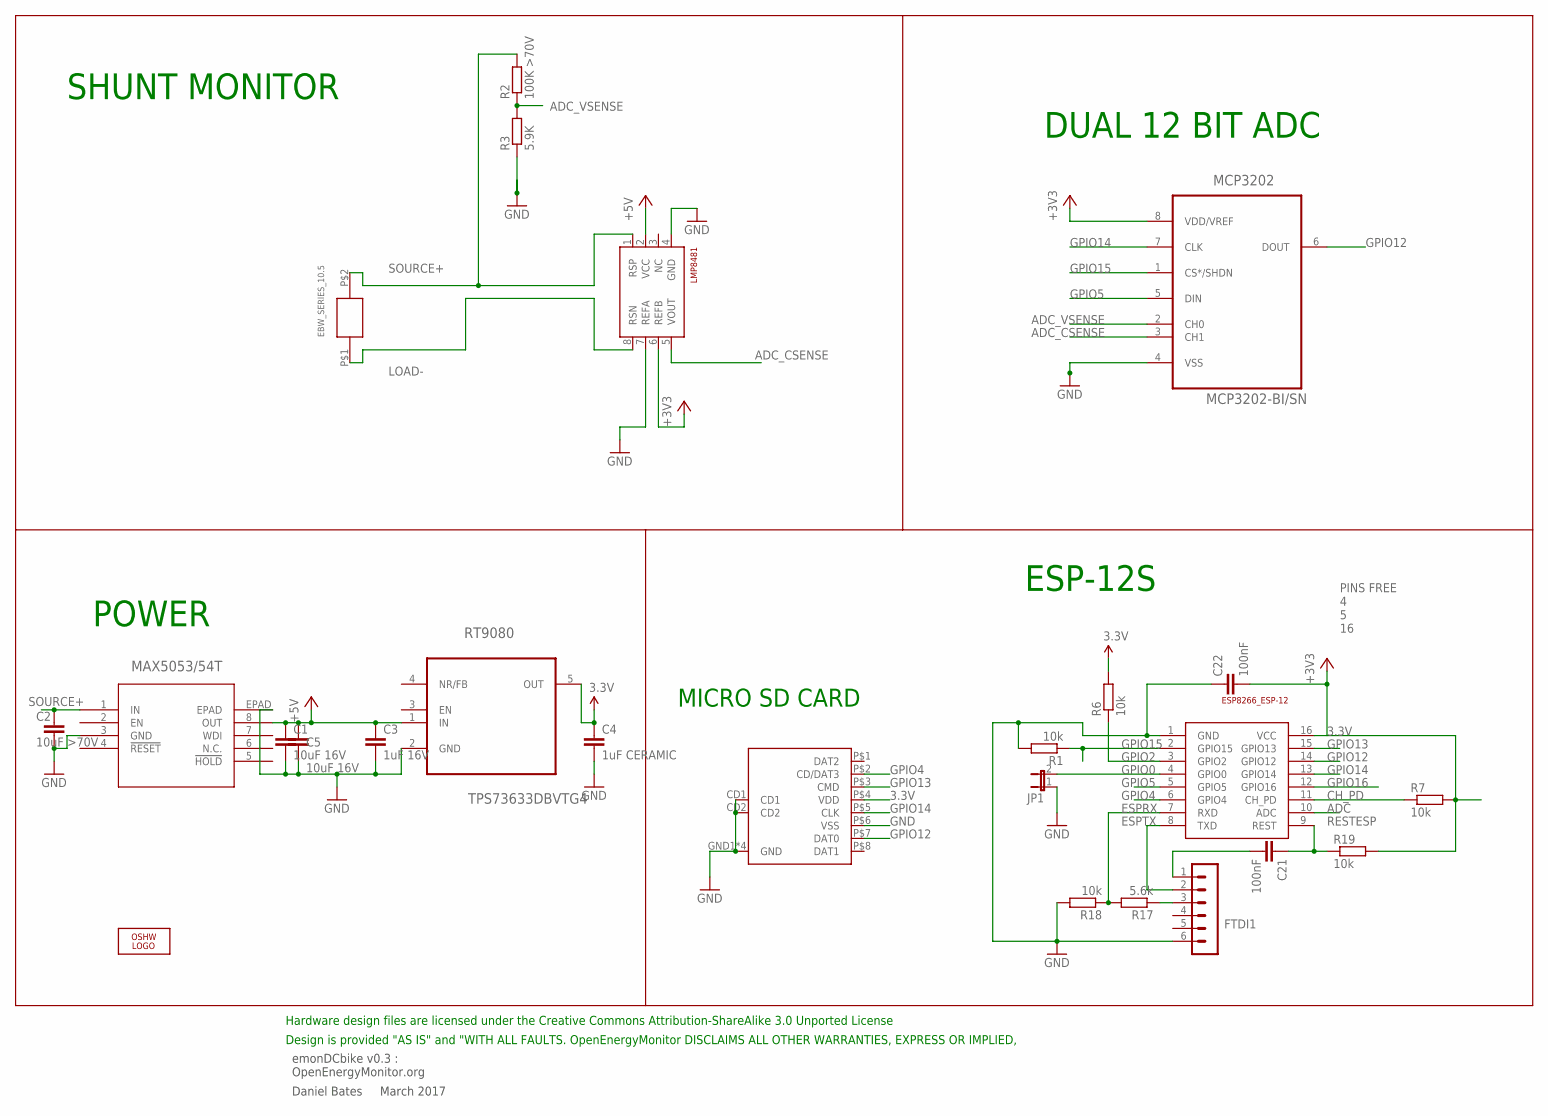
[picture p115: schematic emonDCmini v0.5.sch]

Parts:
C1, C5: 10uF 16V; C0603
C2: 10uF >70V; C0603
C3: 1uF 16V; C0603
C4: 1uF CERAMIC; C0603
C21, C22: 100nF; C0603
EBW_SERIES_10.5: EBW_SERIES_10.5MM
ESP-12: ESP8266_ESP-12; ESP8266-ESP12
FTDI1: FTDI-ESP; MA06-1
JP1: JP1E; JP1
LMP8481: LMP8481-H; S-PDSO-G08
LOGO1: OSHW_LOGO_6MILX0200-NT; OSHW_6X200_NOTEXT
MAX5053: MAX5023TASA-T21-0111D_SBE-14-L; 21-0111D_SBE-14-L
MCP3202: MCP3202-BI/SN; SOIC127P600X175-8N
R1, R6, R7, R18, R19: 10k; R0603
R2: 100K >70V; R0603; MPN MCWR06X1003FTL
R3: 5.9K; R0603; MPN MCWR06X5901FTL
R17: 5.6k; R0603
RT9080: TPS73633DBVTG4; SOT95P280X145-5N
U$2: MOLEX_MICRO_SD_1040310811; MOLEX_MICROSD_EXPOSED

Connections:
3.3V: C4.1, C22.2, ESP-12.16 (VCC), LMP8481.6 (REFB), MCP3202.8 (VDD/VREF), R6.2, R7.2, R19.2, RT9080.5 (OUT), U$2.P$4 (VDD)
+5V: C1.1, C3.1, C5.1, MAX5053.8 (OUT), RT9080.1 (IN)
ADC: ESP-12.10 (ADC)
ADC_CSENSE: LMP8481.5 (VOUT), MCP3202.3 (CH1)
ADC_VSENSE: MCP3202.2 (CH0), R2.1, R3.2
CH_PD: ESP-12.11 (CH_PD), R7.1
ESPRX: ESP-12.7 (RXD), R17.2, R18.1
ESPTX: ESP-12.8 (TXD), FTDI1.2
GND: C1.2, C2.2, C3.2, C4.2, C5.2, C22.1, ESP-12.1 (GND), FTDI1.6, JP1.1, LMP8481.4 (GND), LMP8481.7 (REFA), MAX5053.3 (GND), MAX5053.EPAD, MCP3202.4 (VSS), R1.2, R3.1, R18.2, RT9080.2 (GND), U$2.CD1, U$2.CD2, U$2.GND1 (GND), U$2.GND2 (GND), U$2.GND3 (GND), U$2.GND4 (GND), U$2.P$6 (VSS)
GPIO0: ESP-12.4 (GPIO0), JP1.2
GPIO2: ESP-12.3 (GPIO2), R6.1
GPIO4: ESP-12.6 (GPIO4), U$2.P$2 (CD/DAT3)
GPIO5: ESP-12.5 (GPIO5), MCP3202.5 (DIN)
GPIO12: ESP-12.14 (GPIO12), MCP3202.6 (DOUT), U$2.P$7 (DAT0)
GPIO13: ESP-12.15 (GPIO13), U$2.P$3 (CMD)
GPIO14: ESP-12.13 (GPIO14), MCP3202.7 (CLK), U$2.P$5 (CLK)
GPIO15: ESP-12.2 (GPIO15), MCP3202.1 (CS*/SHDN), R1.1
GPIO16: ESP-12.12 (GPIO16)
LOAD-: EBW_SERIES_10.5.P$1, LMP8481.8 (RSN)
unnamed: FTDI1.3, R17.1
RESTESP: C21.1, ESP-12.9 (REST), R19.1
RST: C21.2, FTDI1.1
SOURCE+: C2.1, EBW_SERIES_10.5.P$2, LMP8481.1 (RSP), MAX5053.1 (IN), R2.2

Notes on the sheet:
emonDCbike v0.3 : OpenEnergyMonitor.org
Daniel Bates March 2017
Design is provided "AS IS" and "WITH ALL FAULTS. OpenEnergyMonitor DISCLAIMS ALL OTHER WARRANTIES, EXPRESS OR IMPLIED,
Hardware design files are licensed under the Creative Commons Attribution-ShareAlike 3.0 Unported License
SHUNT MONITOR
ESP-12S
MICRO SD CARD
PINS FREE 4 5 16
POWER
DUAL 12 BIT ADC

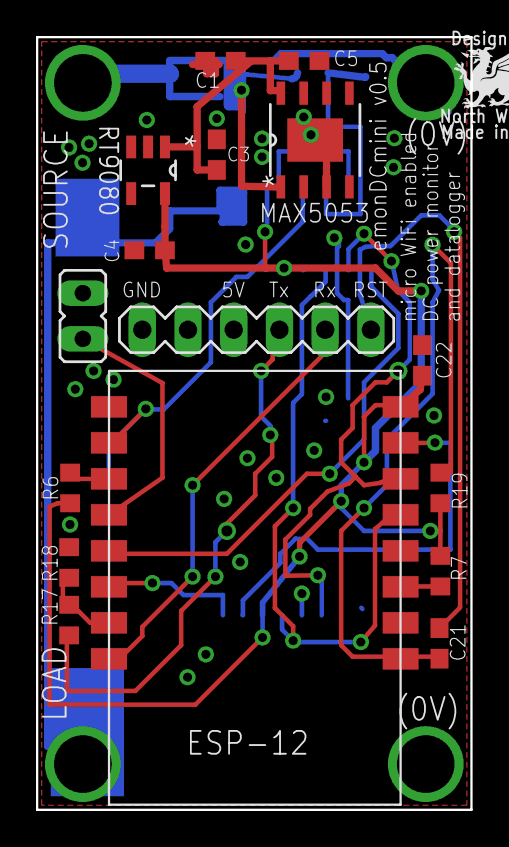
[picture p116: board emonDCmini v0.5.brd from above]

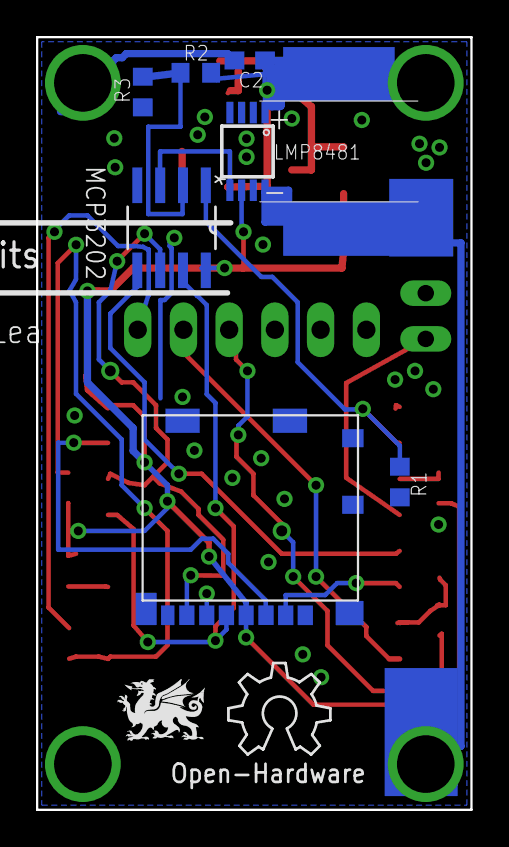
[picture p117: board emonDCmini v0.5.brd from below]

Board: 2 copper layers, 24.1 x 42.9 mm, 26 parts (10 on the bottom side), 21 nets.

Other parts of the board:
U$3: DRAGON_LOGO_NOTEXT
