danbates2/emonDC/emonDCmini/emonDCmini v0.6.brd

## EAGLE design emonDCmini/emonDCmini v0.6.brd (2017-07-12)

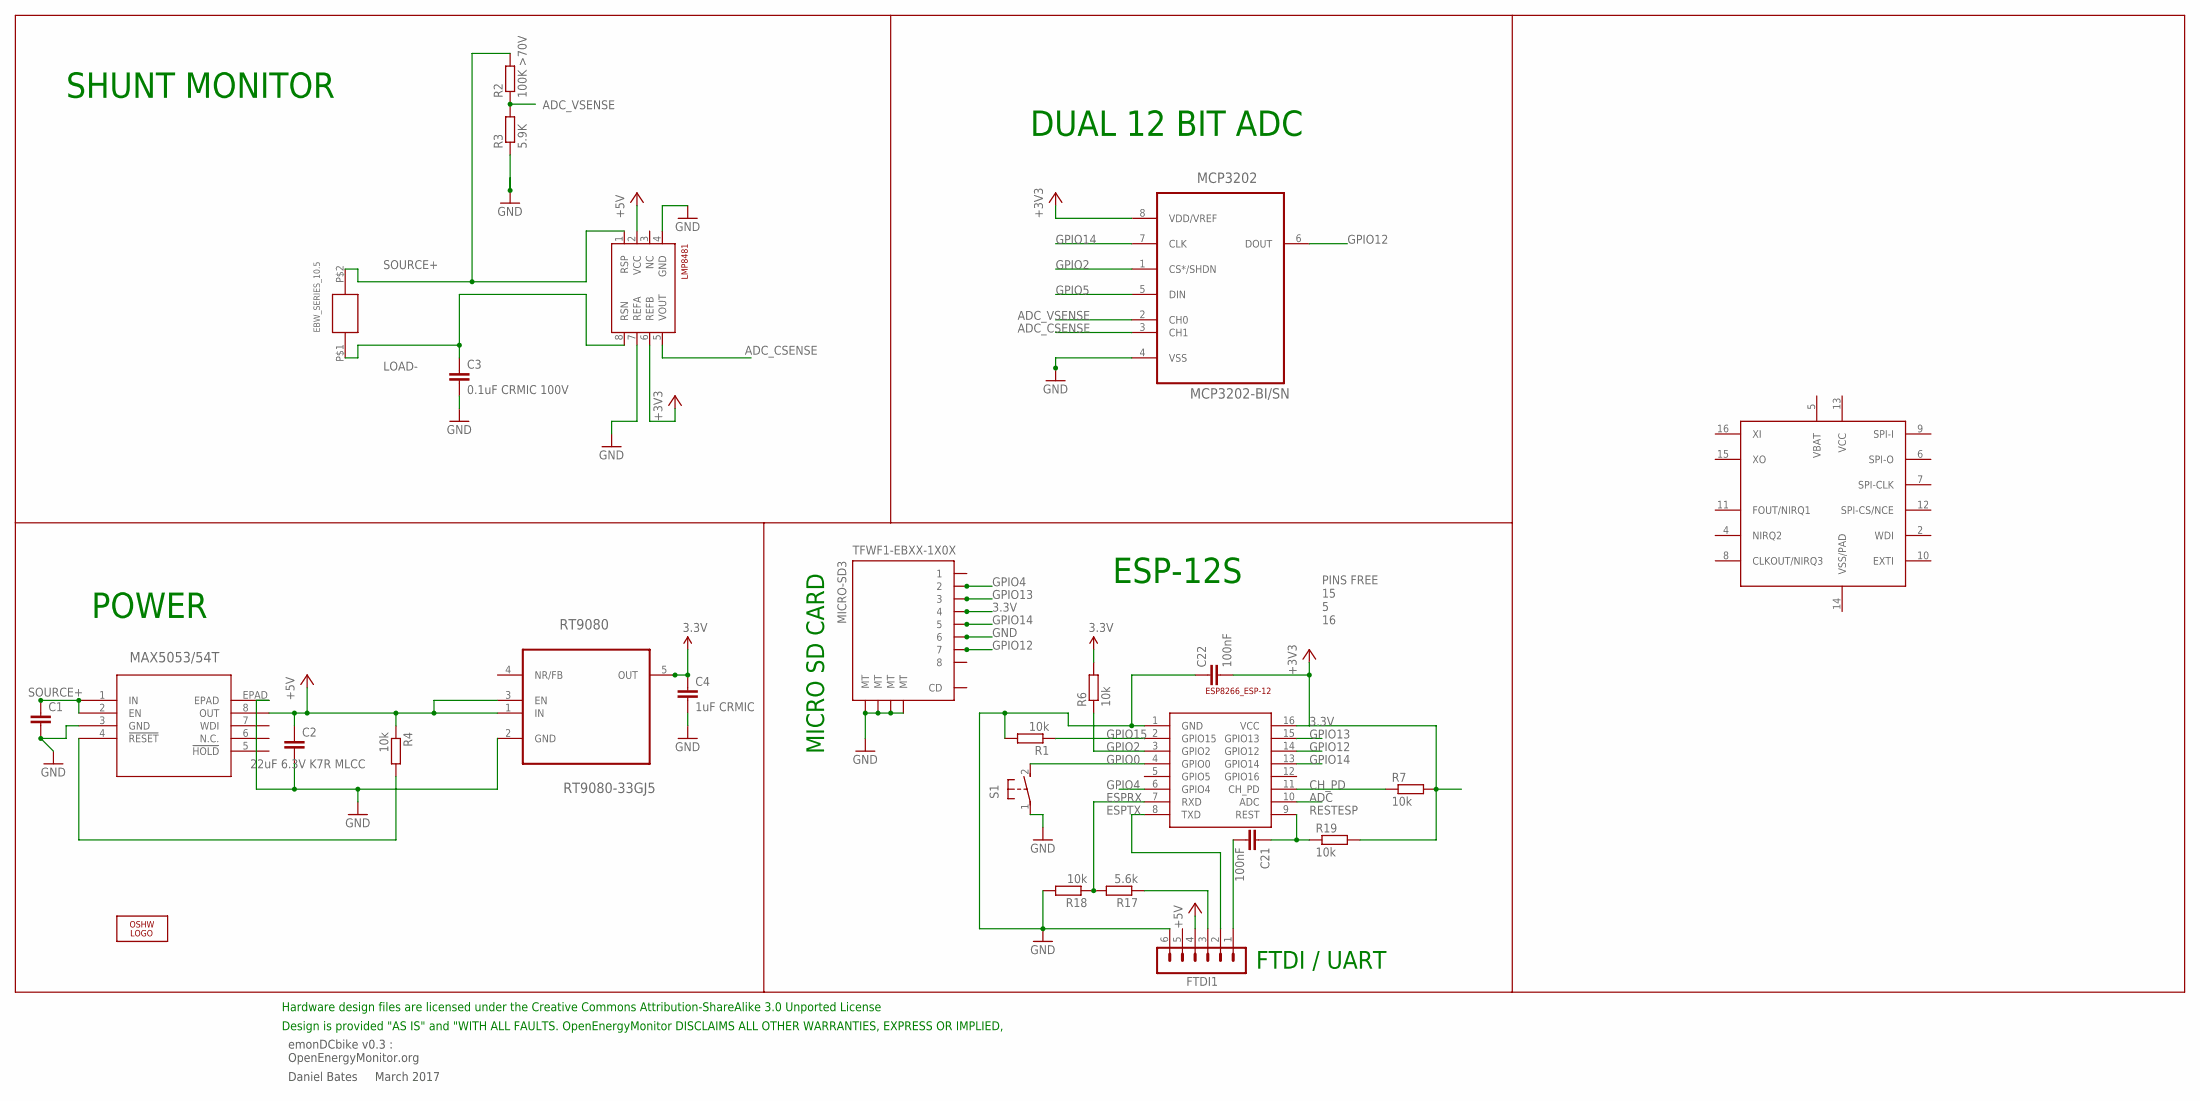
[picture p118: schematic emonDCmini v0.6.sch]

Parts:
AB0815: AB0815_RTC; QFN16
C1: C-EUC1206; C1206
C2: 22uF 6.3V K7R MLCC; C1206
C3: 0.1uF CRMIC 100V; C0603
C4: 1uF CRMIC; C0603
C21, C22: 100nF; C0603
EBW_SERIES_10.5: EBW_SERIES_10.5MM
ESP-12: ESP8266_ESP-12; ESP8266-ESP12
FTDI1: FTDI-ESP; MA06-1
LMP8481: LMP8481-H; S-PDSO-G08
LOGO1: OSHW_LOGO_6MILX0200-NT; OSHW_6X200_NOTEXT
MAX5053: MAX5023TASA-T21-0111D_SBE-14-L; 21-0111D_SBE-14-L
MCP3202: MCP3202-BI/SN; SOIC127P600X175-8N
R1, R4, R6, R7, R18, R19: 10k; R0603
R2: 100K >70V; R0603; MPN MCWR06X1003FTL
R3: 5.9K; R0603; MPN MCWR06X5901FTL
R17: 5.6k; R0603
RT9080: RT9080-33GJ5; TSOT-23-5
S1: DTSM-3
TFWF1-EBXX-1X0X: MICRO-SD3; TF-MICRO-SD_PP3*

Connections:
3.3V: C4.1, C22.2, ESP-12.16 (VCC), LMP8481.6 (REFB), MCP3202.8 (VDD/VREF), R6.2, R7.2, R19.2, RT9080.5 (OUT), TFWF1-EBXX-1X0X.4
+5V: C2.1, FTDI1.4, MAX5053.8 (OUT), R4.1, RT9080.1 (IN), RT9080.3 (EN)
ADC: ESP-12.10 (ADC)
ADC_CSENSE: LMP8481.5 (VOUT), MCP3202.3 (CH1)
ADC_VSENSE: MCP3202.2 (CH0), R2.1, R3.2
CH_PD: ESP-12.11 (CH_PD), R7.1
ESPRX: ESP-12.7 (RXD), R17.2, R18.1
ESPTX: ESP-12.8 (TXD), FTDI1.2
GND: C1.2, C2.2, C3.2, C4.2, C22.1, ESP-12.1 (GND), FTDI1.6, LMP8481.4 (GND), LMP8481.7 (REFA), MAX5053.3 (GND), MAX5053.EPAD, MCP3202.4 (VSS), R1.2, R3.1, R18.2, RT9080.2 (GND), S1.1, TFWF1-EBXX-1X0X.6, TFWF1-EBXX-1X0X.MT1 (MT), TFWF1-EBXX-1X0X.MT2 (MT), TFWF1-EBXX-1X0X.MT3 (MT), TFWF1-EBXX-1X0X.MT4 (MT)
GPIO0: ESP-12.4 (GPIO0), S1.2
GPIO2: ESP-12.3 (GPIO2), MCP3202.1 (CS*/SHDN), R6.1
GPIO4: ESP-12.6 (GPIO4), TFWF1-EBXX-1X0X.2
GPIO5: MCP3202.5 (DIN)
GPIO12: ESP-12.14 (GPIO12), MCP3202.6 (DOUT), TFWF1-EBXX-1X0X.7
GPIO13: ESP-12.15 (GPIO13), TFWF1-EBXX-1X0X.3
GPIO14: ESP-12.13 (GPIO14), MCP3202.7 (CLK), TFWF1-EBXX-1X0X.5
GPIO15: ESP-12.2 (GPIO15), R1.1
LOAD-: C3.1, EBW_SERIES_10.5.P$1, LMP8481.8 (RSN)
unnamed: MAX5053.4 (!RESET), R4.2
unnamed: FTDI1.3, R17.1
RESTESP: C21.1, ESP-12.9 (REST), R19.1
RST: C21.2, FTDI1.1
SOURCE+: C1.1, EBW_SERIES_10.5.P$2, LMP8481.1 (RSP), MAX5053.1 (IN), MAX5053.2 (EN), R2.2

Notes on the sheet:
emonDCbike v0.3 : OpenEnergyMonitor.org
Daniel Bates March 2017
Design is provided "AS IS" and "WITH ALL FAULTS. OpenEnergyMonitor DISCLAIMS ALL OTHER WARRANTIES, EXPRESS OR IMPLIED,
Hardware design files are licensed under the Creative Commons Attribution-ShareAlike 3.0 Unported License
SHUNT MONITOR
ESP-12S
MICRO SD CARD
PINS FREE 15 5 16
POWER
DUAL 12 BIT ADC
FTDI / UART

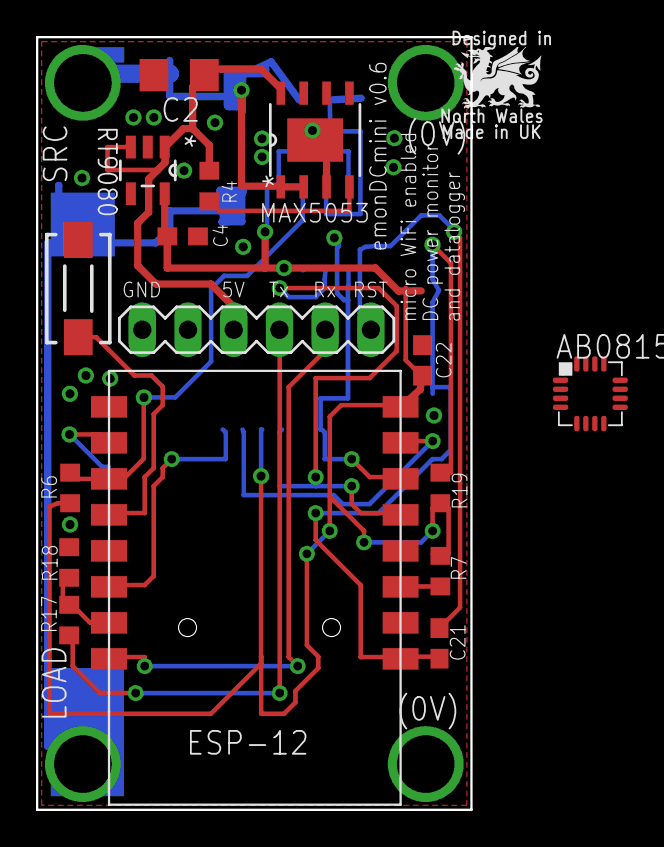
[picture p119: board emonDCmini v0.6.brd from above]

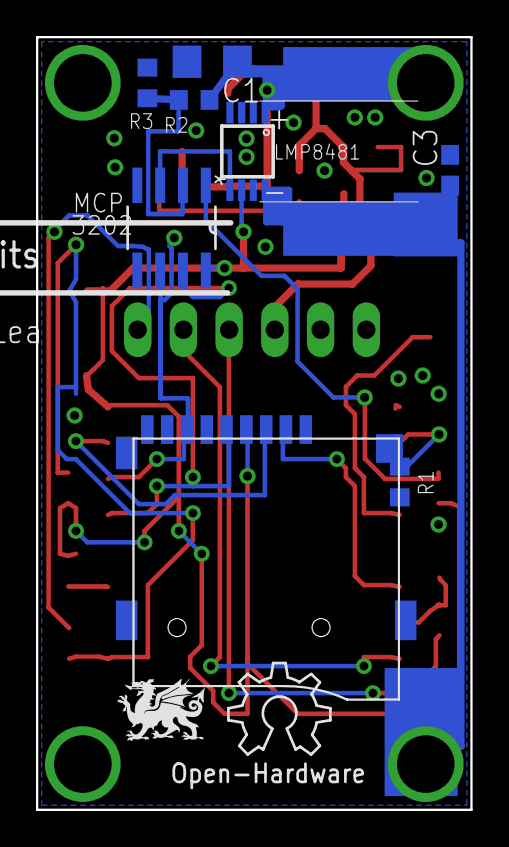
[picture p120: board emonDCmini v0.6.brd from below]

Board: 2 copper layers, 24.1 x 42.9 mm, 27 parts (11 on the bottom side), 21 nets.

Other parts of the board:
U$3: DRAGON_LOGO_NOTEXT
