danbates2/emonDC/emonDCmini/emonBike v0.1.brd

## EAGLE design emonDCmini/emonBike v0.1.brd (2017-01-28, an earlier design)

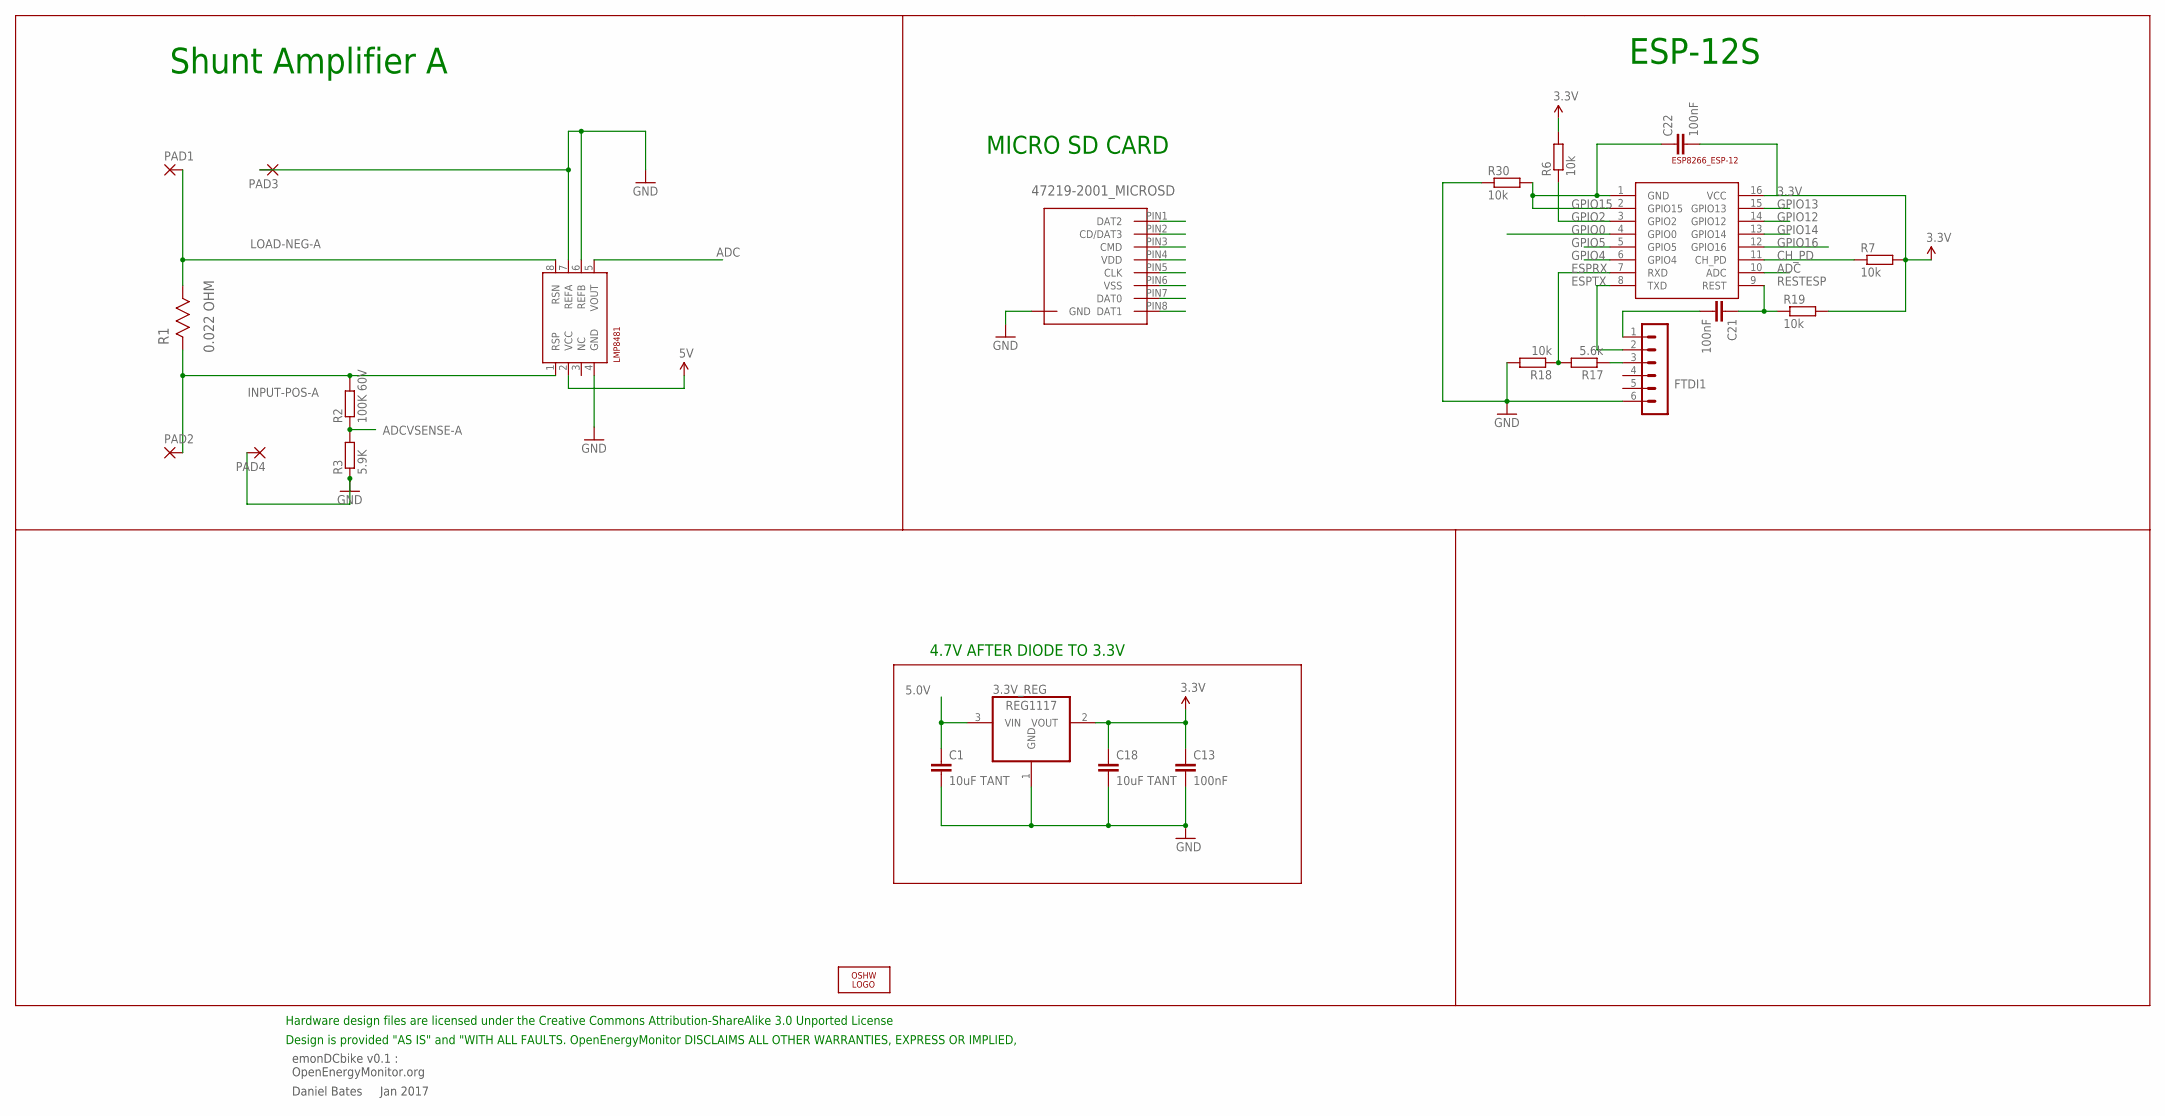
[picture p121: schematic emonBike v0.1.sch]

Parts:
3.3V_REG: REG1117; SOT223
C1, C18: 10uF TANT; C0603
C13, C21, C22: 100nF; C0603
ESP-12: ESP8266_ESP-12; ESP8266-ESP12
FTDI1: FTDI-ESP; MA06-1
LOGO1: OSHW_LOGO_6MILX0200-NT; OSHW_6X200_NOTEXT
PAD1, PAD2, PAD3, PAD4: 3,81/1,4
R1: 0.022 OHM; RESC3216X71N
R2: 100K 60V; R0603; MPN MCWR06X1003FTL
R3: 5.9K; R0603; MPN MCWR06X5901FTL
R6, R7, R18, R19, R30: 10k; R0603
R17: 5.6k; R0603
SHUNTMON-A: LMP8481; S-PDSO-G08; MPN LMP8481MME-S/NOPB
U$1: 47219-2001_MICROSD

Connections:
3.3V: 3.3V_REG.2 (VOUT), C13.1, C18.1, C22.2, ESP-12.16 (VCC), R6.2, R7.2, R19.2, U$1.PIN4 (VDD)
4.7V: SHUNTMON-A.2 (VCC)
5.0V: 3.3V_REG.3 (VIN), C1.1
ADC: ESP-12.10 (ADC), SHUNTMON-A.5 (VOUT)
ADCVSENSE-A: R2.1, R3.2
CH_PD: ESP-12.11 (CH_PD), R7.1
ESPRX: ESP-12.7 (RXD), R17.2, R18.1
ESPTX: ESP-12.8 (TXD), FTDI1.2
GND: 3.3V_REG.1 (GND), C1.2, C13.2, C18.2, FTDI1.6, PAD3.1, PAD4.1, R3.1, R18.2, R30.1, SHUNTMON-A.4 (GND), SHUNTMON-A.6 (REFB), SHUNTMON-A.7 (REFA), U$1.P$1 (GND), U$1.P$2 (GND), U$1.P$3 (GND), U$1.P$4 (GND), U$1.PIN6 (VSS)
GPIO0: ESP-12.4 (GPIO0)
GPIO2: ESP-12.3 (GPIO2), R6.1, U$1.PIN2 (CD/DAT3)
GPIO4: ESP-12.6 (GPIO4)
GPIO5: ESP-12.5 (GPIO5)
GPIO12: ESP-12.14 (GPIO12), U$1.PIN7 (DAT0)
GPIO13: ESP-12.15 (GPIO13), U$1.PIN3 (CMD)
GPIO14: ESP-12.13 (GPIO14), U$1.PIN5 (CLK)
GPIO15: C22.1, ESP-12.1 (GND), ESP-12.2 (GPIO15), R30.2
GPIO16: ESP-12.12 (GPIO16)
INPUT-POS-A: PAD2.1, R1.2 (R2), R2.2, SHUNTMON-A.1 (RSP)
LOAD-NEG-A: PAD1.1, R1.1 (R1), SHUNTMON-A.8 (RSN)
unnamed: C21.2, FTDI1.1
unnamed: FTDI1.3, R17.1
RESTESP: C21.1, ESP-12.9 (REST), R19.1

Notes on the sheet:
emonDCbike v0.1 : OpenEnergyMonitor.org
Daniel Bates Jan 2017
Design is provided "AS IS" and "WITH ALL FAULTS. OpenEnergyMonitor DISCLAIMS ALL OTHER WARRANTIES, EXPRESS OR IMPLIED,
Hardware design files are licensed under the Creative Commons Attribution-ShareAlike 3.0 Unported License
Shunt Amplifier A
ESP-12S
MICRO SD CARD
4.7V AFTER DIODE TO 3.3V

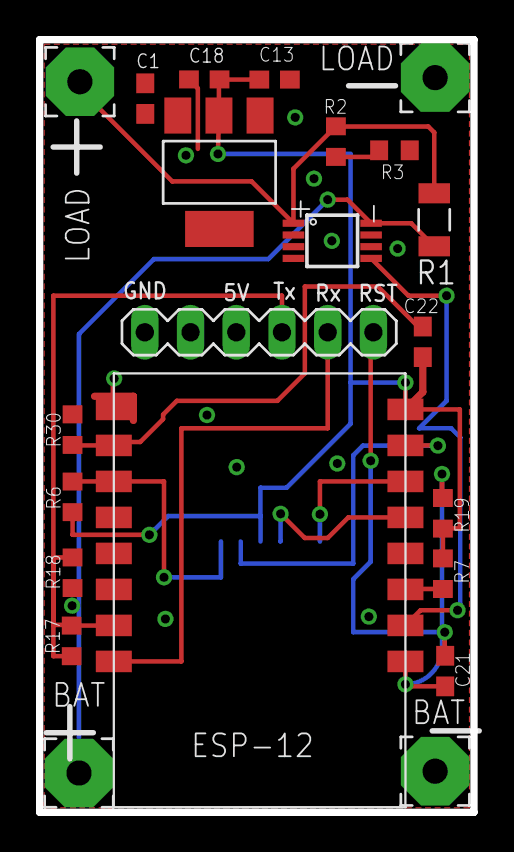
[picture p122: board emonBike v0.1.brd from above]

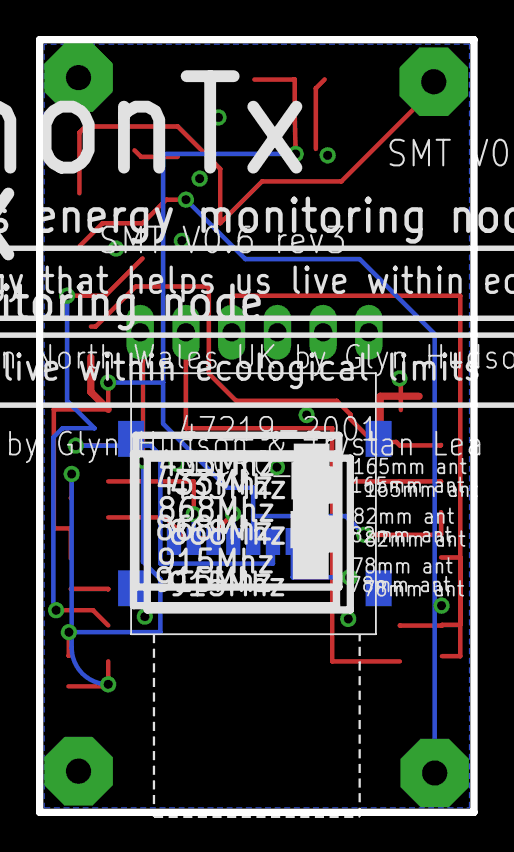
[picture p123: board emonBike v0.1.brd from below]

Board: 2 copper layers, 24.1 x 42.9 mm, 24 parts (2 on the bottom side), 18 nets.
