danbates2/emonDC/emonDCmini/emonBike v0.2.brd

## EAGLE design emonDCmini/emonBike v0.2.brd (2017-03-29, an earlier design)

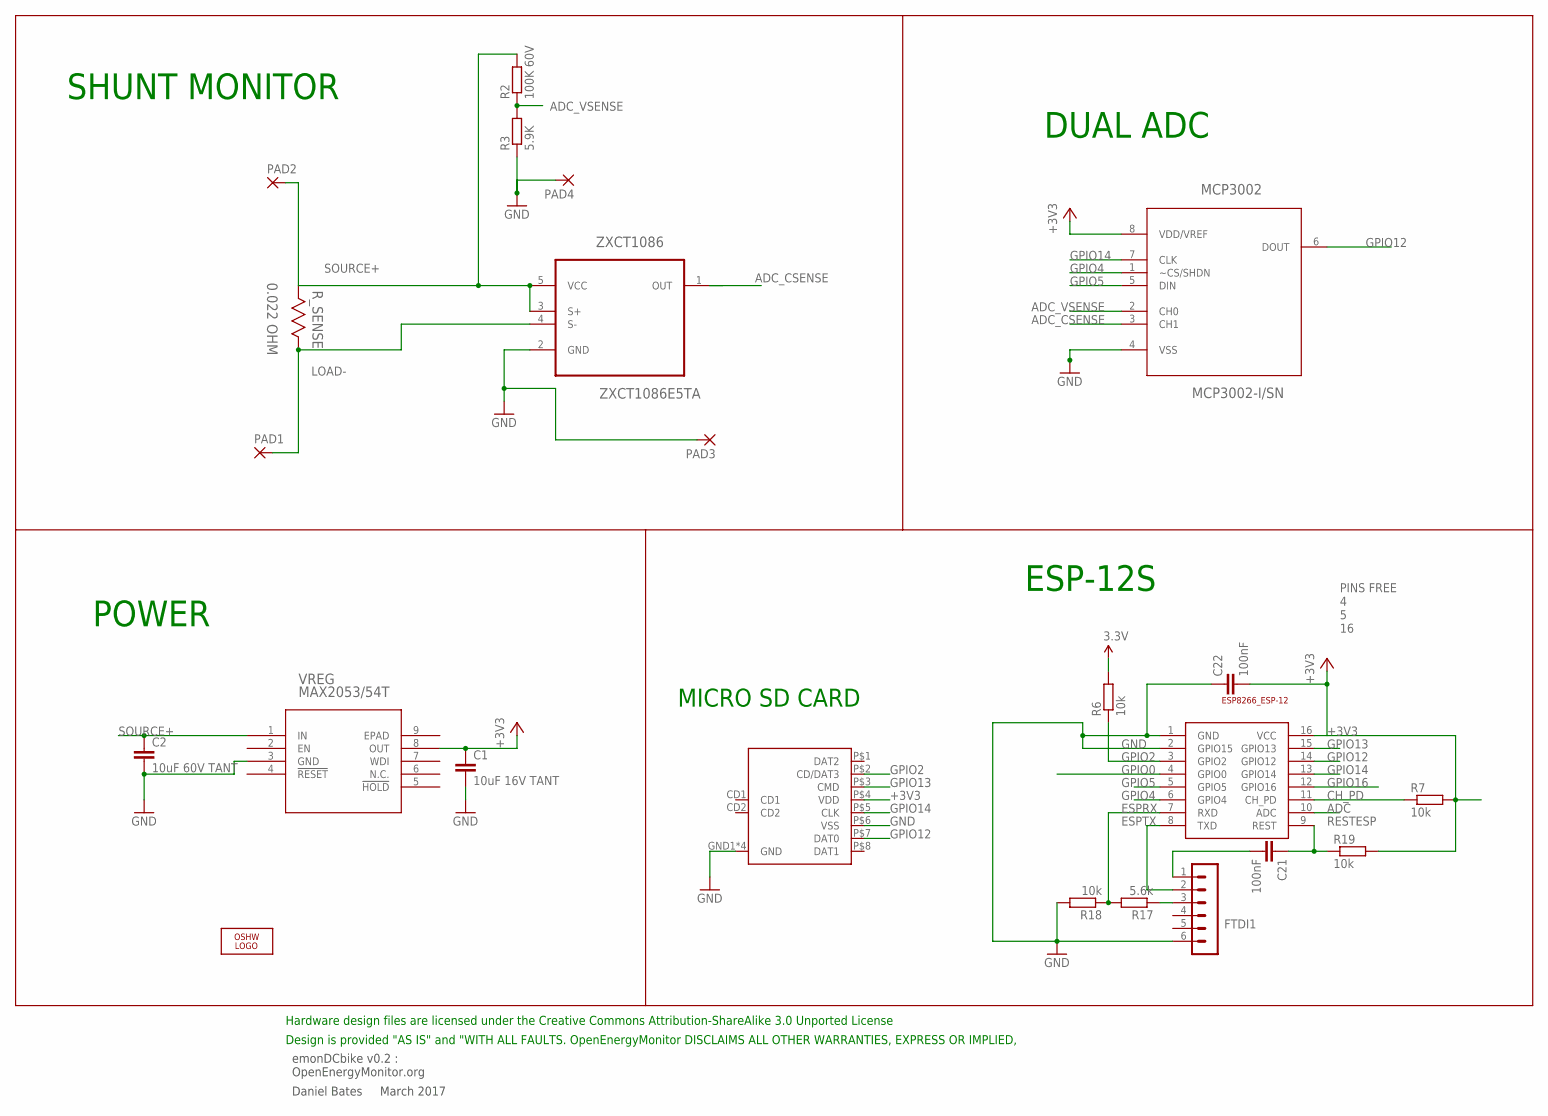
[picture p124: schematic emonBike v0.2.sch]

Parts:
C1: 10uF 16V TANT; C0603
C2: 10uF 60V TANT; C0603
C21, C22: 100nF; C0603
ESP-12: ESP8266_ESP-12; ESP8266-ESP12
FTDI1: FTDI-ESP; MA06-1
LOGO1: OSHW_LOGO_6MILX0200-NT; OSHW_6X200_NOTEXT
MAX2053: MAX5023TASA-T; 21-0111D_SBE-14
MCP3002: MCP3002-I/SN; SOIC127P600X175-8N
PAD1, PAD2, PAD3, PAD4: 3,81/1,4
R2: 100K 60V; R0603; MPN MCWR06X1003FTL
R3: 5.9K; R0603; MPN MCWR06X5901FTL
R6, R7, R18, R19: 10k; R0603
R17: 5.6k; R0603
R_SENSE: 0.022 OHM; RESC3216X71N
U$2: MOLEX_MICRO_SD_1040310811; MOLEX_MICROSD_EXPOSED
ZXCT1086: ZXCT1086E5TA; SOT95P280X130-5N

Connections:
+3V3: C1.1, C22.2, ESP-12.16 (VCC), MAX2053.8 (OUT), MCP3002.8 (VDD/VREF), R6.2, R7.2, R19.2, U$2.P$4 (VDD)
ADC: ESP-12.10 (ADC)
ADC_CSENSE: MCP3002.3 (CH1), ZXCT1086.1 (OUT)
ADC_VSENSE: MCP3002.2 (CH0), R2.1, R3.2
CH_PD: ESP-12.11 (CH_PD), R7.1
ESPRX: ESP-12.7 (RXD), R17.2, R18.1
ESPTX: ESP-12.8 (TXD), FTDI1.2
GND: C1.2, C2.2, C22.1, ESP-12.1 (GND), ESP-12.2 (GPIO15), FTDI1.6, MAX2053.3 (GND), MCP3002.4 (VSS), PAD3.1, PAD4.1, R3.1, R18.2, U$2.GND1 (GND), U$2.GND2 (GND), U$2.GND3 (GND), U$2.GND4 (GND), U$2.P$6 (VSS), ZXCT1086.2 (GND)
GPIO0: ESP-12.4 (GPIO0)
GPIO2: ESP-12.3 (GPIO2), R6.1, U$2.P$2 (CD/DAT3)
GPIO4: ESP-12.6 (GPIO4), MCP3002.1 (~CS/SHDN)
GPIO5: ESP-12.5 (GPIO5), MCP3002.5 (DIN)
GPIO12: ESP-12.14 (GPIO12), MCP3002.6 (DOUT), U$2.P$7 (DAT0)
GPIO13: ESP-12.15 (GPIO13), U$2.P$3 (CMD)
GPIO14: ESP-12.13 (GPIO14), MCP3002.7 (CLK), U$2.P$5 (CLK)
GPIO16: ESP-12.12 (GPIO16)
LOAD-: PAD1.1, R_SENSE.1 (R1), ZXCT1086.4 (S-)
unnamed: C21.2, FTDI1.1
unnamed: FTDI1.3, R17.1
RESTESP: C21.1, ESP-12.9 (REST), R19.1
SOURCE+: C2.1, MAX2053.1 (IN), PAD2.1, R2.2, R_SENSE.2 (R2), ZXCT1086.3 (S+), ZXCT1086.5 (VCC)

Notes on the sheet:
emonDCbike v0.2 : OpenEnergyMonitor.org
Daniel Bates March 2017
Design is provided "AS IS" and "WITH ALL FAULTS. OpenEnergyMonitor DISCLAIMS ALL OTHER WARRANTIES, EXPRESS OR IMPLIED,
Hardware design files are licensed under the Creative Commons Attribution-ShareAlike 3.0 Unported License
SHUNT MONITOR
ESP-12S
MICRO SD CARD
PINS FREE 4 5 16
POWER
DUAL ADC

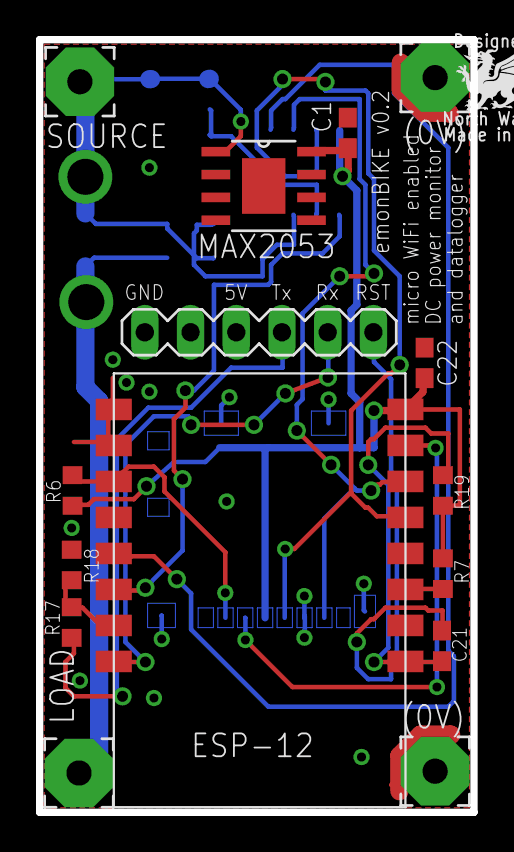
[picture p125: board emonBike v0.2.brd from above]

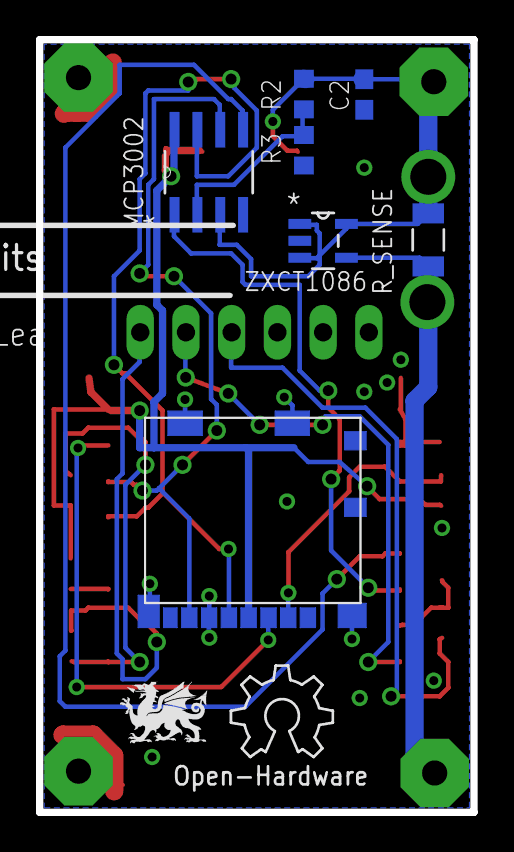
[picture p126: board emonBike v0.2.brd from below]

Board: 2 copper layers, 24.1 x 42.9 mm, 24 parts (9 on the bottom side), 18 nets.

Other parts of the board:
U$3: DRAGON_LOGO_NOTEXT
