danbates2/emonDC/emonDCduo-ESP/emonDCduo-ESP v0.3.brd

## EAGLE design emonDCduo-ESP/emonDCduo-ESP v0.3.brd (2016-12-27)

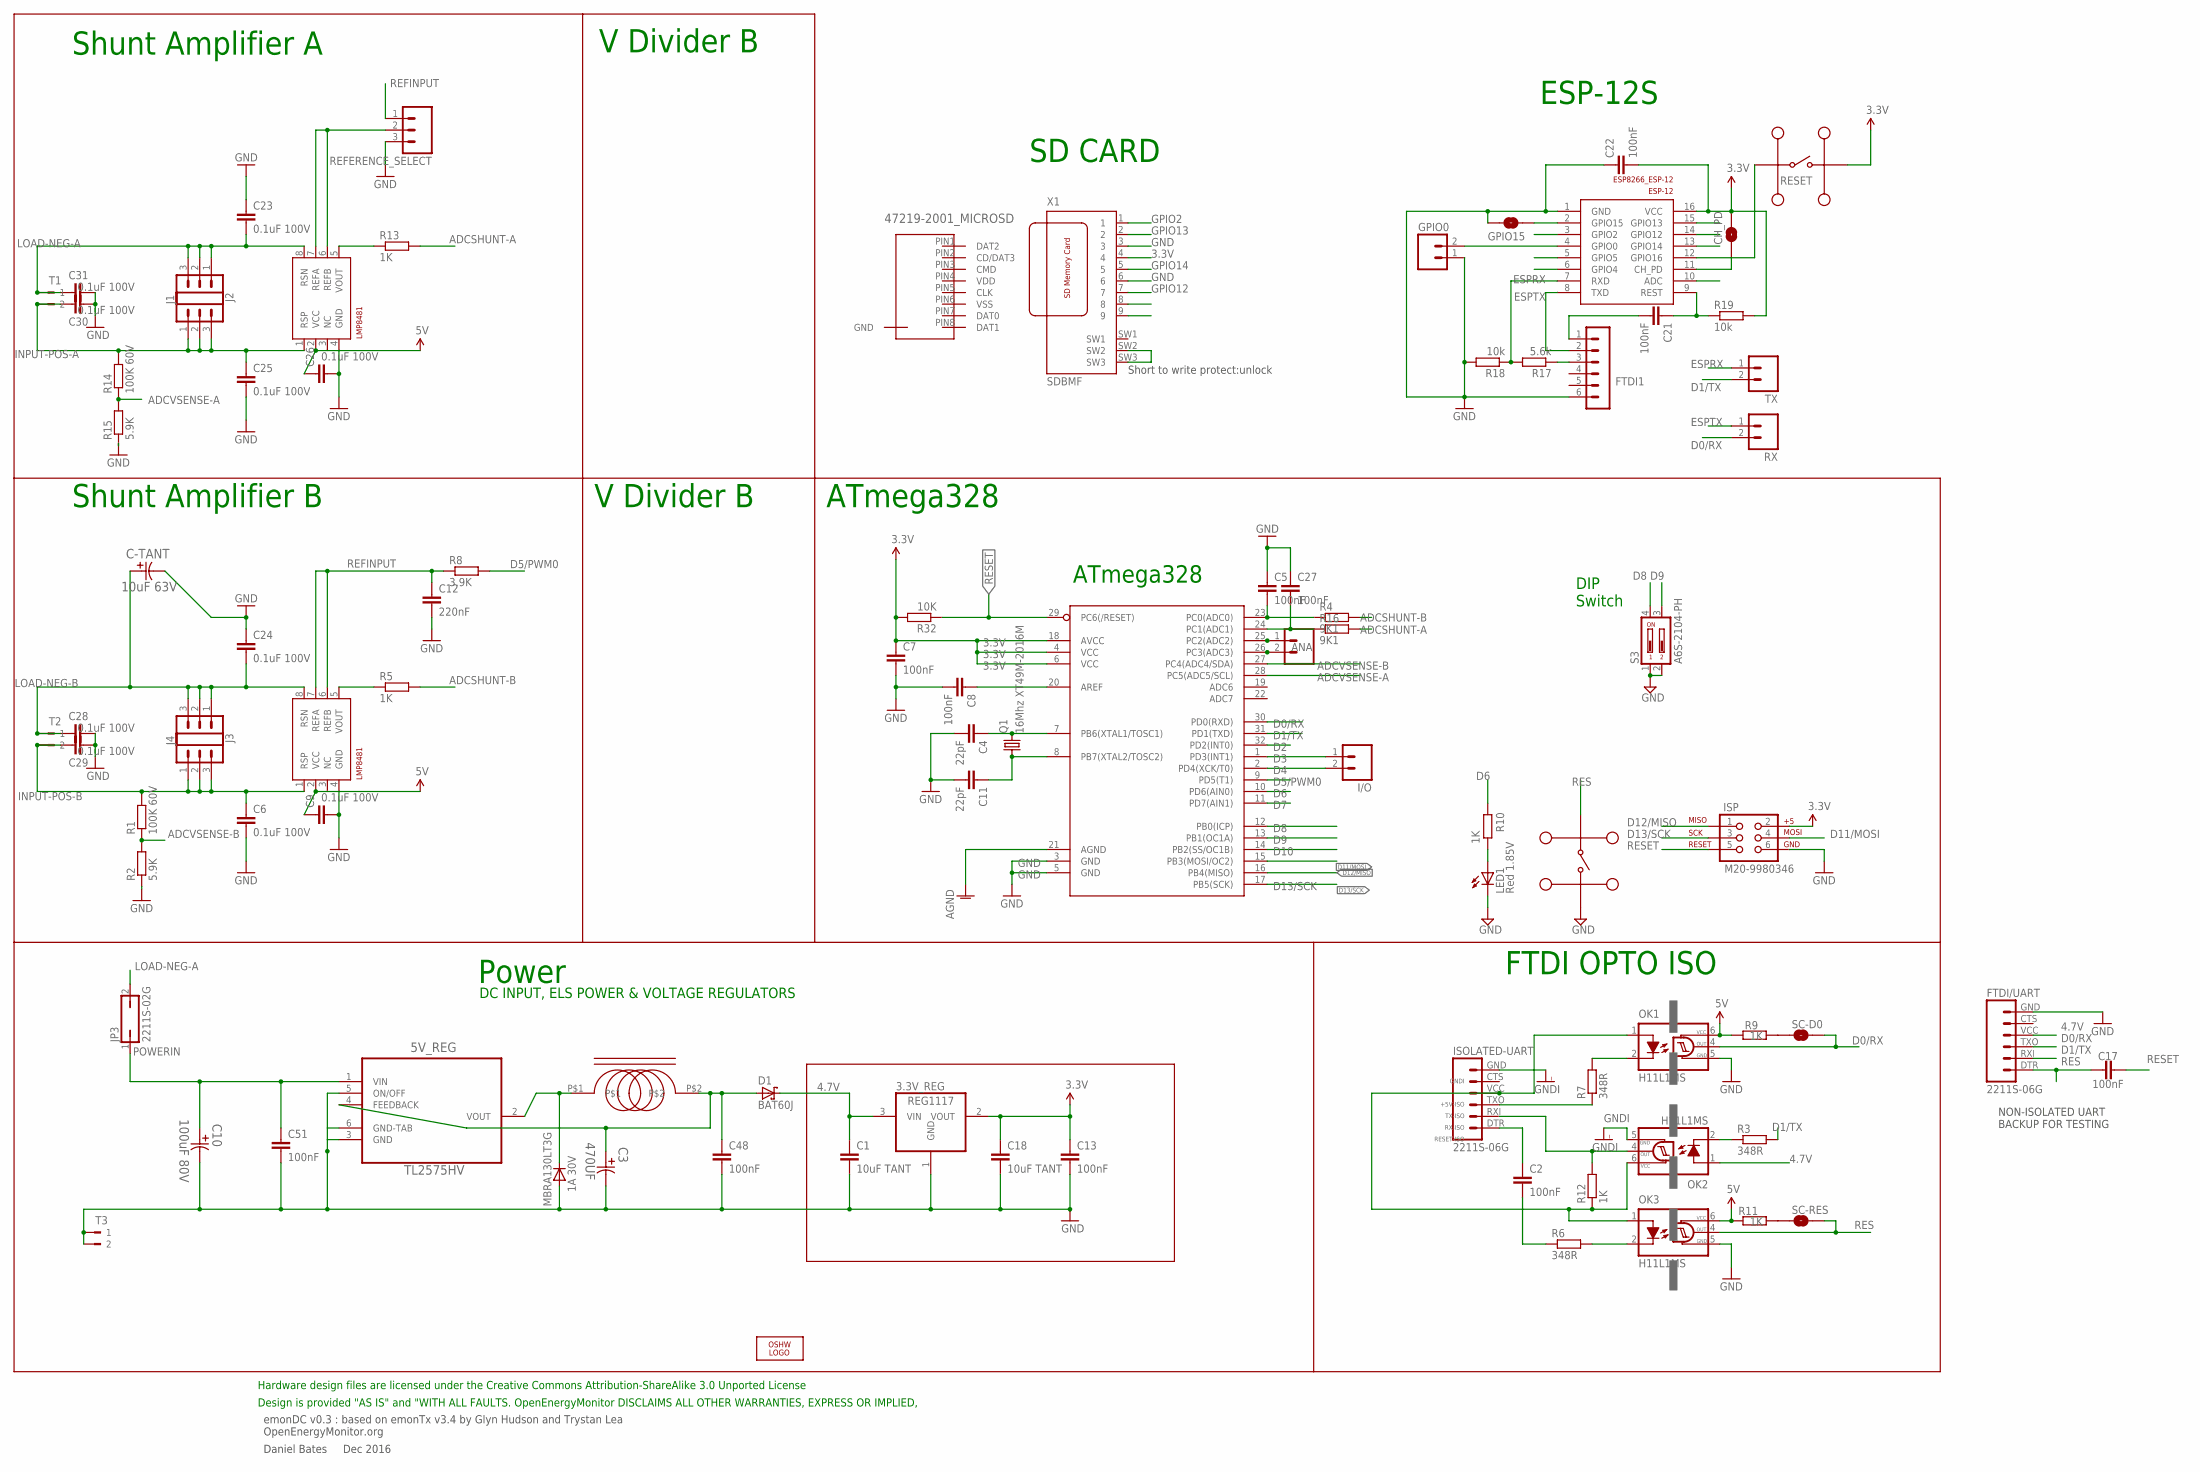
[picture p127: schematic emonDCduo-ESP v0.3.sch]

Parts:
3.3V_REG: REG1117; SOT223
5V_REG: TL2575HV; TO-263; MPN LM2575HVS-15/NOPB
ANA: 2212S-02SG-85; 1X02_LOCK; MPN 2212S-02SG-85
C1, C18: 10uF TANT; C0603
C2, C5, C7, C8, C13, C17, C21, C22, C27, C48, C51: 100nF; C0603
C3: 470UF; CAPAE830X1050N
C4, C11: 22pF; C0603
C6, C9, C23, C24, C25, C26, C28, C29, C30, C31: 0.1uF 100V; C0603; MPN C1608X7S2A104K080AB
C10: 100uF 80V; CAPAE1350X1400N
C12: 220nF; C0603
C-TANT: 10uF 63V; 2917; PARTNO 293D106X0063E2TE3
CH_PD: SOLDERJUMPERNO; SJ_2S-NO
D1: BAT60J; SOD323_ST
D2: MBRA130LT3G; DO-214; MPN MBRA130LT3G
ESP-12: ESP8266_ESP-12; ESP8266-ESP12
FTDI1: FTDI-ESP; MA06-1
FTDI/UART: 2211S-06G; FTDI_BASIC; MPN 2211S-06G
GPIO0: M02PTH; 1X02
GPIO15: SOLDERJUMPERNO; SJ_2S-NO
I1: SRR0603-331KL; MPN SRR0603-331KL
I/O: 2212S-02SG-85; 1X02_LOCK; MPN 2212S-02SG-85
ISOLATED-UART: 2211S-06G; FTDI_BASIC; MPN 2211S-06G
ISP: M20-9980346; 2X3; MPN M20-9980346
J1, J2, J3, J4: CONN_03; 1X03
JP3: 2211S-02G; JP1; MPN 2211S-02G
LED1: Red 1.85V; CHIP-LED0805; MPN SML-211UTT86K
LOGO1: OSHW_LOGO_6MILX0200-NT; OSHW_6X200_NOTEXT
MC1, MC32882: MC32882; SWITCH_TACT_MULTICOMP
OK1, OK2, OK3: H11L1MS; DIL6-SMD
Q1: 16Mhz XT49M-2016M; HC49UP; MPN XT49M-2016M
R1, R14: 100K 60V; R0603; MPN MCWR06X1003FTL
R2, R15: 5.9K; R0603; MPN MCWR06X5901FTL
R3, R6, R7: 348R; R0603
R4, R16: 9K1; R0603
R5, R9, R10, R11, R12, R13: 1K; R0603
R8: 3.9K; R0603
R17: 5.6k; R0603
R18, R19: 10k; R0603
R32: 10K; R0603
REFERENCE_SELECT: 2212S-02SG-85; 1X03; MPN 2212S-02SG-85
RX: M02PTH; 1X02
S3: A6S-2104-PH; DIP_SWITCH_SMT; MPN A6S2104H
SC-D0: SOLDERJUMPERNO; SJ_2S-NO
SC-RES: SOLDERJUMPERNO; SJ_2S-NO
SHUNTMON-A: LMP8481; S-PDSO-G08; MPN LMP8481MME-S/NOPB
SHUNTMON-B: LMP8481; S-PDSO-G08; MPN LMP8481MME-H/NOPB
T1, T2, T3: 180-2
TX: M02PTH; 1X02
U1_TQFP: ATMEGA328P; TQFP32-08; MPN ATMEGA328P-AU
U$1: 47219-2001_MICROSD
X1: SDBMF; SDBMF-009XXBXX2

Connections:
3.3V: 3.3V_REG.2 (VOUT), C7.1, C13.1, C18.1, C22.2, CH_PD.1, ESP-12.16 (VCC), ISP.2, MC1.P$3, MC1.P$4, R19.2, R32.2, U1_TQFP.4 (VCC), U1_TQFP.6 (VCC), U1_TQFP.18 (AVCC), X1.4
4.7V: 3.3V_REG.3 (VIN), C1.1, C9.1, C26.1, D1.C, FTDI/UART.VCC (4), OK1.6 (VCC), OK2.1 (A), OK3.6 (VCC), R9.2, R11.2, SHUNTMON-A.2 (VCC), SHUNTMON-B.2 (VCC)
5.0V: 5V_REG.4 (FEEDBACK), C3.1, C48.1, D1.A, I1.P$2
+5V-ISO: ISOLATED-UART.VCC (4), OK1.1 (A), OK2.6 (VCC), OK3.1 (A), R12.1
ADC2: ANA.1, U1_TQFP.25 (PC2(ADC2))
ADC3: ANA.2, U1_TQFP.26 (PC3(ADC3))
ADCSHUNT-A: R13.2, R16.2
ADCSHUNT-B: R4.2, R5.2
ADCVSENSE-A: R14.1, R15.2, U1_TQFP.28 (PC5(ADC5/SCL))
ADCVSENSE-B: R1.1, R2.2, U1_TQFP.27 (PC4(ADC4/SDA))
AGND: U1_TQFP.21 (AGND)
D0/RX: FTDI/UART.TXO (3), OK1.4 (OUT), RX.2, SC-D0.1, U1_TQFP.30 (PD0(RXD))
D1/TX: FTDI/UART.RXI (2), R3.2, TX.2, U1_TQFP.31 (PD1(TXD))
D2: U1_TQFP.32 (PD2(INT0))
D3: I/O.1, U1_TQFP.1 (PD3(INT1))
D4: I/O.2, U1_TQFP.2 (PD4(XCK/T0))
D5/PWM0: R8.2, U1_TQFP.9 (PD5(T1))
D6: R10.2, U1_TQFP.10 (PD6(AIN0))
D7: U1_TQFP.11 (PD7(AIN1))
D8: S3.4, U1_TQFP.12 (PB0(ICP))
D9: S3.3, U1_TQFP.13 (PB1(OC1A))
D10: U1_TQFP.14 (PB2(SS/OC1B))
D11/MOSI: ISP.4, U1_TQFP.15 (PB3(MOSI/OC2))
D12/MISO: ISP.1, U1_TQFP.16 (PB4(MISO))
D13/SCK: ISP.3, U1_TQFP.17 (PB5(SCK))
ESPRX: ESP-12.7 (RXD), R17.2, R18.1, TX.1
ESPTX: ESP-12.8 (TXD), FTDI1.2, RX.1
GND: 3.3V_REG.1 (GND), 5V_REG.3 (GND), 5V_REG.5 (ON/OFF), 5V_REG.6 (GND-TAB), C1.2, C3.2, C4.2, C5.1, C6.2, C7.2, C8.2, C9.2, C10.2, C11.2, C12.2, C13.2, C18.2, C22.1, C23.1, C24.1, C25.2, C26.2, C27.1, C28.2, C29.2, C30.2, C31.2, C48.2, C51.2, C-TANT.2, D2.P$2 (A), ESP-12.1 (GND), FTDI1.6, FTDI/UART.GND (6), GPIO0.1, GPIO15.2, ISP.6, LED1.C, MC32882.P$3, MC32882.P$4, OK1.5 (GND), OK3.5 (GND), R2.1, R15.1, R18.2, REFERENCE_SELECT.3, S3.1, S3.2, SHUNTMON-A.4 (GND), SHUNTMON-B.4 (GND), T3.1, T3.2, U1_TQFP.3 (GND), U1_TQFP.5 (GND), X1.3, X1.6
GNDI: ISOLATED-UART.GND (6), OK2.5 (GND)
GPIO2: ESP-12.3 (GPIO2), X1.1
GPIO4: ESP-12.6 (GPIO4)
GPIO5: ESP-12.5 (GPIO5)
GPIO12: ESP-12.14 (GPIO12), X1.7
GPIO13: ESP-12.15 (GPIO13), X1.2
GPIO14: ESP-12.13 (GPIO14), X1.5
GPIO16: ESP-12.12 (GPIO16), MC1.P$1, MC1.P$2
IND: 5V_REG.2 (VOUT), D2.P$1 (C), I1.P$1
INPUT-POS-A: C25.1, C30.1, J2.1, J2.2, J2.3, R14.2, SHUNTMON-A.1 (RSP), T1.2
INPUT-POS-B: C6.1, C29.1, J3.1, J3.2, J3.3, R1.2, SHUNTMON-B.1 (RSP), T2.2
LOAD-NEG-A: C23.2, C31.1, J1.1, J1.2, J1.3, JP3.2, SHUNTMON-A.8 (RSN), T1.1
LOAD-NEG-B: C24.2, C28.1, C-TANT.1, J4.1, J4.2, J4.3, SHUNTMON-B.8 (RSN), T2.1
unnamed: C4.1, Q1.2, U1_TQFP.7 (PB6(XTAL1/TOSC1))
unnamed: C5.2, R4.1, U1_TQFP.23 (PC0(ADC0))
unnamed: R11.1, SC-RES.2
unnamed: R13.1, SHUNTMON-A.5 (VOUT)
unnamed: R9.1, SC-D0.2
unnamed: R5.1, SHUNTMON-B.5 (VOUT)
unnamed: ESP-12.2 (GPIO15), GPIO15.1
unnamed: C11.1, Q1.1, U1_TQFP.8 (PB7(XTAL2/TOSC2))
unnamed: C2.1, ISOLATED-UART.DTR (1)
unnamed: X1.SW2, X1.SW3
unnamed: OK1.2 (C), R7.2
unnamed: OK2.2 (C), R3.1
unnamed: OK3.2 (C), R6.2
unnamed: C8.1, U1_TQFP.20 (AREF)
unnamed: C27.2, R16.1, U1_TQFP.24 (PC1(ADC1))
unnamed: REFERENCE_SELECT.2, SHUNTMON-A.6 (REFB), SHUNTMON-A.7 (REFA)
unnamed: ESP-12.4 (GPIO0), GPIO0.2
unnamed: C21.2, FTDI1.1
unnamed: FTDI1.3, R17.1
unnamed: CH_PD.2, ESP-12.11 (CH_PD)
unnamed: C21.1, ESP-12.9 (REST), R19.1
unnamed: LED1.A, R10.1
POWERIN: 5V_REG.1 (VIN), C10.1, C51.1, JP3.1
REFINPUT: C12.1, R8.1, REFERENCE_SELECT.1, SHUNTMON-B.6 (REFB), SHUNTMON-B.7 (REFA)
RES: C17.1, FTDI/UART.DTR (1), MC32882.P$1, MC32882.P$2, OK3.4 (OUT), SC-RES.1
RESET: C17.2, ISP.5, R32.1, U1_TQFP.29 (PC6(/RESET))
RESET-ISO: C2.2, R6.1
RX-ISO: ISOLATED-UART.RXI (2), OK2.4 (OUT), R12.2
TX-ISO: ISOLATED-UART.TXO (3), R7.1

Notes on the sheet:
emonDC v0.3 : based on emonTx v3.4 by Glyn Hudson and Trystan Lea OpenEnergyMonitor.org
Daniel Bates Dec 2016
Power
ATmega328
Design is provided "AS IS" and "WITH ALL FAULTS. OpenEnergyMonitor DISCLAIMS ALL OTHER WARRANTIES, EXPRESS OR IMPLIED,
Hardware design files are licensed under the Creative Commons Attribution-ShareAlike 3.0 Unported License
DIP Switch
FTDI OPTO ISO
DC INPUT, ELS POWER & VOLTAGE REGULATORS
Shunt Amplifier B
V Divider B
Shunt Amplifier A
RESET
ESP-12S
SD CARD
Short to write protect:unlock
NON-ISOLATED UART BACKUP FOR TESTING

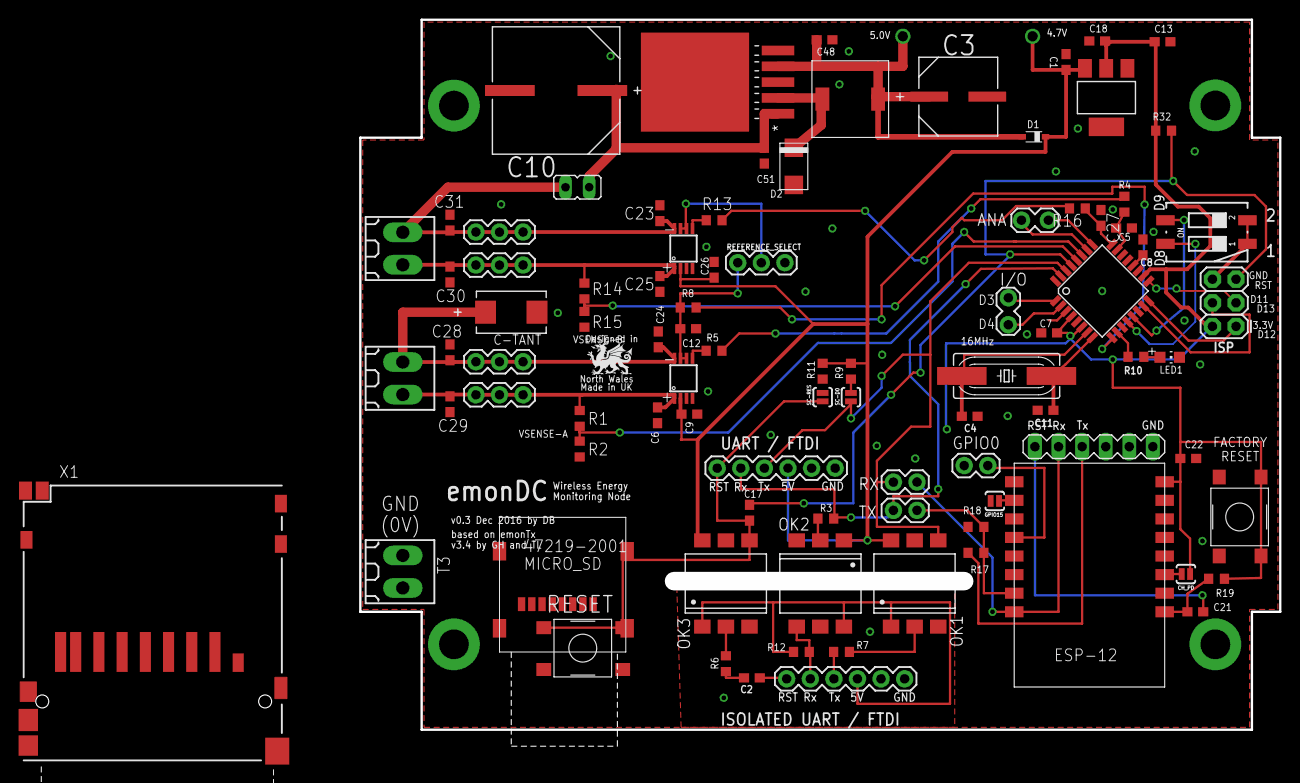
[picture p128: board emonDCduo-ESP v0.3.brd from above]

Board: 2 copper layers, 99.1 x 76.5 mm, 91 parts (1 on the bottom side), 64 nets.
