danbates2/emonDC/emonDCuno/emonDC v0.3.brd

## EAGLE design emonDCuno/emonDC v0.3.brd (2016-12-15)

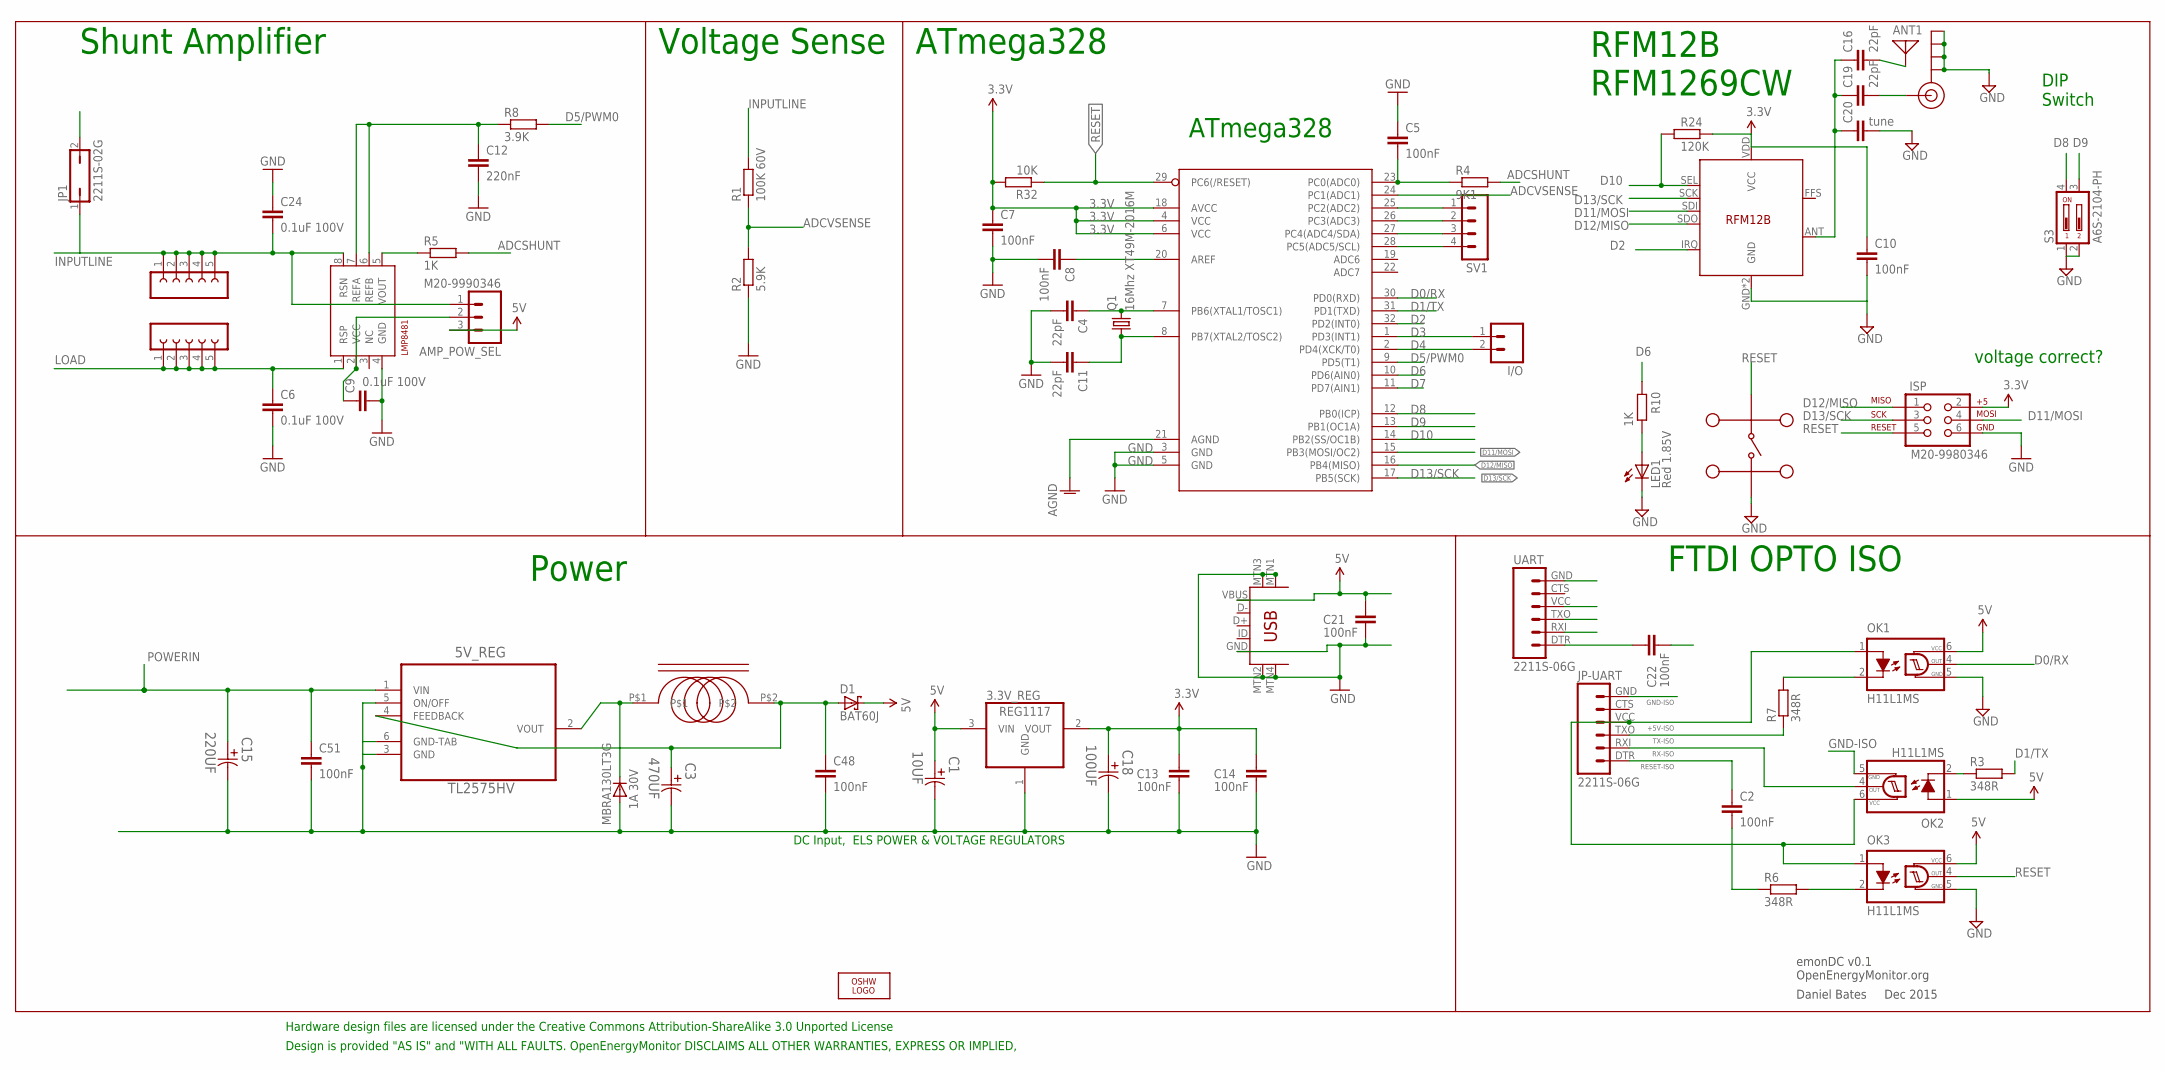
[picture p129: schematic emonDC v0.3.sch]

Parts:
3.3V_REG: REG1117; SOT223
5V_REG: TL2575HV; TO-263; MPN LM2575HVS-15/NOPB
AMP_POW_SEL: M20-9990346; 1X03_SMD_RA_FEMALE_NOWRITE; MPN M20-9990346
ANT1: ANTENNA; PAD-01
C1: 10UF; CAPAE430X610N
C2, C5, C7, C8, C10, C13, C14, C21, C22, C48, C51: 100nF; C0603
C3: 470UF; CAPAE830X1050N
C4, C11, C16, C19: 22pF; C0603
C6, C9, C24: 0.1uF 100V; C0603; MPN C1608X7S2A104K080AB
C12: 220nF; C0603
C15: 220UF; CAPAE1350X1400N
C18: 100UF; CAPAE430X610N
C20: tune; C0603
D1: BAT60J; SOD323_ST
D2: MBRA130LT3G; DO-214; MPN MBRA130LT3G
I1: SRR0603-331KL; MPN SRR0603-331KL
I/O: 2212S-02SG-85; 1X02_LOCK; MPN 2212S-02SG-85
ISP: M20-9980346; 2X3; MPN M20-9980346
J$1: SMA_EDGE; SMA-EDGE
JP1: 2211S-02G; JP1; MPN 2211S-02G
JP-LOAD: 2212S-06SG-85; FE05-1; MPN 2212S-06SG-85
JP-SOURCE: 2212S-06SG-85; FE05-1; MPN 2212S-06SG-85
JP-UART: 2211S-06G; FTDI_BASIC; MPN 2211S-06G
LED1: Red 1.85V; CHIP-LED0805; MPN SML-211UTT86K
LMP8481: LMP8481SMCLMP8481; S-PDSO-G08; MPN LMP8481MME-S/NOPB
LOGO1: OSHW_LOGO_6MILX0200-NT; OSHW_6X200_NOTEXT
MC32882: MC32882; SWITCH_TACT_MULTICOMP
OK1, OK2, OK3: H11L1MS; DIL6-SMD
Q1: 16Mhz XT49M-2016M; HC49UP; MPN XT49M-2016M
R1: 100K 60V; R0603; MPN MCWR06X1003FTL
R2: 5.9K; R0603; MPN MCWR06X5901FTL
R3, R6, R7: 348R; R0603
R4: 9K1; R0603
R5, R10: 1K; R0603
R8: 3.9K; R0603
R24: 120K; R0603
R32: 10K; R0603
RF: RFM12B
S3: A6S-2104-PH; DIP_SWITCH_SMT; MPN A6S2104H
SV1: MA04-1
U1_TQFP: ATMEGA328P; TQFP32-08; MPN ATMEGA328-AU
UART: 2211S-06G; FTDI_BASIC; MPN 2211S-06G
USB: MUSB-05-S-B-SM-A; USB-MINIB-CISECO; MPN 67503-1020

Connections:
3.3V: 3.3V_REG.2 (VOUT), C7.1, C10.1, C13.1, C14.1, C18.1, ISP.2, R24.2, R32.2, RF.VDD (VCC), U1_TQFP.4 (VCC), U1_TQFP.6 (VCC), U1_TQFP.18 (AVCC)
5VHIGH: 5V_REG.4 (FEEDBACK), C3.1, C48.1, D1.A, I1.P$2
5VLOW: 3.3V_REG.3 (VIN), AMP_POW_SEL.3, C1.1, C21.1, D1.C, OK1.6 (VCC), OK2.1 (A), OK3.6 (VCC), UART.VCC (4), USB.VBUS
+5V-ISO: JP-UART.VCC (4), OK1.1 (A), OK2.6 (VCC), OK3.1 (A)
ADC2: SV1.1, U1_TQFP.25 (PC2(ADC2))
ADC3: SV1.2, U1_TQFP.26 (PC3(ADC3))
ADC4: SV1.3, U1_TQFP.27 (PC4(ADC4/SDA))
ADC5: SV1.4, U1_TQFP.28 (PC5(ADC5/SCL))
ADCSHUNT: R4.2, R5.2
ADCVSENSE: R1.1, R2.2, U1_TQFP.24 (PC1(ADC1))
AGND: U1_TQFP.21 (AGND)
D0/RX: OK1.4 (OUT), U1_TQFP.30 (PD0(RXD)), UART.TXO (3)
D1/TX: R3.2, U1_TQFP.31 (PD1(TXD)), UART.RXI (2)
D2: RF.IRQ, U1_TQFP.32 (PD2(INT0))
D3: I/O.1, U1_TQFP.1 (PD3(INT1))
D4: I/O.2, U1_TQFP.2 (PD4(XCK/T0))
D5/PWM0: R8.2, U1_TQFP.9 (PD5(T1))
D6: R10.2, U1_TQFP.10 (PD6(AIN0))
D7: U1_TQFP.11 (PD7(AIN1))
D8: S3.4, U1_TQFP.12 (PB0(ICP))
D9: S3.3, U1_TQFP.13 (PB1(OC1A))
D9/PWM1: C12.1, LMP8481.6 (REFB), LMP8481.7 (REFA), R8.1
D10: R24.1, RF.SEL, U1_TQFP.14 (PB2(SS/OC1B))
D11/MOSI: ISP.4, RF.SDI, U1_TQFP.15 (PB3(MOSI/OC2))
D12/MISO: ISP.1, RF.SDO, U1_TQFP.16 (PB4(MISO))
D13/SCK: ISP.3, RF.SCK, U1_TQFP.17 (PB5(SCK))
DIG1: C16.1, C19.1, C20.1, RF.ANT
GND: 3.3V_REG.1 (GND), 5V_REG.3 (GND), 5V_REG.5 (ON/OFF), 5V_REG.6 (GND-TAB), C1.2, C3.2, C4.2, C5.1, C6.2, C7.2, C8.2, C9.2, C10.2, C11.2, C12.2, C13.2, C14.2, C15.2, C18.2, C20.2, C21.2, C24.1, C48.2, C51.2, D2.P$2 (A), ISP.6, J$1.GND@0 (GND), J$1.GND@1 (GND), J$1.GND@2 (GND), J$1.GND@3 (GND), LED1.C, LMP8481.4 (GND), MC32882.P$3, MC32882.P$4, OK1.5 (GND), OK3.5 (GND), R2.1, RF.GND, RF.P$12 (GND), S3.1, S3.2, U1_TQFP.3 (GND), U1_TQFP.5 (GND), UART.GND (6), USB.GND, USB.MTN1 (MTN2), USB.MTN2 (MTN3), USB.MTN3 (MTN1), USB.MTN4
GND-ISO: JP-UART.GND (6), OK2.5 (GND)
IND: 5V_REG.2 (VOUT), D2.P$1 (C), I1.P$1
INPUTLINE: AMP_POW_SEL.1, C24.2, JP1.1, JP-SOURCE.1, JP-SOURCE.2, JP-SOURCE.3, JP-SOURCE.4, JP-SOURCE.5, LMP8481.8 (RSN), R1.2
LOAD: C6.1, JP-LOAD.1, JP-LOAD.2, JP-LOAD.3, JP-LOAD.4, JP-LOAD.5, LMP8481.1 (RSP)
unnamed: C4.1, Q1.2, U1_TQFP.7 (PB6(XTAL1/TOSC1))
unnamed: C5.2, R4.1, U1_TQFP.23 (PC0(ADC0))
unnamed: C22.1, UART.DTR (1)
unnamed: LMP8481.5 (VOUT), R5.1
unnamed: AMP_POW_SEL.2, C9.1, LMP8481.2 (VCC)
unnamed: C11.1, Q1.1, U1_TQFP.8 (PB7(XTAL2/TOSC2))
unnamed: C2.1, JP-UART.DTR (1)
unnamed: ANT1.1, C16.2
unnamed: OK1.2 (C), R7.2
unnamed: OK2.2 (C), R3.1
unnamed: OK3.2 (C), R6.2
unnamed: C8.1, U1_TQFP.20 (AREF)
unnamed: C19.2, J$1.SIG (SIGNAL)
unnamed: LED1.A, R10.1
POWERIN: 5V_REG.1 (VIN), C15.1, C51.1, JP1.2
RESET: C22.2, ISP.5, MC32882.P$1, MC32882.P$2, OK3.4 (OUT), R32.1, U1_TQFP.29 (PC6(/RESET))
RESET-ISO: C2.2, R6.1
RX-ISO: JP-UART.RXI (2), OK2.4 (OUT)
TX-ISO: JP-UART.TXO (3), R7.1

Notes on the sheet:
emonDC v0.1 OpenEnergyMonitor.org
Daniel Bates Dec 2015
Power
ATmega328
Design is provided "AS IS" and "WITH ALL FAULTS. OpenEnergyMonitor DISCLAIMS ALL OTHER WARRANTIES, EXPRESS OR IMPLIED,
Hardware design files are licensed under the Creative Commons Attribution-ShareAlike 3.0 Unported License
RFM12B RFM1269CW
DIP Switch
FTDI OPTO ISO
DC Input, ELS POWER & VOLTAGE REGULATORS
Shunt Amplifier
voltage correct?
Voltage Sense

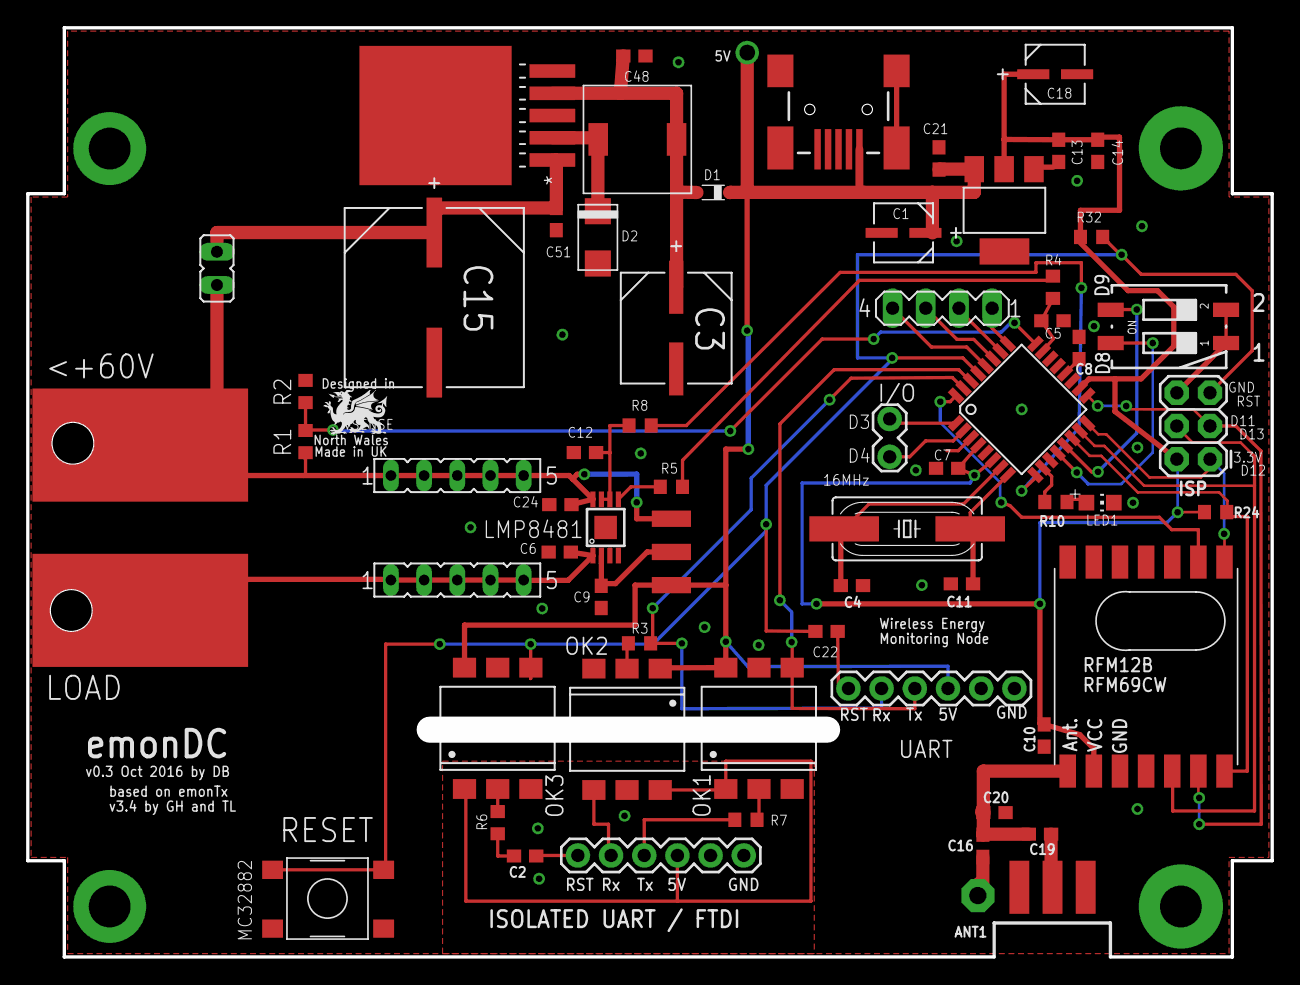
[picture p130: board emonDC v0.3.brd from above]

Board: 2 copper layers, 95.2 x 71.1 mm, 63 parts (1 on the bottom side), 49 nets.
