danbates2/emonDC/emonDCduo/emonDCduo-ESP v1.0.brd

## EAGLE design emonDCduo/emonDCduo-ESP v1.0.brd (2017-07-30)

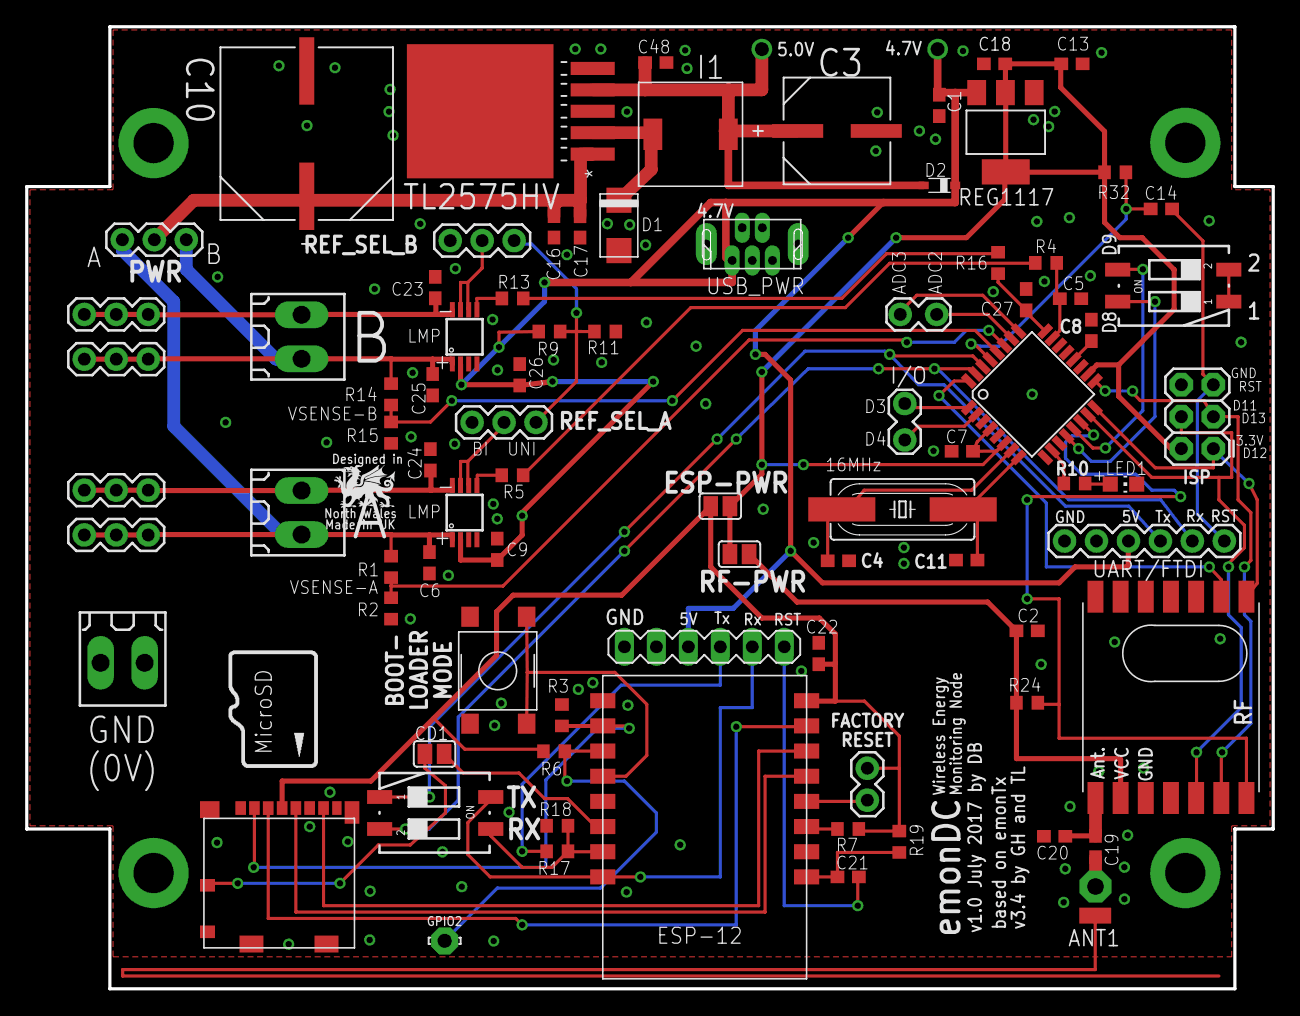
[picture p131: board emonDCduo-ESP v1.0.brd from above]

Board: 2 copper layers, 99.1 x 76.5 mm, 85 parts (1 on the bottom side), 60 nets.

Parts:
ANA: 2212S-02SG-85; 1X02_LOCK
ANT1: PAD-01
C1, C18: 10uF TANT; C0603
C2, C5, C7, C8, C9, C13, C14, C21, C22, C26, C27, C48: 100nF; C0603
C3: 470uF 16V; CAPAE830X1050N
C4, C11, C19: 22pF; C0603
C6, C16, C17, C23, C24, C25: 0.1uF 100V; C0603
C10: 100uF 80V; CAPAE1350X1400N
C20: tune; C0603
CD1: SJ
D1: MBRA130LT3G; DO-214
D2: BAT60J; SOD323_ST
ESP-12: ESP8266_ESP-12; ESP8266-ESP12
ESP-PWR: SJ
FTDI1: FTDI-ESP; MA06-1
FTDI/UART: 2211S-06G; FTDI_BASIC
GPIO2: LSP11
I1: 330uH; SRR0603-331KL
I/O: 2212S-02SG-85; 1X02_LOCK
IO1: 1X02
ISP: M20-9980346; 2X3
J1, J2, J3, J4: 1X03
LED1: Red 1.85V; CHIP-LED0805
LOGO1: OSHW_LOGO_6MILX0200-NT; OSHW_6X200_NOTEXT
MC2: MC32882; SWITCH_TACT_MULTICOMP
MINI_USB-B: 5000751517_SD
PAD1: SMD1,27-2,54
PWR: 1X03
Q1: 16Mhz XT49M-2016M; HC49UP
R1, R14: 100K 75V; R0603
R2, R15, R17: 5.6K; R0603
R3, R6, R7, R9, R18, R19: 10K; R0603
R4, R16: 9K1; R0603
R5, R10, R13: 1K; R0603
R11: 30K; R0603
R24: 120K; R0603
R32: 10k; R0603
REF_SEL_A: 2212S-02SG-85; 1X03
REF_SEL_B: 2212S-02SG-85; 1X03
REG1117: REG1117-3.3V; SOT223
RF: RFM12B
RF-PWR: SJ
S1, S3: A6S-2104-PH; DIP_SWITCH_SMT
SHUNTMON-A: LMP8481; S-PDSO-G08
SHUNTMON-B: LMP8481; S-PDSO-G08
T1, T2, T3: 180-2
TL2575HV: TL2575HV-5V; TO-263
U1_TQFP: ATMEGA328P; TQFP32-08
U$2: MOLEX_MICRO_SD_1040310811; MOLEX_MICROSD_EXPOSED

Connections:
3.3V: C7.1, C13.1, C18.1, ESP-PWR.2, ISP.2, R32.2, REG1117.2, REG1117.4, RF-PWR.1, U1_TQFP.4, U1_TQFP.6, U1_TQFP.18
3.3V-ESP: C22.2, ESP-12.16, ESP-PWR.1, IO1.2, R6.2, R7.2, R19.2, U$2.P$4
3.3V-RF: C2.1, R24.2, RF.VDD, RF-PWR.2
4.7V: C1.1, C9.1, C26.1, D2.C, FTDI1.4, FTDI/UART.VCC, MINI_USB-B.VBUS, R9.2, REG1117.3, SHUNTMON-A.2, SHUNTMON-B.2
5.0V: C3.1, C48.1, D2.A, I1.P$2, TL2575HV.4
ADC0: C5.2, R4.1, U1_TQFP.23
ADC1: C27.2, R16.1, U1_TQFP.24
ADC2: ANA.1, U1_TQFP.25
ADC3: ANA.2, U1_TQFP.26
ADC4-VSENSEA: R1.1, R2.2, U1_TQFP.27
ADC5-VSENSEB: R14.1, R15.2, U1_TQFP.28
ADCSHUNT-A: R4.2, R5.2
ADCSHUNT-B: R13.2, R16.2
CH_PD: ESP-12.11, R7.1
D0/RX: FTDI/UART.TXO, S1.1, U1_TQFP.30
D1/TX: FTDI/UART.RXI, S1.2, U1_TQFP.31
D2: RF.IRQ, U1_TQFP.32
D3: I/O.1, U1_TQFP.1
D4: I/O.2, U1_TQFP.2
D6: R10.2, U1_TQFP.10
D8: S3.4, U1_TQFP.12
D9: S3.3, U1_TQFP.13
D10: R24.1, RF.SEL, U1_TQFP.14
D11/MOSI: ISP.4, RF.SDI, U1_TQFP.15
D12/MISO: ISP.1, RF.SDO, U1_TQFP.16
D13/SCK: ISP.3, RF.SCK, U1_TQFP.17
DIG1: C19.1, C20.1, RF.ANT
ESPRX: ESP-12.7, R17.2, R18.1, S1.3
ESPTX: ESP-12.8, FTDI1.2, S1.4
GND: C1.2, C2.2, C3.2, C4.2, C5.1, C6.2, C7.2, C8.2, C9.2, C10.2, C11.2, C13.2, C16.2, C17.2, C18.2, C20.2, C22.1, C23.1, C24.1, C25.2, C26.2, C27.1, C48.2, D1.P$2, ESP-12.1, FTDI1.6, FTDI/UART.GND, ISP.6, LED1.C, MC2.P$1, MC2.P$2, MINI_USB-B.GND1, MINI_USB-B.GND2, MINI_USB-B.GND3, R2.1, R3.2, R11.1, R15.1, R18.2, REF_SEL_A.3, REF_SEL_B.1, REG1117.1, RF.GND, RF.P$12, S3.1, S3.2, SHUNTMON-A.4, SHUNTMON-B.4, T3.1, T3.2, TL2575HV.3, TL2575HV.5, TL2575HV.6, U1_TQFP.3, U1_TQFP.5, U$2.CD2, U$2.GND1, U$2.GND2, U$2.GND3, U$2.GND4, U$2.P$6
GPIO0: ESP-12.4, MC2.P$3, MC2.P$4
GPIO2: ESP-12.3, GPIO2.MP, R6.1
GPIO4: CD1.2, ESP-12.6
GPIO12: ESP-12.14, U$2.P$7
GPIO13: ESP-12.15, U$2.P$3
GPIO14: ESP-12.13, U$2.P$5
GPIO15: ESP-12.2, R3.1, U$2.P$2
GPIO16: ESP-12.12, IO1.1
IND: D1.P$1, I1.P$1, TL2575HV.2
LOAD-NEG-A: C24.2, J4.1, J4.2, J4.3, SHUNTMON-B.8, T2.1
LOAD-NEG-B: C23.2, J1.1, J1.2, J1.3, SHUNTMON-A.8, T1.1
unnamed: C4.1, Q1.2, U1_TQFP.7
unnamed: ANT1.1, C19.2
unnamed: R13.1, SHUNTMON-A.5
unnamed: R5.1, SHUNTMON-B.5
unnamed: C11.1, Q1.1, U1_TQFP.8
unnamed: CD1.1, U$2.CD1
unnamed: C8.1, U1_TQFP.20
unnamed: C21.2, FTDI1.1
unnamed: FTDI1.3, R17.1
unnamed: LED1.A, R10.1
PWR_IN: C10.1, C16.1, C17.1, PWR.2, TL2575HV.1
REF_A_INPUT: REF_SEL_A.2, SHUNTMON-B.6, SHUNTMON-B.7
REF_B_INPUT: REF_SEL_B.2, SHUNTMON-A.6, SHUNTMON-A.7
REF_INPUT: R9.1, R11.2, REF_SEL_A.1, REF_SEL_B.3
RESET1: C14.2, FTDI/UART.DTR, ISP.5
RESET2: C14.1, R32.1, U1_TQFP.29
RESTESP: C21.1, ESP-12.9, R19.1
SOURCE-POS-A: C6.1, J3.1, J3.2, J3.3, PWR.1, R1.2, SHUNTMON-B.1, T2.2
SOURCE-POS-B: C25.1, J2.1, J2.2, J2.3, PWR.3, R14.2, SHUNTMON-A.1, T1.2
